GeoKrom/NTUA-Intelligent-Control-Systems-and-Robotic-Systems-course/Exercises/Exercise-4/Assignment 4.pdf

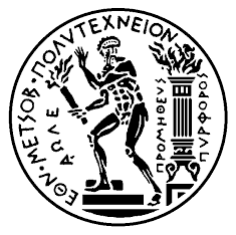
[picture p115: figure]

Εθνικό Μετσόβιο Πολυτεχνείο

Σχολή Μηχανολόγων μηχανικών

ΔΠΜΣ Συστήματα αυτοματισμού

Κατεύθυνση Β: Συστήματα Αυτομάτου Ελέγχου και Ρομποτικής

Μεταπτυχιακό Μάθημα:

Ευφυή Συστήματα Ελέγχου και Ρομποτικής

Ονομ/νυμο - Α.Μ.:

Γεώργιος Κρομμύδας - 02121208

Τέταρτη Σειρά Ασκήσεων: Backstepping and Adaptive Backstepping Control

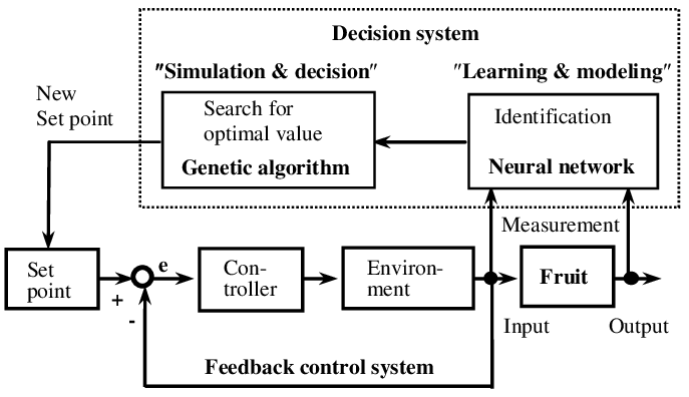
[picture p116: figure]

### Αθήνα, 2024

# Πίνακας Περιεχομένων

Κατάλογος Σχημάτων | | 2
Κατάλογος Πινάκων | | 3
΄Ελεγχος Ρομποτικού Βραχίονα Περιστροφικών Αρθρώσεων | | 4
Ερώτημα 1: Ελεγκτής Ρομποτικού Βραχίονα με την Μέθοδο Οπισθοδρόμησης | . | 5

Ερώτημα 2: Ελεγκτής Ρομποτικού βραχίονα με την Μέθοδο Προσαρμοσικής

Αʹ Κώδικας Προσομοίωσης | 15
Βιβλιογραφία | 25

# Κατάλογος Σχημάτων

1 | Ρομποτικός βραχίονας n βαθμών ελευθερίας | | 4
2 | Ρομποτικός βραχίονας δύο βαθμών ελευθερίας | | 8
3 | Γωνιακή θέση και ταχύτητα στροφικής άρθρωσης q1 | | 11
4 | Γωνιακή θέση και ταχύτητα στροφικής άρθρωσης q2 | | 11
5 | Σφάλματα παρακολούθησης γωνιακών θέσεων και ταχυτήτων στροφικών αρ-
θρώσεων. | | | 12
6 | Γωνιακή θέση και ταχύτητα στροφικής άρθρωσης q1 | | 13
7 | Γωνιακή θέση και ταχύτητα στροφικής άρθρωσης q2 | | 13
8 | Σφάλματα παρακολούθησης γωνιακών θέσεων και ταχυτήτων στροφικών αρ-
θρώσεων. | | | 13
9 | Εκτίμηση παραμέτρων ρομποτικού βραχίονα | | 14

# Κατάλογος Πινάκων

1 | Περιγραφή συμβόλων ρομποτικού βραχίονα | | 8
2 | Τιμές παραμέτρων ρομποτικού βραχίονα | | 10

# ΄Ελεγχος Ρομποτικού Βραχίονα

# Περιστροφικών Αρθρώσεων

Μας δίνεται ένας ρομποτικός βραχίονας n βαθμών ελευθερίας περιστροφικών αρθρώσεων που

περιγράφεται από το ακόλουθο δυναμικό μοντέλο:

M(q)¨q + C(q, q˙) ˙q + G(q) = τ | (1)

όπου τα q, τ ∈ Rn περιγράφουν τις γωνίες και τις ροπές εισόδου κάθε άρθρωσης, M(q) είναι

ο πίνακας μάζας του βραχίονα, C(q, q˙) είναι ο πίνακας φυγόκεντρων και Coriolis δυνάμεων

και ο G(q) αποτελεί το διάνυσμα των βαρυτηκών δυνάμεων (βλ. Σχήμα 1).

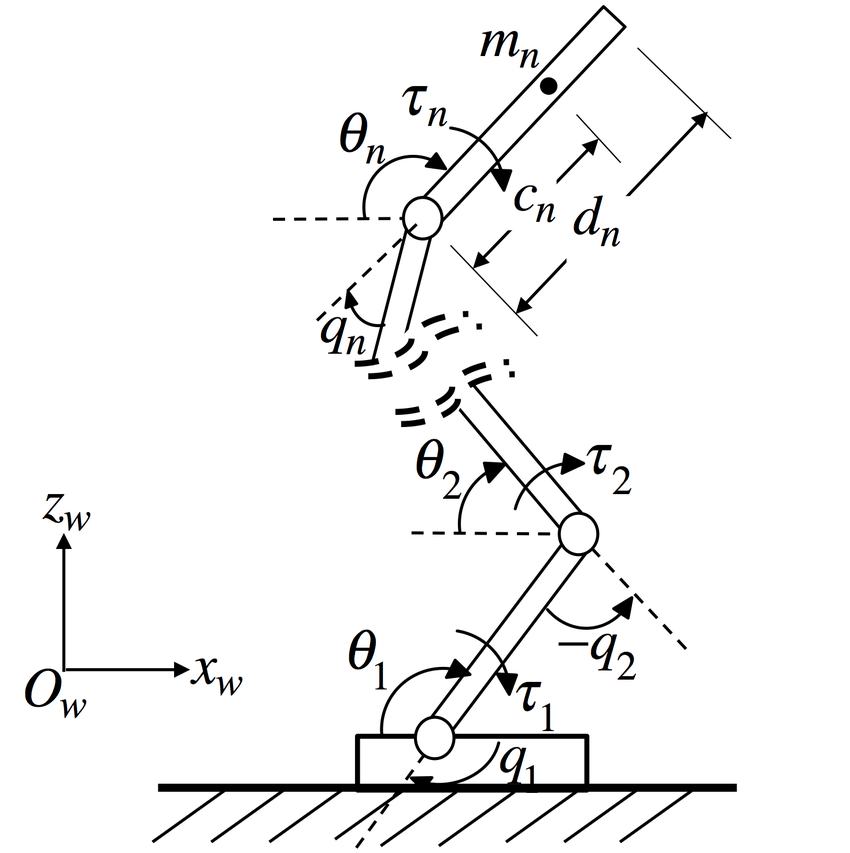
[picture p117: figure]

Σχήμα 1: Ρομποτικός βραχίονας n βαθμών ελευθερίας.

Επιπλέον, ο παραπάνω βραχίονας έχει τις ακόλουθες ιδιότητες:

1. Ο πίνακας M(q) ∈ Rn×n
είναι συμμετρικός και θετικά ορισμένος.
2. Ο πίνακας N(q) := M˙ (q) − 2C(q, q˙) ∈ Rn×n
είναι αντισυμμετρικός και ισχύει
q

T N(q)q = 0.

3. Το δυναμικό μοντέλο της σχέσης (1) του βραχίονα παραμετροποιείται γραμμικά ως εξής:

M(q)¨qr + C(q, q˙) ˙qr + G(q) = Y (q, q,˙ qṙ, q¨r)π

όπου το π ∈ Rm αποτελεί το διάνυσμα των άγνωστων σταθερών παραμέτρων και η Y : Rn×Rn×Rn×Rn → Rn×m είναι μια γνωστή συνάρτηση των παραπάνω σημάτων.

Ερώτημα 1: Ελεγκτής Ρομποτικού Βραχίονα με τη Μέθοδο Οπισθοδρόμησης

Το πρώτο βήμα είναι να μετασχηματίσουμε τη σχέση (1) σε μητρωϊκή μορφή, για να μπο-

ρέσουμε να κάνουμε παρακολούθηση τροχιάς. Συνεπώς, θέτουμε το διάνυσμα κατάστασης
x = [q, q˙]

T
. Οπότε Το σύστημα θα γίνει
x˙ 1
x˙ 2
=
q˙
M⁻¹
(q) (τ − C(q, q˙) ˙q − G(q)) (2)

Η αντιστροφή του πίνακα μάζας έγινε με βάση την ιδιότητά του, ο οποίος είναι θετικά ορι-

σμένος. Καθώς γνωρίζουμε την επιθυμητή τροχιά που θέλουμε να εφαρμόσουμε στο σύστημα,

ορίζουμε τα παρακάτω σφάλματα
e1 = q − qd

e2 = ˙q − qḋ

΄Ετσι, η δυναμική του σφάλματος που θα προκύψει θα είναι η εξής
e˙1
e˙2
=
q˙ − qḋ
q¨− q¨d
=
e2
M⁻¹
(q) (τ − C(q, q˙) ˙q − G(q)) − q¨d

=

e2
M⁻¹
(q) (τ − C(q, q˙) ˙q − G(q)) − M⁻¹
(q) (Y (q, q,˙ q,˙ q¨d)π − C(q, q˙) ˙q − G(q))
e˙1
e˙2
=
e2
M⁻¹
(q) (τ − Y (q, q,˙ q,˙ q¨d)π)
(3)

Συνεπώς, με βάση τη σχέση (3) θα μπορέσουμε να σχεδιάσουμε τον ελεγκτή οπισθο-

δρόμησης. Η αρχική κατάσταση του συστήματος θα είναι z1 = e1. Οπότε

z˙1 = ė1 = e2 = e2 ± K1e1 = −K1z1 + (e2 + K1z1)

όπου ο πίνακας K1 ∈ Rn×n
είναι συμμετρικός και θετικά ορισμένος. Θεωρούμε τη μεταβλη-

τή e2 ως είσοδο ελέγχου στο σύστημα. Για να έχουμε ευστάθεια στην πρώτη κατάσταση, ορίζουμε το e2 = −K1z1. ΄Ετσι θα προκύψει

z˙1 = −K1z1

το οποίο σημαίνει πως θα προκύψει ευστάθεια λόγω του ορισμού του πίνακα K1. ΄Ετσι, θα

ορίσουμε τη νέα μεταβλητή κατάστασης ως z2 = e2 + K1z1. Θα παραγωγίσουμε τη σχέση

αυτή, με αποτέλεσμα να προκύψει

z˙2 = ė2 + K1z˙1 = M⁻¹
(q)(τ − Y (q, q,˙ q,˙ q¨d)π) + K1(z2 − K1z1) | (4)

Οπότε, τώρα θα κάνουμε χρήση της υποψήφιας συνάρτησης Lyapunov

V (z1, z2) = 1
2

z

T
1

z1 +

1
2

z

T
2 M(q)z2 | (5)

Η παραπάνω συνάρτηση παρατηρούμε πως είναι θετικά ορισμένη στο πεδίο ορισμού της και

ακτινικά μη φραγμένη. Οπότε, το επόμενο βήμα είναι να την παραγωγίσουμε

V˙ (z1, z2) = z
T
1

z˙1 +

1
2

z˙

T
2 M(q)z2 +

1
2

z

T

2 M˙ (q)z2 +

1
2

z

T
2 M(q) ż2

= z

T
1

(z2 − K1z1) + 1
2

(M⁻¹
(q)(τ − Y (q, q,˙ q,˙ q¨d)π) + K1(z2 − K1z1))TM(q)z2

+

1
2

z

T

2 M˙ (q)z2 +

1
2

z

T

2 M(q)(M⁻¹
(q)(τ − Y (q, q,˙ q,˙ q¨d)π) + K1(z2 − K1z1))

V˙ (z1, z2) = z
T
1

(z2−K1z1)+z

T

2 M(q)(M⁻¹

(q)(τ−Y (q, q,˙ q,˙ q¨d)π+K1(z2−K1z1))+1 2

z

T

2 M˙ (q)z2

= −z

T
1 K1z1 + z

T
1

z2 + z

T

2 M(q)(M⁻¹

(q)(τ − Y (q, q,˙ q,˙ q¨d)π + K1(z2 − K1z1)) + 1 2

z

T

2 M˙ (q)z2

= −z

T
1 K1z1 + z

T
2

(τ − Y (q, q,˙ q,˙ q¨d)π + z1 + M(q)K1(z2 − K1z1)) + 1 2

z

T

2 M˙ (q)z2

= −z

T
1 K1z1 +z

T
2

(τ −Y (q, q,˙ q,˙ q¨d)π+z1 +M(q)K1(z2 −K1z1))+ 1 2

z

T

2 M˙ (q)z2 ±z
T
2 C(q, q˙)z2

= −z

T
1 K1z1+z

T
2

(τ−Y (q, q,˙ q,˙ q¨d)π+z1+M(q)K1(z2−K1z1))+1 2

z

T
2

(M˙ (q)−C(q, q˙))z2+z
T
2 C(q, q˙)z2

Καθώς ο πίνακας N(q) := 1

2M˙ (q) − C(q, q˙) είναι αντισυμμετρικός, τότε το z T
2 N(q)z2 = 0.

΄Ετσι, η παράγωγος θα πάρει την μορφή

V˙ (z1, z2) = −z
T
1 K1z1 + z

T
2

(τ − Y (q, q,˙ q,˙ q¨d)π + z1 + M(q)K1(z2 − K1z1)) + z

T
2 C(q, q˙)z2

= −z

T
1 K1z1 + z

T
2

(τ − Y (q, q,˙ q,˙ q¨d)π + z1 + C(q, q˙)z2 + M(q)K1(z2 − K1z1))

= −z

T
1 K1z1 + z

T
2

(τ − M(q)(¨qd + K1(z2 − K1z1)) − C(q, q˙)( ˙q − z2) − G(q) + z1)

Επειδή γνωρίζουμε τις παραμέτρους του συστήματος, θα επιλέξουμε τον εξής νόμο ελέγ-

χου

τ = M(q)(¨qd + K1(z2 − K1z1)) − C(q, q˙)( ˙q − z2) + G(q) − z1 − K2z2 | (6)

με τον πίνακα K2 ∈ Rn×n
είναι συμμετρικός και θετικά ορισμένος. Ωστόσο, θα τροποποι-ήσουμε την σχέση (6) ώστε να χρησιμοποιήσουμε την γραμμική παραμετροποίηση. ΄Ετσι θα

ορίσουμε κάποιες ποσότητες που σχετίζονται με το παραμετρικό μοντέλο

qṙ = ˙q − z2 = ˙q − e2 + K1e1 = ˙qd + K1(q − qd)

q¨r = ¨qd + K1(z2 − K1z1) = ¨qd + K1( ˙q − qḋ)

Συνεπώς, ο νόμος ελέγχου που επιλέγεται θα είναι

τ = Y (q, q,˙ qṙ, q¨r)π − z1 − K2z2 | (7)

΄Αρα, η παράγωγος θα γίνει

V˙ (z1, z2) = −z
T
1 K1z1 − z

T
2 K2z2 ≤ 0 | (8)

Από το αποτέλεσμα της σχέσης (8) προκύπτει πως η παράγωγος είναι αρνητικά ορισμένη στο πεδίο ορισμού της με το σημείο ισορροπίας να είναι το (z1, z2) = (0, 0), 0 ∈ Rn
. Επιπλέον,
το σημείο αυτό αντιστοιχεί και στο αρχικό σημείο ισορροπίας (e1, e2) = (0, 0). Συνεπώς,

αυτό που συμπεραίνουμε είναι πως θα έχουμε ολική σταθεροποίηση με τον παραπάνω νόμο

ελέγχου. ΄Ετσι, το σημείο ισορροπίας θα είναι ολικά ασυμπτωτικά ευσταθές και θα έχουμε

σωστή παρακολούθησης της τροχιάς.

Ερώτημα 2: Ελεγκτής Ρομποτικού βραχίονα με τη Μέθοδο Προσαρμοστικής Οπισθοδρόμησης

΄Εστω πως τώρα δε γνωρίζουμε τις παραμέτρους του δυναμικού μοντέλου. Τότε θα ορίσουμε

την προσέγγιση των παραμέτρων ως πˆ. ΄Ετσι, το παραμετρικό σφάλμα σε αυτή την περίπτωση

θα είναι
π˜ = ˆπ − π

Οπότε, ο νέος προσαρμοστικός νόμος ελέγχου θα γίνει

τ = Y (q, q,˙ qṙ, q¨r)ˆπ − z1 − K2z2 | (9)

Η ανάλυση είναι παρόμοια με το προηγούμενο ερώτημα, με τη μόνη διαφορά πως θα τροπο-

ποιηθεί η υποψήφια συνάρτηση Lyapunov . Οπότε η νέα συνάρτηση θα γίνει

V (z1, z2, π˜) = 1
2

z

T
1

z1 +

1
2

z

T
2 M(q)z2 +

1
2

π˜

TΓ

−1
π π˜ | (10)
με τον πίνακα Γπ να είναι συμμετρικός και θετικά ορισμένος πίνακας. | Η παράγωγος της

παραπάνω συνάρτησης θα γίνει μετά από πράξεις

V˙ (z1, z2, π˜) = −z
T
1 K1z1 + z

T
2

(τ − Y (q, q,˙ qṙ, q¨r)π + z1) + ˜π

TΓ

−1
π

˙πˆ

= −z

T
1 K1z1 + z

T
2

(Y (q, q,˙ qṙ, q¨r)ˆπ − z1 − K2z2 − Y (q, q,˙ qṙ, q¨r)π + z1) + ˜π

TΓ

−1
π

˙πˆ

= −z

T
1 K1z1 + z

T
2

(Y (q, q,˙ qṙ, q¨r)(ˆπ − π) − K2z2) + ˜π

TΓ

−1
π

˙πˆ

= −z

T
1 K1z1 − z

T
2 K2z2 + z

T
2 Y (q, q,˙ qṙ, q¨r)˜π + ˜π

TΓ

−1
π

˙πˆ

= −z

T
1 K1z1 − z

T
2 K2z2 + ˜π

T Y (q, q,˙ qṙ, q¨r)

T
z2 + ˜π

TΓ

−1
π

˙πˆ

V˙ (z1, z2, π˜) = −z
T
1 K1z1 − z

T
2 K2z2 + ˜π

T
(Y (q, q,˙ qṙ, q¨r)

T

z2 + Γ⁻¹
π
˙πˆ) | (11)

Με βάσει την σχέση (11) θα επιλέξουμε την εξής προσαρμοστικό νόμο

˙πˆ = −ΓπY (q, q,˙ qṙ, q¨r)
T
z2 | (12)

΄Ετσι, η παράγωγος θα γίνει

V˙ (z1, z2, π˜) = −z
T
1 K1z1 − z

T

2 K2z2 ≤ −λmin(K1)||z1||² − λmin(K2)||z2||² ≤ 0 (13)

Η παράγωγος της V που προέκυψε είναι αρνητικά ημιορισμένη. Η παράγωγος έχει ένα άνω φράγμα το οποίο σημαίνει πως η V˙ ∈ L∞, το οποίο συνεπάγεται πως ότι και τα z1, z2 ∈

L∞. Επιπλέον, καθώς η παράγωγος είναι αρνητικά ημιορισμένη, διαπιστώνουμε πως ότι και η

συνάρτηση V είναι φθίνουσα και μάλιστα θα το όριο της θα είναι πεπερασμένο. Δηλαδή:

lim
t→∞

V (t) = V∞ < ∞

Συνεπώς, έχουμε ότι η V ∈ L∞. Επιπλέον, θα έχουμε πως και το π˜ ∈ L∞. ΄Αρα και η

εκτίμηση θα είναι φραγμένη, πˆ ∈ L∞. Συμπερασματικά, μπορούμε να εγγυηθούμε ασυμπτωτική παρακολούθηση του σφάλματος στο 0 ∈ Rn με τις φραγμένες εκτιμήσεις των παραμέτρων.

΄Ετσι το σημείο ισορροπίας (e1, e2) = (0, 0) θα είναι ολικά ασυμπτωτικά ευσταθές.

Ερώτημα 3: Προσομοίωση Ρομποτικού Βραχίονα 2 Βαθ-

μών Ελευθεριάς

Στην περίπτωση που έχουμε δύο βαθμούς ελευθερίας, το δυναμικό μοντέλο θα γίνει:

M(q)¨q + C(q, q˙) ˙q + G0(q) = τ
"
Iz1 + Iz2 + m1

l

2
1

4 + m2(l

2
1 +

l

2
2

4 + l1l2c2) Iz2 + m2(

l

2
2

4 +

1/2 l1l2c2)
Iz2 + m2(

l

2
2

4 +

1/2 l1l2c2) | Iz2 + m2

l

2
2
4
q¨1
q¨2
+
−cq˙2 + k1 | −c( ˙q1 + ˙q2)
cq˙1 | k2

q˙1
q˙2

+

1
2m1gl1c1 + m2g(l1c1 +

1
2

l2c12)
1
2m2gl2c12 |
=
τ1
τ2

όπου κάθε στοιχείο της εξίσωσης παρουσιάζεται στον πίνακα 1.

Σύμβολο | Περιγραφή
qi | Γωνιακή Θέση i-οστης άρθρωσης (rad)
q˙i | Γωνιακή Ταχύτητα i-οστης άρθρωσης (rad/sec)
τi | Εφαρμοσμένη Ροπή στην i-οστη άρθρωση (Nm)
mi | Μάζα i-οστου συνδέσμου (kg)
li | Μήκος i-οστου συνδέσμου (m)
IZi | Ροπή Αδράνειας i-οστου συνδέσμου (kgm² )
ki | Συντελεστής Ιξώδους Τριβής i-οστου συνδέσμου (kgm²/sec)
g | Επιτάχυνση της Βαρύτητας (m/sec² )

Πίνακας 1: Περιγραφή συμβόλων ρομποτικού βραχίονα.

και έχουμε και τις παρακάτω θεωρήσεις c =

1
2m2l1l2s2, c1 = cos(q1), c2 = cos(q2),

c12 = cos(q1 + q2), s1 = sin(q1), s2 = sin(q2). Επίσης, οπτικά βλέπουμε και τον ρομποτικό

βραχίονα στο σχήμα 2.

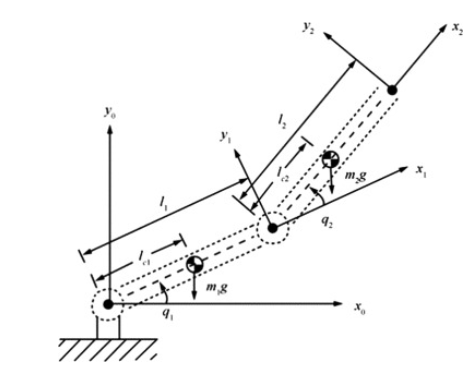
[picture p118: figure]

Σχήμα 2: Ρομποτικός βραχίονας δύο βαθμών ελευθερίας.

Παραμετροποίηση Ρομποτικού Βραχίονα

Η δυναμική εξίσωση ενός ρομποτικού βραχίονα μπορεί να αναπαρασταθεί παραμετρικά με την εξής μορφή
M(q)¨qr + C(q, q˙) ˙qr + G0(q) = Y (q, q,˙ qṙ, q¨r)π | (14)

Θα πρέπει να βρούμε τον πίνακα Y και το διάνυσμα π που αναπαριστούν την παραμετρική μορφή

του βραχίονα. ΄Ετσι θα μπορέσουμε να εφαρμόσουμε και τους παραπάνω νόμους ελέγχου που

σχεδιάστηκαν. Θα πάρουμε κάθε όρο της εξίσωσης και θα τον αναλύσουμε σε δύο πίνακες,

όπου ο ένας θα εξαρτάται από τις γωνίες του βραχίονα και ο άλλος από τις παραμέτρους του.

Ας αναλύσουμε πρώτα τον πίνακα μάζας με το επιθυμητό σήμα επιτάχυνσης. Οπότε, έχουμε

M(q)¨qr =

"
Iz1 + Iz2 + m1

l

2
1

4 + m2(l

2
1 +

l

2
2

4 + l1l2c2) Iz2 + m2(

l

2
2

4 +

1/2 l1l2c2)
Iz2 + m2(

l

2
2

4 +

1/2 l1l2c2) | Iz2 + m2

l

2
2
4
q¨r1
q¨r2

=

"
(Iz1 + Iz2 + m1

l

2
1

4 + m2(l

2
1 +

l

2
2

4 + l1l2c2))¨qr1 + (Iz2 + m2(

l

2
2

4 +

1/2 l1l2c2)¨qr2
(Iz2 + m2(

l

2
2

4 +

1/2 l1l2c2))¨qr1 + (Iz2 + m2

l

2
2/4)¨qr2

=

"
(Iz1 + m1

l

2
1

4 + m2l

2/1)¨qr1 + (Iz2 + m2

l

2
2/4)(¨qr1 + ¨qr2

) + ( ¹
2

l1l2)c2(2¨qr1 + ¨qr2

)
0¨qr1 + (Iz2 + m2

l

2
2/4)(¨qr1 + ¨qr2

) + ( ¹
2m2l1l2)c2q¨r1

M(q)¨qr =

q¨r1

q¨r1 + ¨qr2

c2(2¨qr1 + ¨qr2

)
0 ¨qr1 + ¨qr2

c2q¨r1

Iz1 + m1

l

2
1

4 + m2l

2
1
Iz2 + m2

l

2
2
4
1
2m2l1l2

- (15)

Το επόμενο βήμα είναι να αναλύσουμε τον πίνακα των φυγόκεντρων - Coriolis δυνάεμων. ΄Αρα, έχουμε ότι

C(q, q˙) ˙qr =

−cq˙2 + k1 | −c( ˙q1 + ˙q2)
cq˙1 | k2

qṙ1
qṙ2

=

(−

1
2m2l1l2s2q˙2 + k1) ˙qr1 −

1
2m2l1l2s2( ˙q1 + ˙q2) ˙qr2
1
2m2l1l2s2q˙1qṙ1 + k2qṙ2

=

−

1
2m2l1l2s2( ˙q2qṙ1 + ( ˙q1 + ˙q2) ˙qr2

) + k1qṙ1 + 0k2
1
2m2l1l2(s2q˙1qṙ1

) + 0k1 + k2qṙ2

C(q, q˙) ˙qr =

−s2( ˙q2qṙ1 + ( ˙q1 + ˙q2) ˙qr2

) ˙qr1
0
s2q˙1qṙ1

0 ˙qr2

1
2m2l1l2
k1
k2
- (16)

Τέλος, θα αναλύσουμε και το διάνυσμα της βαρύτητας του βραχίονα. Οπότε ισχύει ότι

G0(q) = 1
2m1gl1c1 + m2g(l1c1 +

1
2

l2c12
1
2m2gl2c12 |
=
(

1
2m1gl1 + m2gl1)c1 +

1
2m2gl2c12
0( ¹

2m1gl1 + m2gl1) + 1

2m2gl2c12

G0(q) =
c1 | c12
0 | c12 1
2m1gl1 + m2gl1
1
2m2gl2
(17)

Συνεπώς, συνδυάζοντας τις σχέσεις (15) (16) και (17) μπορούμε να βρούμε μια παραμε-

τρική έκφραση του βραχίονα, με τον πίνακα Y να εξαρτάται μόνο από τις μεταβλητές των

αρθρώσεων και το διάνυσμα π που εξαρτάται από τις παραμέτρους του βραχίονα. Οπότε, έχουμε

Y (q, q,˙ qṙ, q¨r) =
q¨r1

q¨r1 + ¨qr2

c2(2¨qr1 + ¨qr2

) − s2( ˙q2qṙ1 + ( ˙q1 + ˙q2) ˙qr2

) ˙qr1
0 | c1 | c12
0 | ¨qr1 + ¨qr2

c2q¨r1 + s2q˙1qṙ1

0 | ˙qr2
| 0 | c12

π =

Iz1 + m1

l

2
1

4 + m2l

2
1
Iz2 + m2

l

2
2
4
1
2m2l1l2
k1
k2
1
2m1gl1 + m2gl1
1
2m2gl2

Προσομοίωση Ρομποτικού Βραχίονα

Με την επίτευξη της παραμετροποίησης του βραχίονα, μπορούμε να προσομοιώσουμε τα δύο

παραπάνω σχήματα ελέγχου. Θα εφαρμόσουμε δύο ημιτονοειδές τροχιές στο σύστημα και θα

δούμε πως αποκρύνονται οι αρθρώσεις. Οι επιθμητές τροχιές που θα προσομοιώσουμε είναι

οι εξής:
Για την πρώτη στροφική άρθρωση με αρχική συνθήκη q1(0) = 80π
180 :

q1d

(t) = 90π
180

+

30π
180

cos(t)

q˙1d

(t) = −

30π
180

sin(t)

q¨1d

(t) = −

30π
180

cos(t)

Για την δεύετρη στροφική άρθρωση με αρχική συνθήκη q1(0) = 130π 180 :

q2d

(t) = 90π
180

−

30π
180

sin(t)

q˙2d

(t) = −

30π
180

cos(t)

q¨2d

(t) = −

30π
180

sin(t)

Με την εφαρμογή των παραπάνω τροχιών θα μπορέσουμε να δούμε την απόκριση του

βραχίονα. Επίσης, στον πίνακα 2 βλέπουμε τις τιμές που έχουν οι παράμετροι του συστήματος.

Παράμετρος | Τιμή
m1 | 3.2 (kg)
l1 | 0.5 (m)
IZ1 | 0.96 (kgm² )
k1 | 1 (kgm²/sec)
m2 | 2.0 (kg)
l1 | 0.4 (m)
IZ1 | 0.81 (kgm² )
k1 | 1 (kgm²/sec)
g | 9.81 (m/sec² )

Πίνακας 2: Τιμές παραμέτρων ρομποτικού βραχίονα

Επομένως, το επόμενο βήμα είναι να προσομοιώσουμε τα δύο αυτά σχήματα.

Προσομοίωση Ελεγκτή Οπισθοδρόμησης

Ο πρώτος ελεγκτής που εφαρμόστηκε στο σύστημα είναι αυτός της οπισθοδρόμησης. Ως

κέρδη του ελεγκτή επιλέχθηκαν τα K1 =

3.5 | 0
0 | 0.8
και K2 =
15 | 0
0 | 15
. Η συγκεκριμένη

επιλογή έγινε μετά από προσομοιώσεις, καθώς η επιλογή των μεγάλων κερδών στο K1 είχε

σοβαρές επιπτώσεις στη σωστή παρακολούθηση. ΄Ετσι, οι τιμές του είναι μικρές για να μην

υπάρχουν αποκλίσεις κατά την εφαρμογή των εισόδων. Αντιθέτως, ο πίνακας K2 χρειάστηκε

μεγάλες τιμές για να μπορέσουν οι ταχύτητες να παρακολουθήσουν σωστά τις επιθυμητές

τροχιές.

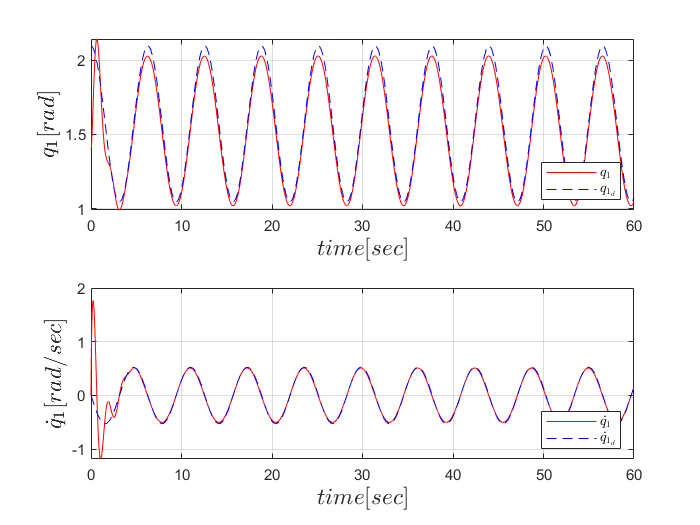
[picture p119: figure]

Σχήμα 3: Γωνιακή θέση και ταχύτητα στροφικής άρθρωσης q1.

Στο σχήμα 3 παρατηρούμε την απόκριση της πρώτης άρθρωσης. Η άρθρωση παρακολουθεί

σωστά και ασυμπτωτικά την επιθυμητή τροχιά που της τέθηκε. Επίσης, το ίδιο ισχύει και για τη δεύτερη άρθρωση (βλ. σχήμα 4).

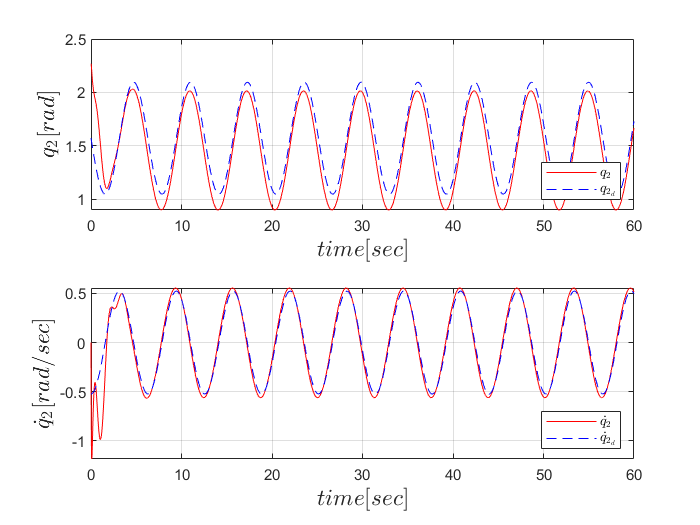
[picture p120: figure]

Σχήμα 4: Γωνιακή θέση και ταχύτητα στροφικής άρθρωσης q2.

Τέλος, στο σχήμα 5 βλέπουμε τα σφάλματα παρακολούθησης των αρθρώσεων. Βλέπουμε

πως όλα τα σφάλματα συγκλίνουν ασυμπτωτικά στο μηδέν, με αποτέλεσμα να αποδεικνύεται

και οπτικά η ολική ασυμπτωτική ευστάθεια του συστήματος.

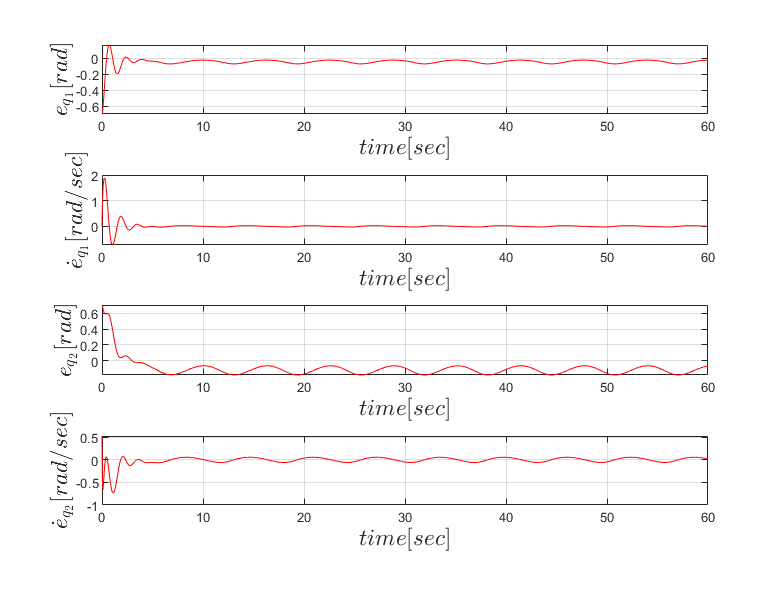
[picture p121: figure]

Σχήμα 5: Σφάλματα παρακολούθησης γωνιακών θέσεων και ταχυτήτων στροφικών αρθρώσε-

ων.

Προσομοίωση Ελεγκτή Προσαρμοστικής Οπισθοδρόμησης

Ο δεύτερος ελεγκτής που σχεδιάστηκε είναι αυτός της προσαρμοστικής οπισθοδρόμησης. Σε

αυτή την περίπτωση δε γνωρίζουμε το διάνυσμα των παραμέτρων π. ΄Ετσι, θα χρησιμοποιηθεί

ο νόμος προσαρμογής που αποδείχθηκε προηγουμένως. Ο πίνακας κερδών των παραμέτρων

επιλέχθηκε ως Γπ = 5I7. Τα υπόλοιπα κέρδη του ελεγκτή επιλέχθηκαν ως K1 =

4 0

0 4
και

K2 =

8 0

0 12
. Η επιλογή αυτών των τιμών έγινε μετά από πλήθος προσομοιώσεων, έτσι ώστε

να έχουμε και σωστή παρακολούθηση των κερδών αλλά και οι εκτιμήσεις των παραμέτρων

να συγκλίνουν κοντά στις ιδανικές τιμές των παραμέτρων του βραχίονα. Στα σχήματα 6

και 7 παρατηρούμε την απόκριση των δύο στροφικών αρθρώσεων. Αυτό που παρατηρούμε

είναι πως οι αρθρώσεις παρακολουθούν σωστά τις επιθυμητές τροχιές με λιγότερα σφάλματα.

Επίσης, παρατηρούμε τα σφάλματα παρακολούθησης να συγκλίνουν ασυμπτωτικά στο μηδέν
(βλ. | σχήμα 8). | Αυτό οφείλεται στο γεγονός πως οι εκτιμήσεις μας είναι φραγμένες και

συγκλίνουν κοντά στις ιδανικές τιμές όπως παρατηρείται και στο σχήμα 9.

Τέλος, αυτό που συμπεραίνουμε είναι πως και τα δύο σχήματα ελέγχου έχουν αξιοποιηθεί

σωστά και παράχθηκαν τα επιθυμητά αποτελέσματα. ΄Εχουμε και στις δύο περιπτώσεις ασυμ-

πτωτική παρακολούθηση της τροχιάς, με τα σήματα του κλειστού βρόχου να είναι φραγμένα.

΄Ετσι, οι αρθρώσεις του βραχίονα προσομοίωσαν σωστά τις τροχιές που τους ανατέθηκαν, με

μικρές απώλειες ενέργειας κατά την εκτέλεση της κίνησής του.

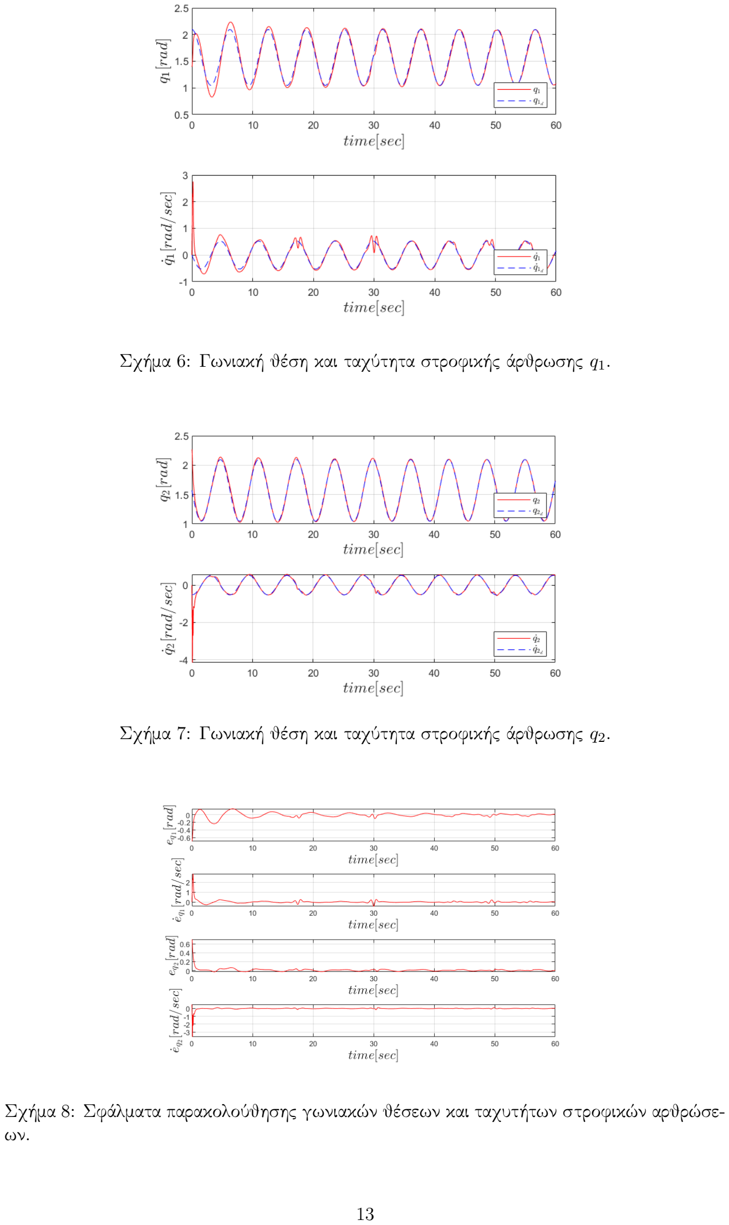
[picture p122: page 15]

Σχήμα 6: Γωνιακή θέση και ταχύτητα στροφικής άρθρωσης q1.

Σχήμα 7: Γωνιακή θέση και ταχύτητα στροφικής άρθρωσης q2.

Σχήμα 8: Σφάλματα παρακολούθησης γωνιακών θέσεων και ταχυτήτων στροφικών αρθρώσε-

ων.

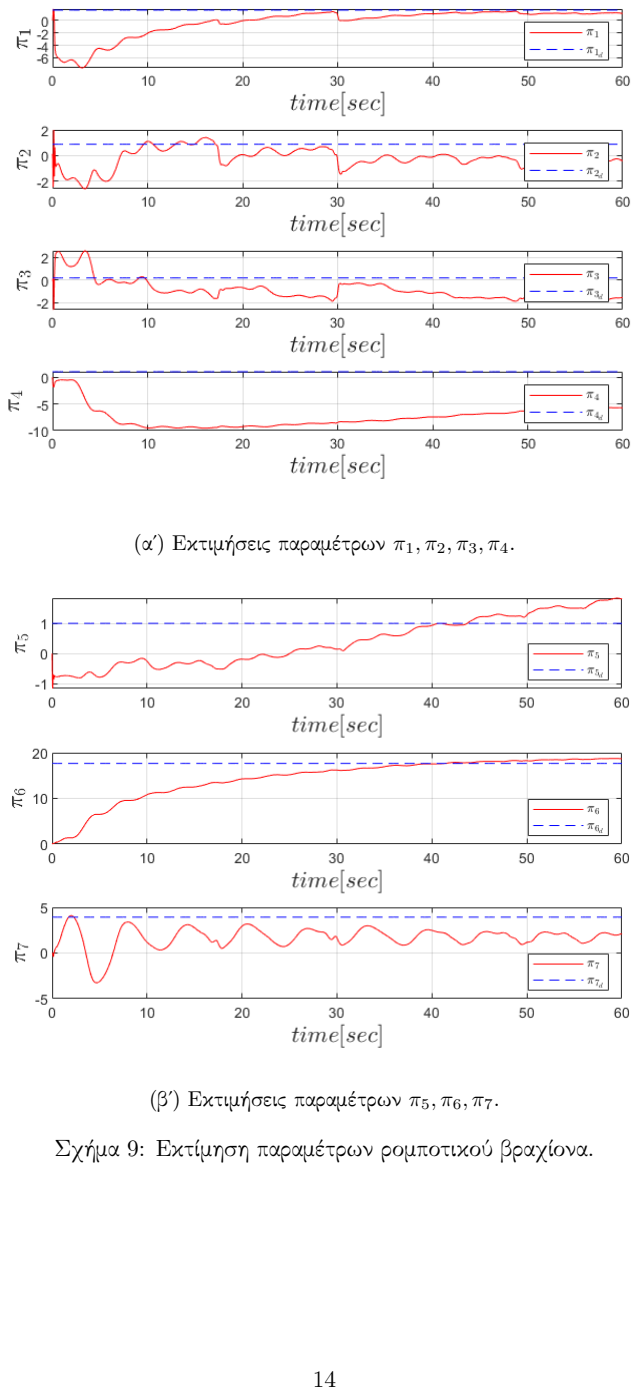
[picture p123: page 16]

(αʹ) Εκτιμήσεις παραμέτρων π1, π2, π3, π4.

(βʹ) Εκτιμήσεις παραμέτρων π5, π6, π7.

Σχήμα 9: Εκτίμηση παραμέτρων ρομποτικού βραχίονα.

## Παράρτημα Αʹ

# Κώδικας Προσομοίωσης

Στο παράρτημα αυτό παρουσιάζεται ο πηγαίος κώδικας που χρησιμοποιήθηκες για την προσο-

μοίωση των δύο ελεγκτών.

%% Two DoF Robo tic Manipula to r B ack s teppin g and Adaptive B ack s teppin g C on t r ol
% | Assignment 4
% | Name: George Krommydas
% | A.M. : 02121208

c l e a r ;
c l c ;

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

%% Parameter S e t ti n g

m1 = 3 . 2 ; | % kg
l 1 = 0 . 5 ; | % m
I z 1 = 0 . 9 6 ; | % kg mˆ2
k1 = 1 ; | % kg mˆ2/ s e c
m2 = 2 . 0 ; | % kg
l 2 = 0 . 4 ; | % m
I z 2 = 0 . 8 1 ; | % kg mˆ2
k2 = 1 ; | % kg mˆ2/ s e c
g = 9 . 8 1 ; | % m/ s ˆ2
t s t a r t = 0 ; | % s e c
tend = 6 0; | % s e c
t sp an = [ t s t a r t , tend ] ;
q 1 0 = 80∗ pi / 1 8 0;

q 2 0 = 130∗ pi / 1 8 0;
x0 = [ q 1 0 ; q 2 0 ; 0 ; 0 ] ;
p a rv a r = [ I z 1+m1∗( l 1 ˆ2/4)+m2∗ l 1 ˆ 2; I z 2 + m2∗( l 2 ˆ 2 / 4 );
0. 5 ∗m2∗ l 1 ∗ l 2 ;
k1 ;
k2 ;
0. 5 ∗m1∗g∗ l 1+m2∗g∗ l 1 ;
0. 5 ∗m2∗g∗ l 2 ] ;
% Sim ul a ti o n

[ t , x ] = ode45 ( @BacksteppingControl , tspan , x0 ) ;

q1 d = 90∗ pi /180 + ( 3 0∗ pi / 1 8 0 )∗ c o s ( t ) ;
q 1 d o t d = −(30∗ pi / 1 8 0 )∗ s i n ( t ) ;
q 1 dd o t d = −(30∗ pi / 1 8 0 )∗ c o s ( t ) ;
q2 d = 90∗ pi /180 − ( 3 0∗ pi / 1 8 0 )∗ s i n ( t ) ; q 2 d o t d = −(30∗ pi / 1 8 0 )∗ c o s ( t ) ;
q 2 dd o t d = ( 3 0∗ pi / 1 8 0 )∗ s i n ( t ) ;

% Pl o t s
f i g u r e ( 1 ) ;
c l f ;

s u b pl o t ( 2 , 1 , 1 ) ;
pl o t ( t , x ( : , 1 ) , ’ r − ’ );
h old on ;
pl o t ( t , q1 d , ’ b−−’);
x l a b e l ( ’ $time [ s e c ] $ ’ , ’ I n t e r p r e t e r ’ , ’ l a t e x ’ , ’ Fon tSize ’ , 1 4 ) ; y l a b e l ( ’ $q 1 [ rad ] $ ’ , ’ I n t e r p r e t e r ’ , ’ l a t e x ’ , ’ Fon tSize ’ , 1 4 ) ; g ri d on ;
l e g e n d ( ’ $q 1$ ’ , ’ $q {1 d }$ ’ , ’ I n t e r p r e t e r ’ ,
’ l a t e x ’ , L o c a ti o n =’ s o u t h e a s t ’ ) ;

s u b pl o t ( 2 , 1 , 2 ) ;
pl o t ( t , x ( : , 3 ) , ’ r − ’ );
h old on ;
pl o t ( t , q 1 d o t d , ’ b−−’);
x l a b e l ( ’ $time [ s e c ] $ ’ , ’ I n t e r p r e t e r ’ , ’ l a t e x ’ , ’ Fon tSize ’ , 1 4 ) ;
y l a b e l ( ’ $\ dot {q} 1 [ rad / s e c ] $ ’ , ’ I n t e r p r e t e r ’ , ’ l a t e x ’ , ’ Fon tSize ’ , 1 4 ) ; g ri d on ;
l e g e n d ( ’ $\ dot {q} 1$ ’ , ’ $\ dot {q} {1 d }$ ’ , ’ I n t e r p r e t e r ’ ,
’ l a t e x ’ , L o c a ti o n =’ s o u t h e a s t ’ ) ;

f i g u r e ( 2 ) ;
c l f ;

s u b pl o t ( 2 , 1 , 1 ) ;
pl o t ( t , x ( : , 2 ) , ’ r − ’ ); h old on ;
pl o t ( t , q2 d , ’ b−−’);

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

s u b pl o t ( 2 , 1 , 2 ) ;
pl o t ( t , x ( : , 4 ) , ’ r − ’ );
h old on ;
pl o t ( t , q 2 d o t d , ’ b−−’);
x l a b e l ( ’ $time [ s e c ] $ ’ , ’ I n t e r p r e t e r ’ , ’ l a t e x ’ , ’ Fon tSize ’ , 1 4 ) ; y l a b e l ( ’ $\ dot {q} 2 [ rad / s e c ] $ ’ , ’ I n t e r p r e t e r ’ ,
’ l a t e x ’ , ’ Fon tSize ’ , 1 4 ) ;
g ri d on ;
l e g e n d ( ’ $\ dot {q} 2$ ’ , ’ $\ dot {q} {2 d }$ ’ , ’ I n t e r p r e t e r ’ , ’ l a t e x ’ , L o c a ti o n =’ s o u t h e a s t ’ ) ;

f i g u r e ( 3 ) ;
c l f ;

s u b pl o t ( 4 , 1 , 1 ) ;
pl o t ( t , x ( : , 1 ) − q1 d , ’ r − ’ );
x l a b e l ( ’ $time [ s e c ] $ ’ , ’ I n t e r p r e t e r ’ , ’ l a t e x ’ , ’ Fon tSize ’ , 1 4 ) ;
y l a b e l ( ’ $ e { q 1 } [ rad ] $ ’ , ’ I n t e r p r e t e r ’ , ’ l a t e x ’ , ’ Fon tSize ’ , 1 4 ) ; g ri d on ;

s u b pl o t ( 4 , 1 , 2 ) ;
pl o t ( t , x ( : , 3 ) − q 1 d o t d , ’ r − ’ );
x l a b e l ( ’ $time [ s e c ] $ ’ , ’ I n t e r p r e t e r ’ , ’ l a t e x ’ , ’ Fon tSize ’ , 1 4 ) ; y l a b e l ( ’ $\ dot { e } { q 1 } [ rad / s e c ] $ ’ , ’ I n t e r p r e t e r ’ ,
’ l a t e x ’ , ’ Fon tSize ’ , 1 4 ) ;
g ri d on ;

s u b pl o t ( 4 , 1 , 3 ) ;
pl o t ( t , x ( : , 2 ) − q2 d , ’ r − ’ );
x l a b e l ( ’ $time [ s e c ] $ ’ , ’ I n t e r p r e t e r ’ , ’ l a t e x ’ , ’ Fon tSize ’ , 1 4 ) ; y l a b e l ( ’ $ e { q 2 } [ rad ] $ ’ , ’ I n t e r p r e t e r ’ ,
’ l a t e x ’ , ’ Fon tSize ’ , 1 4 ) ;
g ri d on ;

s u b pl o t ( 4 , 1 , 4 ) ;
pl o t ( t , x ( : , 4 ) − q 2 d o t d , ’ r − ’ );
x l a b e l ( ’ $time [ s e c ] $ ’ , ’ I n t e r p r e t e r ’ , ’ l a t e x ’ , ’ Fon tSize ’ , 1 4 ) ; y l a b e l ( ’ $\ dot { e } { q 2 } [ rad / s e c ] $ ’ , ’ I n t e r p r e t e r ’ ,
’ l a t e x ’ , ’ Fon tSize ’ , 1 4 ) ;
g ri d on ;

% Sim ul a ti o n Adaptive B ack s teppin g
x01 = [ x0 ; z e r o s ( s i z e ( p a rv a r ) ) ] ;
[ t1 , x1 ] = ode45 ( @AdaptiveBacksteppingControl , tspan , x01 ) ;

q1 d = 90∗ pi /180 + ( 3 0∗ pi / 1 8 0 )∗ c o s ( t 1 ) ; q 1 d o t d = −(30∗ pi / 1 8 0 )∗ s i n ( t 1 ) ;
q 1 dd o t d = −(30∗ pi / 1 8 0 )∗ c o s ( t 1 ) ;
q2 d = 90∗ pi /180 − ( 3 0∗ pi / 1 8 0 )∗ s i n ( t 1 ) ; q 2 d o t d = −(30∗ pi / 1 8 0 )∗ c o s ( t 1 ) ;
q 2 dd o t d = ( 3 0∗ pi / 1 8 0 )∗ s i n ( t 1 ) ;

% Pl o t s
f i g u r e ( 4 ) ;
c l f ;

s u b pl o t ( 2 , 1 , 1 ) ;
pl o t ( t1 , x1 ( : , 1 ) , ’ r − ’ );
h old on ;
pl o t ( t1 , q1 d , ’ b−−’);
x l a b e l ( ’ $time [ s e c ] $ ’ , ’ I n t e r p r e t e r ’ , ’ l a t e x ’ , ’ Fon tSize ’ , 1 4 ) ; y l a b e l ( ’ $q 1 [ rad ] $ ’ , ’ I n t e r p r e t e r ’ , ’ l a t e x ’ , ’ Fon tSize ’ , 1 4 ) ; g ri d on ;
l e g e n d ( ’ $q 1$ ’ , ’ $q {1 d }$ ’ , ’ I n t e r p r e t e r ’ ,
’ l a t e x ’ , L o c a ti o n =’ s o u t h e a s t ’ ) ;

s u b pl o t ( 2 , 1 , 2 ) ;
pl o t ( t1 , x1 ( : , 3 ) , ’ r − ’ );
h old on ;
pl o t ( t1 , q 1 d o t d , ’ b−−’);
x l a b e l ( ’ $time [ s e c ] $ ’ , ’ I n t e r p r e t e r ’ , ’ l a t e x ’ , ’ Fon tSize ’ , 1 4 ) ;
y l a b e l ( ’ $\ dot {q} 1 [ rad / s e c ] $ ’ , ’ I n t e r p r e t e r ’ , ’ l a t e x ’ , ’ Fon tSize ’ , 1 4 ) ; g ri d on ;
l e g e n d ( ’ $\ dot {q} 1$ ’ , ’ $\ dot {q} {1 d }$ ’ , ’ I n t e r p r e t e r ’ ,
’ l a t e x ’ , L o c a ti o n =’ s o u t h e a s t ’ ) ;

f i g u r e ( 5 ) ;
c l f ;

s u b pl o t ( 2 , 1 , 1 ) ;
pl o t ( t1 , x1 ( : , 2 ) , ’ r − ’ );
h old on ;
pl o t ( t1 , q2 d , ’ b−−’);
x l a b e l ( ’ $time [ s e c ] $ ’ , ’ I n t e r p r e t e r ’ , ’ l a t e x ’ , ’ Fon tSize ’ , 1 4 ) ; y l a b e l ( ’ $q 2 [ rad ] $ ’ , ’ I n t e r p r e t e r ’ , ’ l a t e x ’ , ’ Fon tSize ’ , 1 4 ) ; g ri d on ;
l e g e n d ( ’ $q 2$ ’ , ’ $q {2 d }$ ’ , ’ I n t e r p r e t e r ’ ,
’ l a t e x ’ , L o c a ti o n =’ s o u t h e a s t ’ ) ;

s u b pl o t ( 2 , 1 , 2 ) ;
pl o t ( t1 , x1 ( : , 4 ) , ’ r − ’ );
h old on ;
pl o t ( t1 , q 2 d o t d , ’ b−−’);
x l a b e l ( ’ $time [ s e c ] $ ’ , ’ I n t e r p r e t e r ’ , ’ l a t e x ’ , ’ Fon tSize ’ , 1 4 ) ;
y l a b e l ( ’ $\ dot {q} 2 [ rad / s e c ] $ ’ , ’ I n t e r p r e t e r ’ , ’ l a t e x ’ , ’ Fon tSize ’ , 1 4 ) ;

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

f i g u r e ( 6 ) ;
c l f ;

s u b pl o t ( 4 , 1 , 1 ) ;
pl o t ( t1 , x1 ( : , 1 ) − q1 d , ’ r − ’ );
x l a b e l ( ’ $time [ s e c ] $ ’ , ’ I n t e r p r e t e r ’ , ’ l a t e x ’ , ’ Fon tSize ’ , 1 4 ) ;
y l a b e l ( ’ $ e { q 1 } [ rad ] $ ’ , ’ I n t e r p r e t e r ’ , ’ l a t e x ’ , ’ Fon tSize ’ , 1 4 ) ; g ri d on ;

s u b pl o t ( 4 , 1 , 2 ) ;
pl o t ( t1 , x1 ( : , 3 ) − q 1 d o t d , ’ r − ’ );
x l a b e l ( ’ $time [ s e c ] $ ’ , ’ I n t e r p r e t e r ’ , ’ l a t e x ’ , ’ Fon tSize ’ , 1 4 ) ; y l a b e l ( ’ $\ dot { e } { q 1 } [ rad / s e c ] $ ’ , ’ I n t e r p r e t e r ’ ,
’ l a t e x ’ , ’ Fon tSize ’ , 1 4 ) ;
g ri d on ;

s u b pl o t ( 4 , 1 , 3 ) ;
pl o t ( t1 , x1 ( : , 2 ) − q2 d , ’ r − ’ );
x l a b e l ( ’ $time [ s e c ] $ ’ , ’ I n t e r p r e t e r ’ , ’ l a t e x ’ , ’ Fon tSize ’ , 1 4 ) ; y l a b e l ( ’ $ e { q 2 } [ rad ] $ ’ , ’ I n t e r p r e t e r ’ ,
’ l a t e x ’ , ’ Fon tSize ’ , 1 4 ) ;
g ri d on ;

s u b pl o t ( 4 , 1 , 4 ) ;
pl o t ( t1 , x1 ( : , 4 ) − q 2 d o t d , ’ r − ’ );
x l a b e l ( ’ $time [ s e c ] $ ’ , ’ I n t e r p r e t e r ’ , ’ l a t e x ’ , ’ Fon tSize ’ , 1 4 ) ; y l a b e l ( ’ $\ dot { e } { q 2 } [ rad / s e c ] $ ’ , ’ I n t e r p r e t e r ’ ,
’ l a t e x ’ , ’ Fon tSize ’ , 1 4 ) ;
g ri d on ;

f i g u r e ( 7 ) ;
c l f ;

s u b pl o t ( 4 , 1 , 1 ) ;
pl o t ( t1 , x1 ( : , 5 ) , ’ r − ’ );
h old on ;
pl o t ( t1 , p a rv a r ( 1 ) . ∗ one s ( s i z e ( t 1 ) ) , ’ b−−’);
x l a b e l ( ’ $time [ s e c ] $ ’ , ’ I n t e r p r e t e r ’ , ’ l a t e x ’ , ’ Fon tSize ’ , 1 4 ) ; y l a b e l ( ’ $\ pi 1$ ’ , ’ I n t e r p r e t e r ’ ,
’ l a t e x ’ , ’ Fon tSize ’ , 1 4 ) ;
g ri d on ;
l e g e n d ( ’ $\ pi 1$ ’ , ’ $\ p i {1 d }$ ’ , ’ I n t e r p r e t e r ’ , ’ l a t e x ’ , L o c a ti o n =’ s o u t h e a s t ’ ) ;

s u b pl o t ( 4 , 1 , 2 ) ;
pl o t ( t1 , x1 ( : , 6 ) , ’ r − ’ );
h old on ;

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

s u b pl o t ( 4 , 1 , 3 ) ;
pl o t ( t1 , x1 ( : , 7 ) , ’ r − ’ );
h old on ;
pl o t ( t1 , p a rv a r ( 3 ) . ∗ one s ( s i z e ( t 1 ) ) , ’ b−−’);
x l a b e l ( ’ $time [ s e c ] $ ’ , ’ I n t e r p r e t e r ’ , ’ l a t e x ’ , ’ Fon tSize ’ , 1 4 ) ;
y l a b e l ( ’ $\ pi 3$ ’ , ’ I n t e r p r e t e r ’ , ’ l a t e x ’ , ’ Fon tSize ’ , 1 4 ) ;
g ri d on ;
l e g e n d ( ’ $\ pi 3$ ’ , ’ $\ p i {3 d }$ ’ , ’ I n t e r p r e t e r ’ , ’ l a t e x ’ , L o c a ti o n =’ s o u t h e a s t ’ ) ;

s u b pl o t ( 4 , 1 , 4 ) ;
pl o t ( t1 , x1 ( : , 8 ) , ’ r − ’ );
h old on ;
pl o t ( t1 , p a rv a r ( 4 ) . ∗ one s ( s i z e ( t 1 ) ) , ’ b−−’);
x l a b e l ( ’ $time [ s e c ] $ ’ , ’ I n t e r p r e t e r ’ , ’ l a t e x ’ , ’ Fon tSize ’ , 1 4 ) ; y l a b e l ( ’ $\ pi 4$ ’ , ’ I n t e r p r e t e r ’ ,
’ l a t e x ’ , ’ Fon tSize ’ , 1 4 ) ;
g ri d on ;
l e g e n d ( ’ $\ pi 4$ ’ , ’ $\ p i {4 d }$ ’ , ’ I n t e r p r e t e r ’ , ’ l a t e x ’ , L o c a ti o n =’ s o u t h e a s t ’ ) ;

f i g u r e ( 8 ) ;
c l f ;

s u b pl o t ( 3 , 1 , 1 ) ;
pl o t ( t1 , x1 ( : , 9 ) , ’ r − ’ );
h old on ;
pl o t ( t1 , p a rv a r ( 5 ) . ∗ one s ( s i z e ( t 1 ) ) , ’ b−−’);
x l a b e l ( ’ $time [ s e c ] $ ’ , ’ I n t e r p r e t e r ’ , ’ l a t e x ’ , ’ Fon tSize ’ , 1 4 ) ; y l a b e l ( ’ $\ pi 5$ ’ , ’ I n t e r p r e t e r ’ ,
’ l a t e x ’ , ’ Fon tSize ’ , 1 4 ) ;
g ri d on ;
l e g e n d ( ’ $\ pi 5$ ’ , ’ $\ p i {5 d }$ ’ , ’ I n t e r p r e t e r ’ , ’ l a t e x ’ , L o c a ti o n =’ s o u t h e a s t ’ ) ;

s u b pl o t ( 3 , 1 , 2 ) ;
pl o t ( t1 , x1 ( : , 1 0 ) , ’ r − ’ );
h old on ;
pl o t ( t1 , p a rv a r ( 6 ) . ∗ one s ( s i z e ( t 1 ) ) , ’ b−−’);
x l a b e l ( ’ $time [ s e c ] $ ’ , ’ I n t e r p r e t e r ’ , ’ l a t e x ’ , ’ Fon tSize ’ , 1 4 ) ; y l a b e l ( ’ $\ pi 6$ ’ , ’ I n t e r p r e t e r ’ ,
’ l a t e x ’ , ’ Fon tSize ’ , 1 4 ) ;
g ri d on ;
l e g e n d ( ’ $\ pi 6$ ’ , ’ $\ p i {6 d }$ ’ , ’ I n t e r p r e t e r ’ ,

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

s u b pl o t ( 3 , 1 , 3 ) ;
pl o t ( t1 , x1 ( : , 1 1 ) , ’ r − ’ );
h old on ;
pl o t ( t1 , p a rv a r ( 7 ) . ∗ one s ( s i z e ( t 1 ) ) , ’ b−−’);
x l a b e l ( ’ $time [ s e c ] $ ’ , ’ I n t e r p r e t e r ’ , ’ l a t e x ’ , ’ Fon tSize ’ , 1 4 ) ; y l a b e l ( ’ $\ pi 7$ ’ , ’ I n t e r p r e t e r ’ ,
’ l a t e x ’ , ’ Fon tSize ’ , 1 4 ) ;
g ri d on ;
l e g e n d ( ’ $\ pi 7$ ’ , ’ $\ p i {7 d }$ ’ , ’ I n t e r p r e t e r ’ , ’ l a t e x ’ , L o c a ti o n =’ s o u t h e a s t ’ ) ;

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

q 1 d o t = s t a t e ( 3 ) ; q 2 d o t = s t a t e ( 4 ) ;

q = [ q1 ;
q2 ] ;

q d o t = [ q 1 d o t ;
q 2 d o t ] ;

c1 = c o s ( q1 ) ;
c2 = c o s ( q2 ) ;
c12 = c o s ( q1 + q2 ) ;
s 2 = s i n ( q2 ) ;

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

% Mass Matrix
M11 = I z 1 + I z 2 + m1∗( l 2 ˆ 2 / 4 ) + m2∗( l 1 ˆ2 +l 2 ˆ2/4 + l 1 ∗ l 2 ∗ c2 ) ; M12 = I z 2 + m2∗( l 2 ˆ2/4 + l 1 ∗ l 2 ∗ c2 ) ;
M22 = I z 2 + m2∗ l 2 ˆ 2 / 4;
M = [M11 M12;
M12 M22 ] ;

% C o r i o l i s Matrix
c = 0. 5 ∗m2∗ l 1 ∗ l 2 ∗ s 2 ;
C11 = −c ∗ q 2 d o t + k1 ;
C12 = −c ∗( q 1 d o t + q 2 d o t ) ; C21 = c ∗ q 1 d o t ;
C22 = k2 ;
C = [ C11 C12 ;
C21 C22 ] ;

% G r avi ty v e c t o r
G1 = 0. 5 ∗m1∗g∗ l 1 ∗ c1 + m2∗g ∗( l 1 ∗ c1 + 0. 4 ∗ l 2 ∗ c12 ) ; G2 = 0. 5 ∗m2∗g∗ l 2 ∗ c12 ;
G 0 = [ G1;
G2 ] ;

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

% C on t r ol law
z1 = q − q d ;
e2 = q d o t − q d o t d ; z2 = e2 + K1∗ z1 ;

tau = Y∗ p a rv a r − z1 − K2∗ z2 ;
q dd o t = in v (M) ∗ ( tau − C∗q − G 0 ) ;

d s t a t e = [ q d o t ; q dd o t ] ;
end

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

q 2 d o t ] ;

c1 = c o s ( q1 ) ;
c2 = c o s ( q2 ) ;
c12 = c o s ( q1 + q2 ) ;
s 2 = s i n ( q2 ) ;

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

% Mass Matrix
M11 = I z 1 + I z 2 + m1∗( l 2 ˆ 2 / 4 ) + m2∗( l 1 ˆ2 +l 2 ˆ2/4 + l 1 ∗ l 2 ∗ c2 ) ; M12 = I z 2 + m2∗( l 2 ˆ2/4 + l 1 ∗ l 2 ∗ c2 ) ;
M22 = I z 2 + m2∗ l 2 ˆ 2 / 4;
M = [M11 M12;
M12 M22 ] ;

% C o r i o l i s Matrix
c = 0. 5 ∗m2∗ l 1 ∗ l 2 ∗ s 2 ;
C11 = −c ∗ q 2 d o t + k1 ;
C12 = −c ∗( q 1 d o t + q 2 d o t ) ; C21 = c ∗ q 1 d o t ;
C22 = k2 ;
C = [ C11 C12 ;
C21 C22 ] ;

% G r avi ty v e c t o r
G1 = 0. 5 ∗m1∗g∗ l 1 ∗ c1 + m2∗g ∗( l 1 ∗ c1 + 0. 4 ∗ l 2 ∗ c12 ) ; G2 = 0. 5 ∗m2∗g∗ l 2 ∗ c12 ;
G 0 = [ G1;
G2 ] ;

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

% C on t r ol law
z1 = q − q d ;
e2 = q d o t − q d o t d ;
z2 = e2 + K1∗ z1 ;
p a r v a r d o t = −Gp∗Y’ ∗ z2 ;
tau = Y∗ p a r v a r e s t − z1 − K2∗ z2 ;
q dd o t = in v (M) ∗ ( tau − C∗q − G 0 ) ;

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

# Βιβλιογραφία

[1] Iliya V. Miroshnik Alexander L. Fradkov and Vladimir O. Nikiforov. Nonlinear and Adaptive Control of Complex Systems. Springer, 1999. isbn: 978-94-015-9261-1. doi: 10.1007/978-94-015-9261-1. (https://doi.org/10.1007/978-94-015-9261-1)
[2] A. Astolfi and L. Marconi. Analysis and Design of Nonlinear Control Systems. Springer Berlin Heidelberg New York, 2008. isbn: 978-3-540-74357-6.
[3] Charalampos Bechlioulis. Simulation of Dynamical Systems. 2021.
[4] Jay A. Farrell and Marios M. Polycarpou. Adaptive Approximation Based Control: Unifying Neural, Fuzzy and Traditional Adaptive Approximation Approaches. John Wiley Sons, Inc., 2006. isbn: 978-0-471-72788-0. doi: 10.1007/978-0-471-72788-
0. (https://doi.org/10.1007/978-0-471-72788-0)
[5] Mohammed M’Saad Alireza Karimi Ioan Doré Landau Rogelio Lozano. Adaptive Control: Algorithms, Analysis and Applications. Second Edition. Springer, 2011. isbn: 978-0-85729-664-1. doi: 10.1007/978-0-85729-664-1. (https://doi.org/10.1007/978-0-85729-664-1)
[6] Petros A. Ioannou and Jing Sun. Robust Adaptive Control. Dover Publications, 2012. isbn: 978-0486498171.
[7] Alberto Isidori. Nonlinear Control Systems. 3rd Edition. Springer, 1995. isbn: 978-1-84628-615-5. doi: 10.1007/978-1-84628-615-5. (https://doi.org/10.1007/978-1-84628-615-5)
[8] Hassan K. Khalil. Nonlinear Systems. 3rd Edition. Pearson, 2001. isbn: 978-0130673893.
[9] Craig A. Kluever. Dynamic Systems: Modeling, Simulation, and Control. John Wiley Sons, Inc., 2015. isbn: 978-1-118-28945-7. doi: 10.1007/978-1-118-28945-7. (https://doi.org/10.1007/978-1-118-28945-7)
[10] Jinkun Liu. Intelligent Control Design and MATLAB Simulation. Springer, 2018. isbn: 978-981-10-5263-7. doi: https://doi.org/10.1007/978-981-10-5263-7. (https://doi.org/https://doi.org/10.1007/978-981-10-5263-7)
[11] Norm S. Nise. Control Systems Engineering. 8th Edition. John Wiley Sons, 2019. isbn: 978-1119590132.
[12] P.Ioannou and B. Fidan. Adaptive Control Tutorial. SIAM, 2006. isbn: 978-0-89871-615-3. doi: 10.1007/978-0-89871-615-3. (https://doi.org/10.1007/978-0-89871-615-3)
[13] V.P. Singh Rajesh Kumar and Akhilesh Mathur. Intelligent Algorithms for Analysis and Control of Dynamical Systems. Springer, 2021. isbn: 978-981-15-8045-1. doi: 10.1007/978-981-15-8045-1. (https://doi.org/10.1007/978-981-15-8045-1)
[14] Jean-Jacques E. Slotine and Weiping Li. Applied Nonlinear Control. Prentice Hall, 1991. isbn: 0-13-040890-5.
[15] Spyros G. Tzafestas. Methods and Applications of Intelligent Control. Springer, 1997. isbn: 978-94-011-5498-7. doi: 10.1007/978-94-011-5498-7. (https://doi.org/10.1007/978-94-011-5498-7)
