GeoKrom/NTUA-Intelligent-Control-Systems-and-Robotic-Systems-course/Exercises/Exercise-3/Assignment 3.pdf

Εθνικό Μετσόβιο Πολυτεχνείο

Σχολή Μηχανολόγων μηχανικών

ΔΠΜΣ Συστήματα αυτοματισμού

Κατεύθυνση Β: Συστήματα Αυτομάτου Ελέγχου και Ρομποτικής

### Μεταπτυχιακό Μάθημα:

Ευφυή Συστήματα Ελέγχου και Ρομποτικής

Ονομ/νυμο - Α.Μ.:

Γεώργιος Κρομμύδας - 02121208

Τρίτη Σειρά Ασκήσεων: Σχεδίαση Προσαρμοστικών Συστημάτων

## Ελέγχου


## Αθήνα, 2023

# Πίνακας Περιεχομένων

Κατάλογος Σχημάτων | 2
Κατάλογος Πινάκων | 3
΄Ελεγχος Διφασικού Βηματικού Κινητήρα Μόνιμου Μαγνήτη | 4

Ερώτημα - 3: MRAC Σύστημα και Προσέγγιση ΄Αγνωστης Εξωτερικής Ροπής με

Αʹ Κώδικας Προσομοίωσης | 23
Βιβλιογραφία | 32

# Κατάλογος Σχημάτων

2 | Γωνία περιστροφής και γωνιακή ταχύτητα βηματικού κινητήρα με 5% αβεβαι-
3 | Σφάλματα γωνίας περιστροφής και γωνιακής ταχύτητας βηματικού κινητήρα με
5 | Γωνία περιστροφής και γωνιακή ταχύτητα βηματικού κινητήρα με 25% αβεβαι-
6 | Σφάλματα γωνίας περιστροφής και γωνιακής ταχύτητας βηματικού κινητήρα με
8 | Γωνία περιστροφής και γωνιακή ταχύτητα βηματικού κινητήρα με 50% αβεβαι-
9 | Σφάλματα γωνίας περιστροφής και γωνιακής ταχύτητας βηματικού κινητήρα με
11 | Γωνία περιστροφής και γωνιακή ταχύτητα βηματικού κινητήρα με 75% αβεβαι-
12 | Σφάλματα γωνίας περιστροφής και γωνιακής ταχύτητας βηματικού κινητήρα με
14 | Γωνία περιστροφής και γωνιακή ταχύτητα βηματικού κινητήρα με 5% αβεβαι-
| ότητα παραμέτρων και προσέγγιση συνάρτησης εξωτερικής ροπής με RBF δίκτυο 20
15 | Σφάλματα γωνίας περιστροφής και γωνιακής ταχύτητας βηματικού κινητήρα με 5% αβεβαιότητα παραμέτρων και προσέγγιση συνάρτησης εξωτερικής ροπής με
16 | Εκτίμηση Παραμέτρων Ελεγκτή με 5% αβεβαιότητα παραμέτρων και προσέγ-
17 | Εκτίμηση Βαρών Νευρωνικού Δικτύου με 5% αβεβαιότητα παραμέτρων και

# Κατάλογος Πινάκων

1 | Παραμέτροι Διφασικού Κινητήρα Μόνιμου Μαγνήτη | | 4

# ΄Ελεγχος Διφασικού Βηματικού

# Κινητήρα Μόνιμου Μαγνήτη

Μας δίνεται το μη γραμμικό μοντέλο ενός διφασικού βηματικού κινητήρα μόνιμου μαγνήτη (βλ. Σχήμα 1) που περιγράφεται από την σχέση (1). Επιπλέον, στον πίνακα 1 εμφανίζονται

οι τιμές των παραμέτρων του βηματικού κινητήρα.

ϑ˙ = ω

Jω˙ = −Kmiasin(Nϑ) + Kmibcos(Nϑ) − Bω − TL(ϑ) | (1)

όπου η TL(ϑ) είναι η εξωτερική ροπή του φορτίου στον άξονα του κινητήρα, ϑ(rad) είναι η

γωνιακή θέση του άξονα, ω(rad/sec) είναι η γωνιακή ταχύτητα του άξονα και ia(A), ib(A)

είναι τα δύο ρεύματα φάσεων του κινητήρα (είσοδοι ελέγχου).

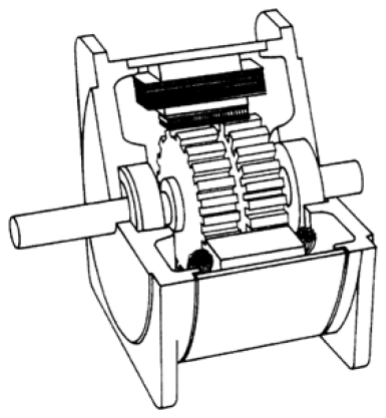
[picture p124: figure]

Σχήμα 1: Διφασικός Βηματικός Κινητήρας Μόνιμου Μαγνήτη

Παράμετρος | Τιμή
J | 4.5 × 10⁻⁵ kgr m²
Km | 0.19 Nm/A
B | 8.0 × 10⁻⁴ Nm sec/rad
N | 50

Πίνακας 1: Παραμέτροι Διφασικού Κινητήρα Μόνιμου Μαγνήτη

Θα σχεδιάσουμε προσαρμοστικούς νόμους ελέγχου ώστε το μοντέλο του κινητήρα να παρακολουθεί το μοντέλο αναφοράς της σχέσης (2)

ϑ˙
r
ω˙ r
=
0 1

−24 −10 ϑr
ωr
+
0

24
ϑc | (2)

Πριν ξεκινήσουμε τη σχεδίαση του ελεγκτή, θα κάνουμε έναν σχηματισμό στις εξισώσεις

του μοντέλου, έτσι ώστε να έρθει σε μια πιο απλή μορφή. Θέτουμε τα εξής:

### ia = −usin(Nϑ)

### ib = ucos(Nϑ)

Με την αντικατάσταση των ρευμάτων στην σχέση (1b) θα προκύψει το εξής μοντέλο:

### Jω˙ = −Km(−usin(Nϑ))sin(Nϑ) + Km(ucos(Nϑ))cos(Nϑ) − Bω − TL(ϑ)

### ⇒ Jω˙ = uKmsin²

### (Nϑ) + uKmcos²

## (Nϑ) − Bω − TL(ϑ)

### ⇒ Jω˙ = uKm(sin²

### (Nϑ) + cos²

## (Nϑ)) − Bω − TL(ϑ)

⇒ Jω˙ = −Bω + uKm − TL(ϑ) | (3)

## Ερώτημα - 1: MRAC Σύστημα

Αρχικά, θεωρούμε πως έχουμε μηδενικό φορτίο στον άξονα περιστροφής του κινητήρα. Συ-

νεπώς, το TL(ϑ) = 0. ΄Ετσι οι εξισώσεις καταστάσεις θα έχουν την εξής μορφή

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
u | (4)

Οπότε, τώρα θα σχεδιάσουμε το προσαρμοστικό σχήμα ελέγχου με την άμεση μέθοδο.

### Σχεδίαση Ελεγκτή

Ως σήμα ελέγχου θα ορίσουμε την εξής σχέση:

### u = KT

x x + Krϑc | (5)

όπου τα Kx, Kr είναι τα κέρδη του ελεγκτή που πρέπει να εκτιμήσουμε και x = [ϑ, ω]

T
| είναι

το διάνυσμα κατάστασης του συστήματος. ΄Εστω ότι γνωρίζαμε τα ιδανικά κέρδη για την

σχέση (5). Τότε:

### x˙ = Ax + Bu

### x˙ = Ax + B(KT

x

∗x + K∗
r ϑc)

### x˙ = (A + BKT

x

∗

### )x + BK∗

r ϑc

Επίσης, έχουμε και το μοντέλο αναφοράς του συστήματος:

### x˙ m = Amxm + Bmϑc

Γνωρίζοντας τα ιδεατά κέρδη προκύπτουν οι εξής σχέσεις:

### A + BKT

x

∗ = Am

BK∗
r = Bm

΄Εστω πως δεν γνωρίζαμε τα ιδεατά κέρδη για το σύστημα. Οπότε, θα έχουμε κάποιες εκτιμήσεις των κερδών Kˆ

### x, Kˆ

r. Το επόμενο βήμα είναι να βγάλουμε το δυναμικό μοντέλο σφάλματος e = x−xm. Στη συνέχεια θα βρούμε τους κατάλληλους προσαρμοστικούς νόμους

για τον υπολογισμό των κερδών. Συνεπώς, ισχύει ότι:

### e˙ = ẋ − x˙ m

### e˙ = Ax + B(Kˆ T

### x x + Kˆ

rϑc) − Amx − Bmϑc

### e˙ = Ax + B(Kˆ T

### x x + Kˆ

rϑc) − Amx − Bmϑc + Amx − Amx

### e˙ = Am(x − xm) + (A + BKˆ T

### x − Am)x + (BKˆ

r − Bm)ϑc

### e˙ = Ame + (A + BKˆ T

x − A − BKT
x

∗

### )x + (BKˆ

r − BKr∗)ϑc

### e˙ = Ame + B(Kˆ

x − K∗
x

)

### T x + B(Kˆ

r − K∗
r

)ϑc

Ορίζουμε τα σφάλματα των κερδών ως:

K˜

### x = Kˆ

x − K∗
x

K˜

### r = Kˆ

r − K∗
r

΄Ετσι, η δυναμική εξίσωση του σφάλματος θα έχει την εξής μορφή:

### e˙ = Ame + B(K˜ T

### x x + K˜

rϑc) | (6)

Το επόμενο βήμα είναι να εξετάσουμε την ευστάθεια του συστήματος και να παράγουμε

τους προσαρμοστικούς νόμους ελέγχου. ΄Εχουμε την εξής υποψήφια συνάρτηση Lyapunov

### V (e, K˜

x, K˜
r) = e

### TP e + K˜ T

x Γ

−1
x K˜
x +

1
γ3

K˜ ²
r
| (7)

όπου ο πίνακας P = P

T > 0 αποτελεί την λύση της εξίσωσης Lyapunov P Am +AT
mP = −Q,
όπου η Q = QT > 0. Επίσης, έχουμε τον πίνακα κέρδους Γx = ΓT
x > 0 και το κέρδος

προσαρμογής γ3 > 0. Εξ ορισμού διαπιστώνουμε πως η συνάρτηση V είναι θετικά ορισμένη και

ακτινικά μη φραγμένη. Το επόμενο βήμα είναι να εξετάσουμε την παράγωγο της συνάρτησης

αυτής. ΄Αρα, έχουμε ότι

### V˙ (e, K˜

x, K˜
r) = ė

### TP e + e

### TPe˙ + 2K˜ T

x Γ

−1
x

˙Kˆ
x + 2γ

−1
3 K˜
r

˙Kˆ
r

### V˙ = (Ame+B(K˜ T

### x x+K˜ rϑc))TP e+e

### TP(Ame+B(K˜ T

### x x+K˜

### rϑc))+2K˜ T

x Γ

−1
x

˙Kˆ
x+2γ

−1
3 K˜
r

˙Kˆ
r

V˙ = e
T
(A

T

### mP + P Am)e + 2e

### TP B(K˜ T

### x x + K˜

### rϑc) + 2K˜ T

x Γ

−1
x

˙Kˆ
x + 2γ

−1
3 K˜
r

˙Kˆ
r

V˙ = −e

### TQe + 2K˜ T

x

(Γ⁻¹
x

˙Kˆ

### x + xeTP B) + 2K˜

r(γ

−1
3

˙Kˆ
r + ϑce
TP B) | (8)

Η σχέση (8) αποτελέιται από έναν αρνητικό όρο και δύο θετικούς. Για να είναι αρνητικά

ημιορισμένη η παράγωγος θα πρέπει οι θετικοί όροι να είναι μηδέν. ΄Ετσι, θα έχουμε:

2K˜ T
x

(Γ⁻¹
x

˙Kˆ

### x + xeTP B) = 0

Γ

−1
x

˙Kˆ

### x + xeTP B = 0

˙Kˆ
x = −ΓxxeTP B | (9)

2K˜
r(γ

−1
3

˙Kˆ
r + ϑce

### TP B) = 0

γ

−1
3

˙Kˆ
r + ϑce

### TP B = 0

˙Kˆ
r = −γ3ϑce
TP B | (10)

Οι σχέσεις (9) και (10) αποτελούν τους προσαρμοστικούς νόμους ανανέωσης των κερδών

του σήματος ελέγχου. Με βάσει αυτές και την ιδιότητα των θετικά συμμετρικών πινάκων έχουμε ότι

### V˙ (e, K˜

x, K˜
r) = −e

## TQe ≤ −λmin(Q)||e||²

(11)

Η παράγωγος έχει ένα άνω φράγμα το οποίο σημαίνει πως η V˙ ∈ L∞, το οποίο συνε-

πάγεται πως ότι και το e ∈ L∞. Επιπλέον καθώς η παράγωγος είναι αρντικά ημιορισμένη,

διαπιστώνουμε πως ότι και η συνάρτηση V είναι φθίνουσα και μάλιστα θα το όριο της θα είναι

πεπερασμένο. Δηλαδή:

### lim

t→∞

### V (t) = V∞ < ∞

Συνεπώς, έχουμε ότι η V ∈ L∞. Επιπλέον, από την σχέση (7) θα προκύψει επίσης πως τα σφάλματα των κερδών θα είναι επίσης φραγμένα, δηλαδή K˜

x, K˜
r ∈ L∞. Επιπλέον και
οι εκτιμήσεις θα είναι φραγμένες, Kˆ

### x, Kˆ

r ∈ L∞. Εξ όρισμού έχουμε πως το σήμα εισόδου

ϑc ∈ L∞, το οποίο συνεπάγεται πως η κατάσταση xm ∈ L∞. ΄Αρα, θα καταλήξουμε στο

συμπέρασμα πως και η κατάσταση του συστήματος θα είναι και αυτή φραγμένη από τον ορισμό του σφάλματος παρακολούθησης. Οπότε το x ∈ L∞. Οπότε, θα έχουμε πως και τα ˙Kˆ
x,

˙Kˆ
r ∈
L∞ και κατ΄ επέκταση ισχύει ότι ˜˙Kx,

˜˙Kr ∈ L∞. Από την σχέση (6) θα προκύψει πως το e˙ ∈

L∞ ως άθροισμα φραγμένων σημάτων. Καθώς αποδείξαμε πως όλα τα σήματα του κλειστού

βρόχου είναι φραγμένα, τότε θα προκύψει ευστάθεια. Το επόμενο βήμα είναι να αποδείξουμε

ασυμπτωτική ευστάθεια για το σύστημα. Ολοκληρώνοντας την σχέση (11), μπορούμε να

διαπιστώσουμε το εξής:
Z ∞

0

### V˙ (e, K˜

x, K˜

### r) dt = V∞ − V (0)

Z ∞

0

−e

### TQe dt = V∞ − V (0)

−

Z ∞

0

## λmin(Q)||e||²

### dt ≥ V∞ − V (0)

Z ∞

0

## λmin(Q)||e||²

### dt ≤ V (0) − V∞

Z ∞

0

||e||²
dt ≤

V (0) − V∞

| λmin(Q)

Συνεπώς θα προκύψει πως το e ∈ L2. Καθώς το e ∈ L∞ ∩L2 και το e˙ ∈ L∞, τότε από το

Λήμμα Barbalat ´ θα προκύψει πως το e → 0, καθώς το t → ∞, θα συγκλίνει ασυμπτωτικά.

Τέλος, λόγω της παραμετρικής αβεβαιότητας, θα πρέπει να τροποποιηθούν οι προσαρ-

μοστικοί νόμοι. Θα χρησιμοποιηθεί ο τελεστής προβολής, έτσι ώστε να μην επιρεαστεί το

σύστημα από την αβεβαιότητα των παραμέτρων. Ο τελεστής αυτός θα δώσει ευσρωστία στο

σύστημα, χωρίς να επιρεάζεται η ανάλυση της ευστάθειας. ΄Ετσι, θα έχουμε φραγμένη παρα-

κολούθηση των εκτιμήσεων των κερδών του συστήματος. ΄Αρα οι προσαρμοστικοί νόμοι θα

γίνουν ως εξής:

˙Kˆ

### x = −ΓxP roj(Kˆ x, xeTP B)

˙Kˆ
x =

(

### −ΓxxeTP B + Γx

∇f(Kˆx)(∇f(Kˆx))T
||∇f(Kˆx)||²

### xeTP Bf(Kˆ

### x), if f(Kˆ x) > 0 and (−xeTP B)

### T ∇f(Kˆ

x) > 0

### −ΓxxeTP B, if not

(12)

˙Kˆ

### r = −γ3P roj(Kˆ

r, ϑce

### TP B)

˙Kˆ
r =

## −γ3ϑce

### TP B + γ3(1 − f(Kˆ

### r)), if f(Kˆ r) > 0 and (−ϑce

### TP B)f

′

(Kˆ
r) > 0

## −γ3ϑce

TP B, if not | (13)

όπου η συνάρτηση f είναι η εξής:

## f(θ) = ||θ||² − θ

2
max

### ϵθθ

2
max

(14)

και έχει παράγωγο
∇f(θ) = | 2θ ϵθθ
| 2 max

(15)

με το θmax να αποτελεί το όριο του κυρτού συνόλου προβολής και το ϵθ αποτελεί το σφάλμα

ανοχής του κυρτού συνόλου του τελεστή της προβολής.

Προσομοίωση Ελεγκτή

Το επόμενο βήμα είναι να προσομοιωθεί το παραπάνω σύστημα με είσοδο ϑc = 5 deg. Κάθε

3 sec θα αυξάνεται το σήμα εισόδου. Επομένως, κατά την προσομοίωση θα έχουμε κάποιες τα-

λαντώσεις στις εκτιμήσεις των κερδών. Επιπλέον, στο παρών παράδειγμα έχουμε αβεβαιότητα στις παραμέτρους του κινητήρα ± 5%. Κατά την προσομοίωση επιλέχθηκαν κατάλληλες τιμές

στις παραμέτρους των ρυθμών ανανέωσης, έτσι ώστε η εκτίμηση να συγκλίνει κοντά σε μια

περιοχή της ιδανικής τιμής. Για την προσομοίωση επιλέχθηκε ο πίνακας Q = I2 και με βάση

την εξίσωση Lyapunov βρέθηκε πως ο πίνακας P =

1.4583 0.02083

0.02083 0.052083
. Επίσης, ως κέρδη

προσαρμογής επιλέχθηκαν τα Γx =

2.5 | 0
0 | 0.4
και γ3 = 1.5. Με βάσει αυτές τις τιμές και

με αβεβαιότητα 5% στις παραμέτρους του κινητήρα, παράχθηκαν τα παρακάτω αποτελέσματα.

Στο σχήμα 2 παρατηρούμε τη θέση και τη γωνιακή ταχύτητα του πραγματικού μοντέλου και

του μοντέλου αναφοράς. Διαπιστώνουμε πως το πραγματικό μοντέλο ακολουθεί ασυμπτωτικά

το επιθυμητό μοντέλο, αποδεικνύοντας έτσι και τη θεωρητική ανάλυση του προσαρμοστικού

σχήματος. Επιπλέον, παρατηρώντας το σχήμα 3, διαπιστώνουμε πως τα σφάλματα συγκλίνουν

ασυμπτωτικά στο 0. Ωστόσο, παρατηρούμε στα σφάλματα κάποιες ταλαντώσεις. Οι ταλα-

ντώσεις αυτές οφείλονται αρχικά στην μεταβολή της εισόδου, που αυξάνεται ανά τρία δευτε-

ρόλεπτα. Επιπλέον, αυτές οι ταλαντώσεις οφείλονται και στην αβεβαιότητα των πραγματικών

παραμέτρων του μοντέλου. Ωστόσο, δεν επηρεάζει τη λειτουργία του συστήματος.

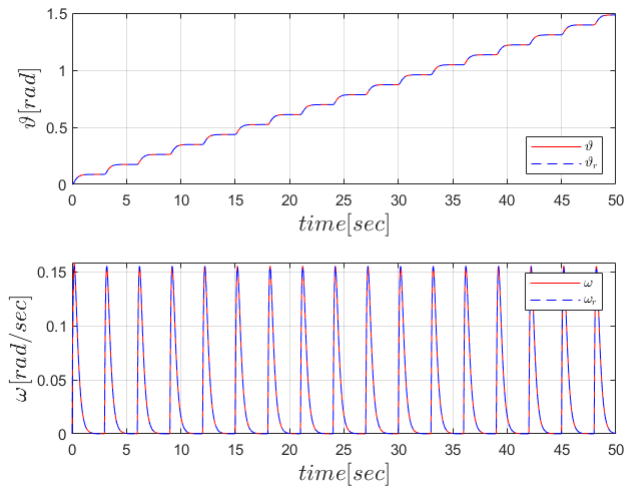
[picture p125: figure]

Σχήμα 2: Γωνία περιστροφής και γωνιακή ταχύτητα βηματικού κινητήρα με 5% αβεβαιότητα

παραμέτρων

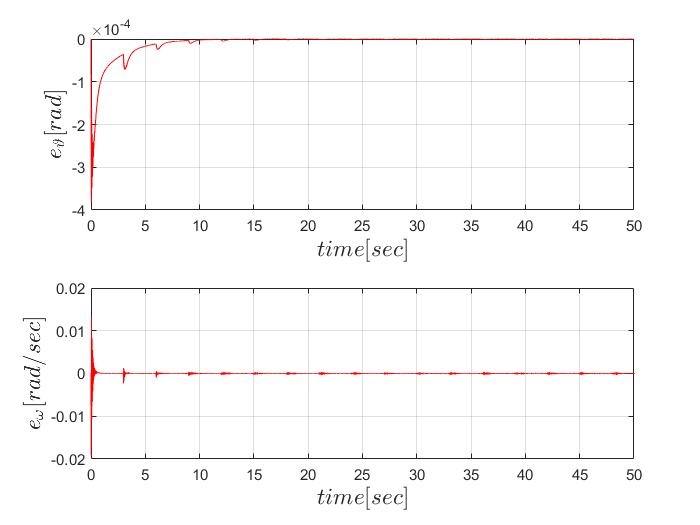
[picture p126: figure]

Σχήμα 3: Σφάλματα γωνίας περιστροφής και γωνιακής ταχύτητας βηματικού κινητήρα με 5%

αβεβαιότητα παραμέτρων

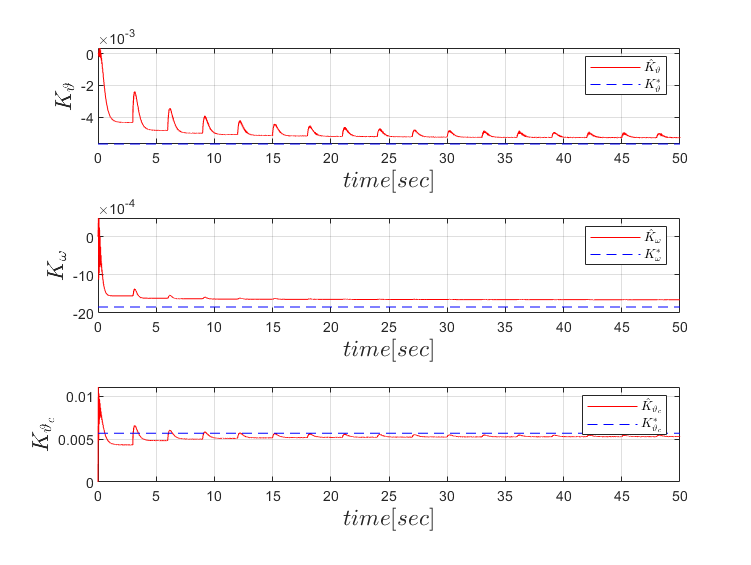
[picture p127: figure]

Σχήμα 4: Εκτίμηση Παραμέτρων Ελεγκτή με 5% αβεβαιότητα παραμέτρων

Τέλος, στο σχήμα 4 βλέπουμε την εκτίμηση των κερδών του ελεγκτή. Λόγω της παραμε-

τρικής αβεβαιότητας χρησιμοποιήθηκε ο τελεστής της προβολής, με αποτέλεσμα να έχουμε τις

εκτιμήσεις φραγμένες και μάλιστα σε μια περιοχή κοντά στα ιδεατά κέρδη. Επιπλέον, παρατη-

ρούμε πως οι εκτιμήσεις έχουν κάποιες μικρές υπερυψώσεις λόγω της αλλαγής της εισόδου.

Τέλος, παρατηρούμε πως η αβεβαιότητα προκαλεί κάποιες ταλαντώσεις στα σήματα, ωστόσο δεν προκαλεί μεγάλο θόρυβο.

## Ερώτημα - 2: MRAC Σύστημα με Παραμετρικές Αβεβαι-

## ότητες

Το σύστημα θα το προσομοιώσουμε για αβεβαιότητα παραμέτρων 25%. Παρατηρούμε πως το

πραγματικό μοντέλο παρακολουθεί ασυμπτωτικά το μοντέλο αναφοράς στο σχήμα 5. Ωστόσο,

κατά την προσομοίωση παρατηρούμε πως η παραμετρική αβεβαιότητα επηρεάζει τη σύγκλιση

του σφάλματος της ταχύτητας (βλ. σχήμα 6). Παρατηρούμε κάποιες ταλαντώσεις κατά τη

σύγκλιση που επηρεάζεται από τις παραμέτρους.

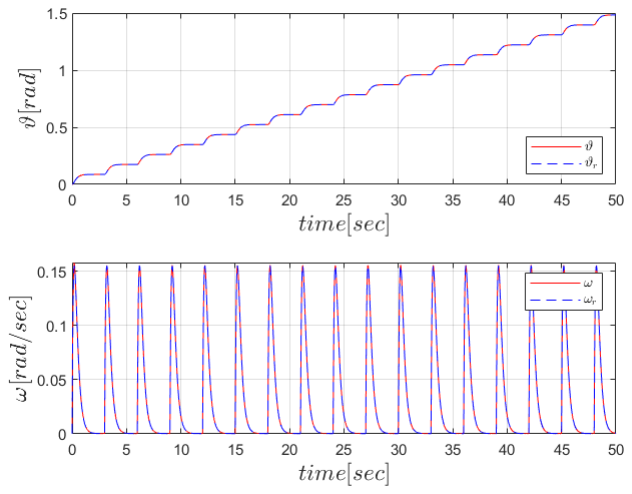
[picture p128: figure]

Σχήμα 5: Γωνία περιστροφής και γωνιακή ταχύτητα βηματικού κινητήρα με 25% αβεβαιότητα

παραμέτρων

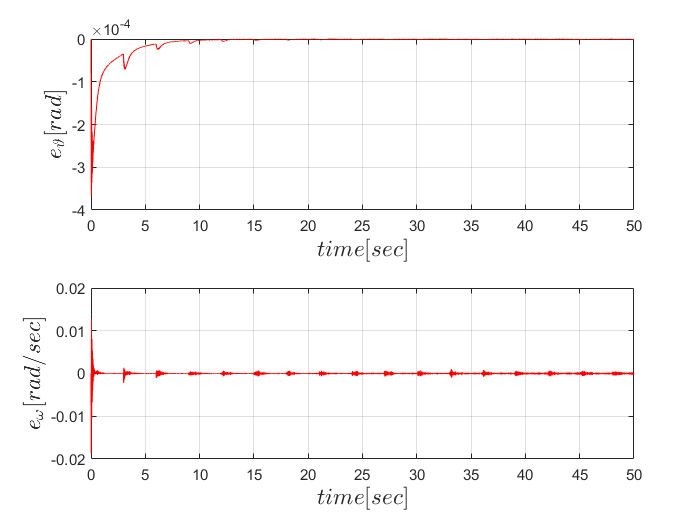
[picture p129: figure]

Σχήμα 6: Σφάλματα γωνίας περιστροφής και γωνιακής ταχύτητας βηματικού κινητήρα με 25%

αβεβαιότητα παραμέτρων

Επίσης, στο σχήμα 7 βλέπουμε πως η παραμετρική αβεβαιότητα επηρεάζει τις εκτιμήσεις

των κερδών. Σε κάθε αύξηση της εισόδου βλέπουμε να αυξάνονται οι ταλαντώσεις στις

εκτιμήσεις, προκαλώντας έτσι θόρυβο.

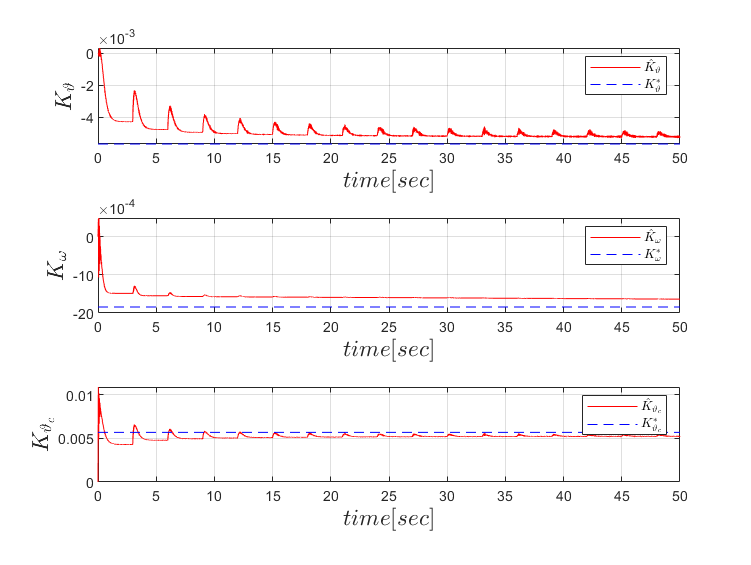
[picture p130: figure]

Σχήμα 7: Εκτίμηση Παραμέτρων Ελεγκτή με 25% αβεβαιότητα παραμέτρων

Θα αυξήσουμε την παραμετρική αβεβαιότητα στο 50% και θα προσομοιώσουμε το σύστημα.

Στο σχήμα 8 βλέπουμε την απόκριση του μοντέλου. Διαπιστώνουμε πως έχουμε ασυμπτω-

τική σύγκλισή του πραγματικού μοντέλου στο επιθυμητό. Ωστόσο, βλέποντας το σχήμα 9,

παρατηρούμε πως η παραμετρική αβεβαιότητα έχει επηρεάσει τη σύγκλιση των σφαλμάτων.

Ειδικότερα παρατηρούμε στο σφάλμα ταχύτητας πως οι ταλαντώσεις έχουνε αυξηθεί κατά την

πάροδο του χρόνου.

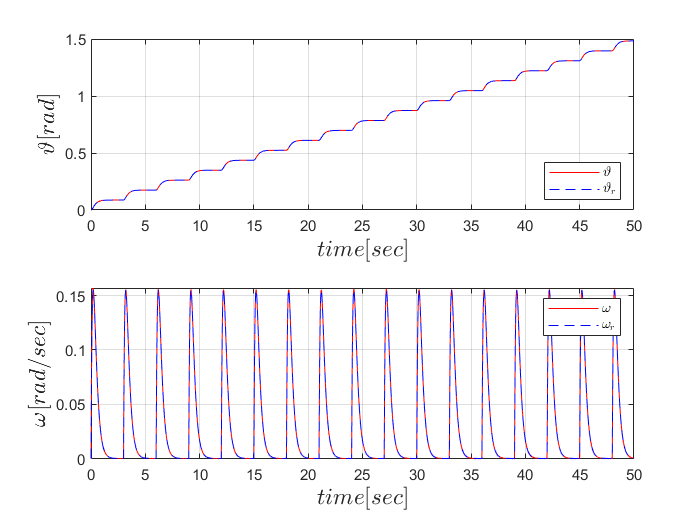
[picture p131: figure]

Σχήμα 8: Γωνία περιστροφής και γωνιακή ταχύτητα βηματικού κινητήρα με 50% αβεβαιότητα

παραμέτρων

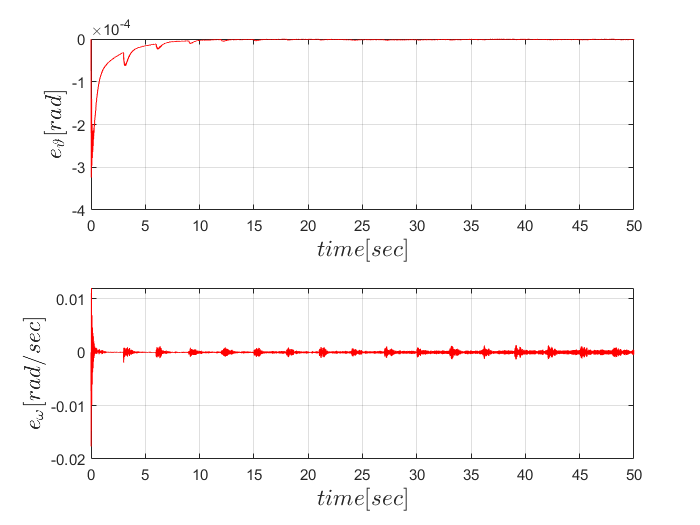
[picture p132: figure]

Σχήμα 9: Σφάλματα γωνίας περιστροφής και γωνιακής ταχύτητας βηματικού κινητήρα με 50%

αβεβαιότητα παραμέτρων

Στο σχήμα 10 παρατηρούμε τις εκτιμήσεις των κερδών του ελεγκτή. Συγκριτικά με τις

προηγούμενες προσομοιώσεις, διαπιστώνουμε πως η παραμετρική αβεβαιότητα έχει επηρεάσει

περισσότερο τις εκτιμήσεις. Τα σήματα των εκτιμήσεων έχουν παραπάνω θόρυβο, ωστόσο

παραμένουν στην περιοχή σύγκλισης των αντίστοιχων ιδεατών τιμών. ΄Αξιο σχολιασμού είναι

το γεγονός πως το κέρδος της γωνιακή ταχύτητας έχει μία κλίση που το οδηγεί πιο κοντά

στην ιδεατή τιμή. Ωστόσο, λόγο του τελεστή προβολής θα παραμείνει σε αυτή την περιοχή.

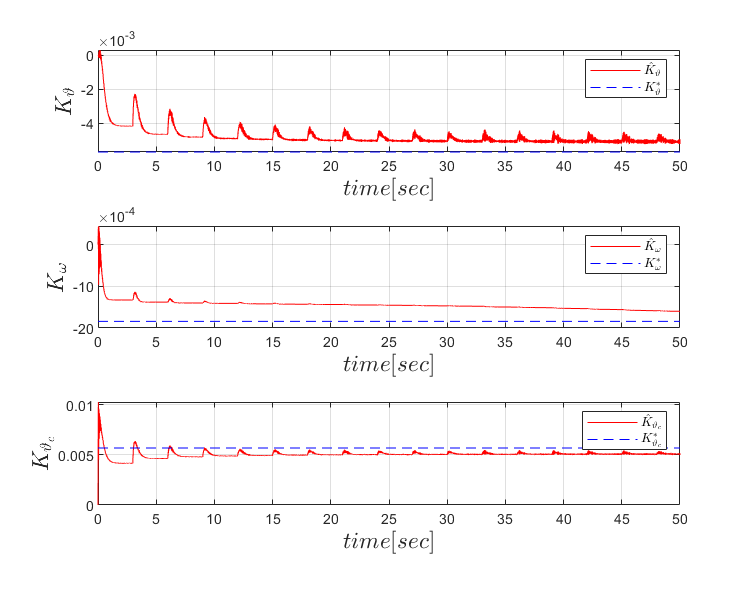
[picture p133: figure]

Σχήμα 10: Εκτίμηση Παραμέτρων Ελεγκτή με 50% αβεβαιότητα παραμέτρων

Τέλος, θα αυξήσουμε το ποσοστό της παραμετρικής αβεβαιότητας στο 75% και θα προσο-

μοιώσουμε το σύστημα. Διαπιστώνουμε από το σχήμα 11 πως έχουμε ασυμπτωτική παρακο-

λούθηση του μοντέλου αναφοράς. Ωστόσο, σύμφωνα με το σχήμα 12 παρατηρούμε πως στο

σφάλμα της ταχύτητας έχουν προκύψει περισσότερες και μεγαλύτερες ταλαντώσεις.

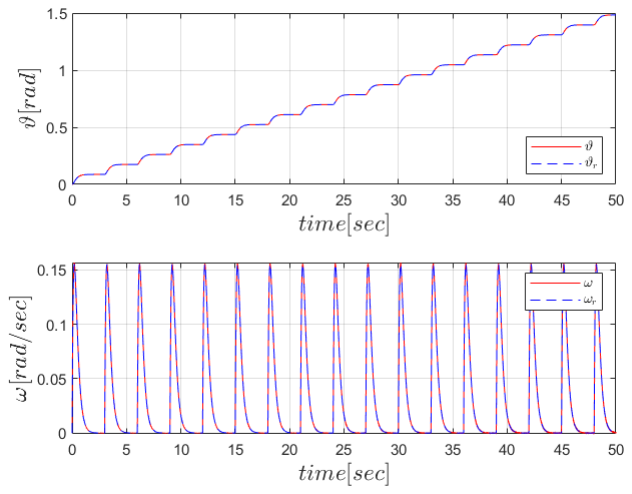
[picture p134: figure]

Σχήμα 11: Γωνία περιστροφής και γωνιακή ταχύτητα βηματικού κινητήρα με 75% αβεβαιότητα

παραμέτρων

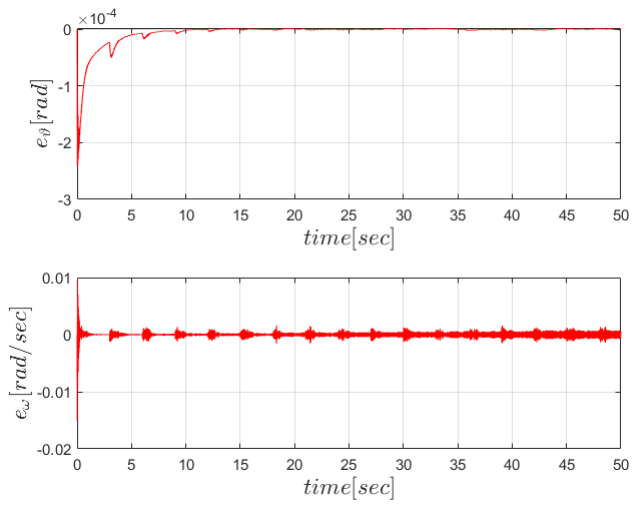
[picture p135: figure]

Σχήμα 12: Σφάλματα γωνίας περιστροφής και γωνιακής ταχύτητας βηματικού κινητήρα με 75% αβεβαιότητα παραμέτρων

Στο σχήμα 13 παρατηρούμε τις εκτιμήσεις των κερδών του ελεγκτή. Βλέπουμε πως το πο-

σοστό της αβεβαιότητας έχει επηρεάσει περισσότερο τις εκτιμήσεις. Παρατηρούμε περισσότε-

ρες ταλαντώσεις στα σήματα. Ειδικότερα, η εκτίμηση του κέρδους της γωνιακής ταχύτητας

έχει επηρεαστεί περισσότερη από τη μεταβολή των παραμέτρων καθώς φαίνεται να μειώνεται

με πιο αργό ρυθμό συγκριτικά με τα υπόλοιπα κέρδη.

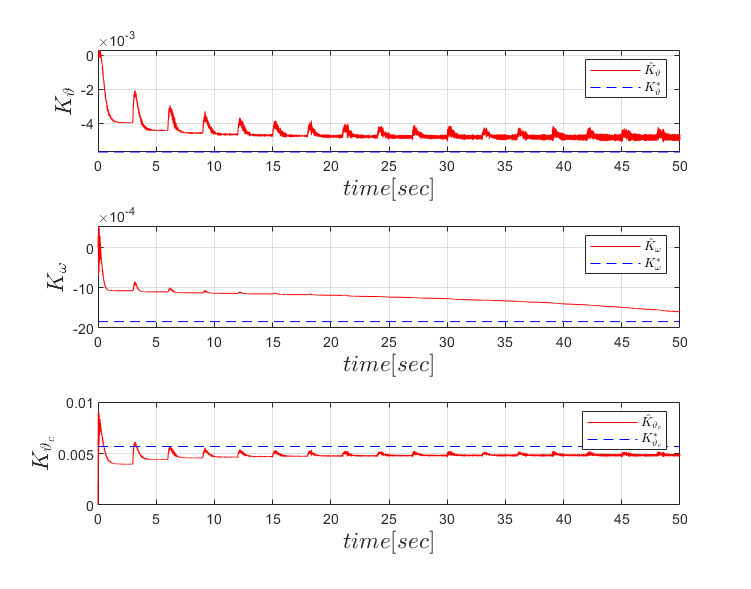
[picture p136: figure]

Σχήμα 13: Εκτίμηση Παραμέτρων Ελεγκτή με 75% αβεβαιότητα παραμέτρων

Συμπερασματικά, διαπιστώνουμε πως με την αύξηση του ποσοστού της παραμετρικής α-

βεβαιότητας ως προς τις πραγματικές παραμέτρους του κινητήρα, τα σήματα του κλειστού

βρόχου επηρεάζονται. Προκαλείται θόρυβος κατά τη λειτουργία του συστήματος, σε συνδυα-

σμό και με τη μεταβολή της είσοδο σε μικρές χρονικές περιόδους. Ωστόσο, παρατηρούμε πως

η σύγκλιση του σφάλματος παρακολούθησης παραμένει ασυμπτωτική. Αυτό οφείλεται στην

ευρωστία των προσαρμοστικών νόμων. Η τελεστής της προβολής κρατά τις εκτιμήσεις των

κερδών φραγμένες. ΄Ετσι, προκύπτει πως το πραγματικό μοντέλο θα συγκλίνει ασυμπτωτικά

στο μοντέλο αναφοράς, ανεξαρτήτως του ποσοστού της παραμετρικής αβεβαιότητας.

## Ερώτημα - 3: MRAC Σύστημα και Προσέγγιση ΄Αγνω-

## στης Εξωτερικής Ροπής με Νευρωνικό Δίκτυο

Σε αυτό το ερώτημα θα επανασχεδιάσουμε το προσαρμοστικό σχήμα με την διαφορά πως θα

κάνουμε και αναγνώριση της άγνωστης συνάρτησης του εξωτερικού φορτίου. Για την ανα-

γνώριση θα χρησιμοποιηθεί ένα νευρωνικό δίκτυο RBF με K νευρώνες. Οπότε, το μοντέλο

θα γίνει:

ϑ˙
ω˙
=
0 1
0 −
| B J

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
## TL(ϑ)

(16)

΄Ετσι, θα σχεδιάσουμε το προσαρμοστικό σχήμα με την άμεση μέθοδο και θα κάνουμε ανα-

γνώριση της άγνωστης συνάρτησης.

### Σχεδίαση Ελεγκτή

Το αρχικό βήμα είναι να ορίσουμε την εκτίμηση της άγνωστης συνάρτησης του εξωτερικού

φόρτου ροπής.
Tˆ
L(ϑ) = Θˆ T Φ(x) | (17)

Το επόμενο βήμα είναι να ορίσουμε το νευρωνικό δίκτυο που θα αποτιμήσει την παραπάνω εκτίμηση. ΄Εχουμε τον ορισμό του δικτύου ως NN(x) = WT Φ(x), όπου Φ(x) αποτελεί τους

εκπαιδευμένους RBF νευρώνες και το διάνυσμα W αποτελεί τα βάρη του στρώματος εξόδου

του νευρωνικού. Συνεπώς, τώρα θα έχουμε το εξής δυναμικό μοντέλο

x˙ = Ax + B(u − f(x)) | (18)

όπου η f(x) = ΘT Φ(x) + ϵf (x). ΄Εχουμε πως το διάνυσμα παραμέτρων Θ ∈ RK, όπου το Κ

αποτελεί το πλήθος των νευρώνων του κρυμμένο επιπέδου του δικτύου. Επιπλέον, το ϵf (x)

αποτελεί το σφάλμα προσέγγισης της άγνωστης συνάρτησης του νευρωνικού, για το οποίο

ισχύει η εξής ιδιότητα:

## ||ϵf (x)|| = ||f(x) − Θ

### T Φ(x)|| ≤ ϵ ∀x ∈ X ⊂ R²

Συνεπώς, έχουμε την εκτίμηση ˆf(x) = Θˆ T Φ(x). Επομένως, το σφάλμα της άγνωστης

συνάρτησης θα είναι

### NN(x) − f(x) = (Θˆ − Θ)T Φ(x) = Θ˜ T Φ(x) − ϵf (x)

Επιπλέον, έχουμε και το επιθημυτό μοντέλο της σχέσης (2). Οπότε, θα ορίσουμε οτ εξής

σήμα ελέγχου

### u = Kˆ T

### x x + Kˆ

rϑc + Θˆ T Φ(x) | (19)

Οπότε, ισχύει ότι:

### x˙ = Ax + B(u − f(x))

### x˙ = Ax + B(Kˆ T

### x x + Kˆ

### rϑc + Θˆ T Φ(x) − f(x))

### x˙ = Ax + B(Kˆ T

### x x + Kˆ

### rϑc + Θ˜ T Φ(x) − ϵf (x))

### x˙ = Ax + BKˆ T

### x x + B(Kˆ

### rϑc + Θ˜ T Φ(x) − ϵf (x))

### x˙ = (A + BKˆ T

x

### )x + B(Kˆ

rϑc + Θ˜ T Φ(x) − ϵf (x)) | (20)

Επίσης έχουμε
x˙ m = Amxm + Bmϑc | (21)

Για να βρούμε τα ιδεατά κέρδη πρέπει να ισχύουν οι εξής σχέσεις

### A + BKT

x

∗ = Am
BK∗
r = Bm

(22)

Συνεπώς, με αυτές τις σχέσεις θα υπολογίσουμε και τα σφάλματα εκτίμησης των κερδών.

## Οπότε

K˜

### x = Kˆ

x − K∗
x
K˜

### r = Kˆ

r − K∗
r

(23)

Οπότε, έχουμε ότι:

### A + BKˆ T

### x − Am = A + BKˆ T

x − A − BKT
x

### ∗ = B(Kˆ

### x − BK∗

x

)

### T = BK˜ T

x

### BKˆ

### r − Bm = BKˆ

### r − BK∗ r = B(Kˆ

r − K∗
r

) = BK˜
r

Τώρα θα ορίσουμε το σφάλμα παρακολούθησης ως

e = x − xm | (24)

Θα παραγωγίσουμε το σφάλμα έτσι ώστε να βρούμε την δυναμική του σφάλματος

### e˙ = ẋ − x˙ m

### e˙ = (A + BKˆ T

x

### )x + B(Kˆ

rϑc + Θ˜ T Φ(x) − ϵf (x)) − Amxm − Bmϑc ± Amx

### e˙ = Am(x − xm) + (A + BKˆ T

### x − Am)x + B(Kˆ

r − K∗
r

## ) + B(Θ˜ T Φ(x) − ϵf (x))

### e˙ = Ame + B(K˜ T

### x x + K˜

rϑc + Θ˜ T Φ(x) − ϵf (x)) | (25)

Σε αυτό το σημείο πρέπει να σημειώσουμε πως η εκτίμηση σφάλματος προσέγγισης ϵf (x)

είναι φραγμένη, εφόσον το x ∈ X. Δηλαδή πρέπει να κρατήσουμε το διάνυσμα κατάστασης

εσωτερικά του συνόλου X για να έχουμε σωστά αποτελέσματα. Το επόμενο βήμα είναι να

εξετάσουμε την ευστάθεια του συστήματος και να παράγουμε τους προσαρμοστικούς νόμους ελέγχου. ΄Εχουμε την εξής υποψήφια συνάρτηση Lyapunov

### V (e, K˜

x, K˜

### r, Θ) = ˜ e

### TP e + K˜ T

x Γ

−1
x K˜
x +

1
γ3

K˜ ²

### r + Θ˜ TΓ

−1
Θ Θ˜ | (26)

όπου ο πίνακας P = P

T > 0 αποτελεί την λύση της εξίσωσης Lyapunov P Am +AT
mP = −Q,
όπου η Q = QT > 0. Επίσης, έχουμε τον πίνακα κέρδους Γx = ΓT x > 0 και το κέρδος
προσαρμογής γ3 > 0. Επιπλέον, έχουμε και τον πίνακα κέρδους ΓΘ = ΓT
Θ > 0. Εξ ορισμού

διαπιστώνουμε πως η συνάρτηση V είναι θετικά ορισμένη και ακτινικά μη φραγμένη. Το

επόμενο βήμα είναι να εξετάσουμε την παράγωγο της συνάρτησης αυτής. ΄Αρα, έχουμε ότι

### V˙ (e, K˜

x, K˜

### r, Θ) = ˙ ˜ e TP e + e

### TPe˙ + 2K˜ T

x Γ

−1
x

˙Kˆ
x + 2γ

−1
3 K˜
r

˙Kˆ

### r + 2ΘΓ˜ −1

Θ Θˆ

### V˙ = (Ame+B(K˜ T

### x x+K˜

### rϑc)+Θ˜ T Φ(x)−ϵf (x))TP e+e

### TP(Ame+B(K˜ T

### x x+K˜

## rϑc)+Θ˜ T Φ(x)−ϵf (x))

+2K˜ T
x Γ

−1
x

˙Kˆ
x + 2γ

−1
3 K˜
r

˙Kˆ

### r + 2ΘΓ˜ −1

Θ Θˆ

V˙ = e
T
(A

T

### mP + P Am)e − 2e

### TP Bϵf (x) + 2e

### TP B(K˜ T

### x x + K˜

### rϑc + Θ˜ T Φ(x))

+2K˜ T
x Γ

−1
x

˙Kˆ
x + 2γ

−1
3 K˜
r

˙Kˆ

### r + 2ΘΓ˜ −1

Θ Θˆ

V˙ = −e

### TQe − 2e

### TP Bϵf (x) + 2K˜ T

x

(Γ⁻¹
x

˙Kˆ

### x + xeTP B)

+2K˜
r(γ

−1
3

˙Kˆ
r + ϑce

### TP B) + 2Θ˜ T

(Γ⁻¹

### Θ Θ + Φ( ˆ x)e TP B)

(27)

Η σχέση (27) αποτελέιται από έναν αρνητικό όρο και δύο θετικούς. Για να είναι αρνητικά

ημιορισμένη η παράγωγος θα πρέπει οι θετικοί όροι να είναι μηδέν. ΄Ετσι, θα έχουμε:

2K˜ T
x

(Γ⁻¹
x

˙Kˆ

### x + xeTP B) = 0

Γ

−1
x

˙Kˆ

### x + xeTP B = 0

˙Kˆ
x = −ΓxxeTP B | (28)

2K˜
r(γ

−1
3

˙Kˆ
r + ϑce

### TP B) = 0

γ

−1
3

˙Kˆ
r + ϑce

### TP B = 0

˙Kˆ
r = −γ3ϑce
TP B | (29)

2Θ˜ T

(Γ⁻¹
Θ

### ˙Θ + Φ( ˆ x)e TP B) = 0

Γ

−1
Θ

### ˙Θ + Φ( ˆ x)e TP B = 0

˙Θ =ˆ | −ΓΘΦ(x)e
TP B | (30)

Οι σχέσεις (28), (29) και (30) αποτελούν τους προσαρμοστικούς νόμους ανανέωσης των

κερδών του σήματος ελέγχου. Με βάσει αυτές και την ιδιότητα των θετικά συμμετρικών

πινάκων έχουμε ότι

### V˙ (e, K˜

x, K˜

### r, Θ) = ˜ −e TQe − 2e

## TP Bϵf (x) ≤ −λmin(Q)||e||² + 2||e|| ||P B||ϵ (31)

Παρατηρούε πως η παράγωγος είναι φραγμένη από έναν αρνητικό όρο και από έναν όρο ο οποίος εξαρτάται από την νόρμα του σφάλματος. Για να έχουμε την V <˙ 0 θα πρέπει να

ισχύει:

### V <˙ 0 ⇒ −λmin(Q)||e||² + 2||e|| ||P B||ϵ < 0

||e|| >

## ||P B||ϵ

λmin(Q)

(32)

Συνεπώς η παράγωγος θα έχει αρνητικες τιμές έξω από το υποσύνολο

E =

## e | ||e|| ≤ ||P B||ϵ

λmin(Q)

Πρέπει να διατηρήσουμε το σφάλμα μεγαλύτερο από την οριακή τιμή του συνόλου E. ΄Ετσι,

θα έχουμε ότι η παράγωγος έχει αρνητικό πρόσημο και πως όλα τα σήματα του κλειστού

βρόχου θα είναι φραγμένα. Για να αποτρέψουμε την είσοδο του σφάλματος σε αυτή την

περιοχή, θα χρησιμοποιήσουμε τον κανόνα της προβολής στους προσαρμοστικούς νόμους.

΄Ετσι, αυτοί θα γίνουν

˙Kˆ

### x = −ΓxP roj(Kˆ x, xeTP B)

˙Kˆ
x =

(

### −ΓxxeTP B + Γx

∇f(Kˆx)(∇f(Kˆx))T
||∇f(Kˆx)||²

### xeTP Bf(Kˆ

### x), if f(Kˆ x) > 0 and (−xeTP B)

### T ∇f(Kˆ

x) > 0

### −ΓxxeTP B, if not

(33)

˙Kˆ

### r = −γ3P roj(Kˆ

r, ϑce

### TP B)

˙Kˆ
r =

## −γ3ϑce

### TP B + γ3(1 − f(Kˆ

### r)), if f(Kˆ r) > 0 and (−ϑce

### TP B)f

′

(Kˆ
r) > 0

## −γ3ϑce

TP B, if not | (34)
˙Θ =ˆ | −ΓΘP roj(Θˆ , Φ(x)e

### TP B)

˙Θ =ˆ

(

### −ΓΘΦ(x)e

### TP B + ΓΘ

∇f(Θ)( ˆ ∇f(Θ)) ˆ T
||∇f(Θ) ˆ ||² Φ(x)e

### TP Bf(Θ) ˆ , if f(Θ) ˆ > 0 and (−Φ(x)e TP B)

### T ∇f(Θ) ˆ > 0

### −ΓΘΦ(x)e

### TP B, if not

(35)

όπου η συνάρτηση f είναι η εξής:

## f(θ) = ||θ||² − θ

2
max

### ϵθθ

2
max

(36)

και έχει παράγωγο

## ∇f(θ) = 2θ

### ϵθθ

2
max

(37)

με το θmax να εποτελεί το όριο του κυρτού συνόλου προβολής και το ϵθ αποτελεί το σφάλμα

ανοχής του κυρτού συνόλου του τελεστή της προβολής.

Καθώς με τους προσαρμοστικούς νόμους έχουμε καθορίσει το κυρτό σύνολο στο οποίο

λειτουργεί το σύστημα, τότε εξασφαλίζουμε πως σε κάθε βήμα του αλγορίθμου θα έχουμε αρνητική παράγωγο.Η παράγωγος έχει ένα άνω φράγμα το οποίο σημαίνει πως η V˙ ∈ L∞,

το οποίο συνεπάγεται πως ότι και το e ∈ L∞. Επιπλέον καθώς η παράγωγος είναι αρντικά

ημιορισμένη, διαπιστώνουμε πως ότι και η συνάρτηση V είναι φθίνουσα και μάλιστα θα το όριο

της θα είναι πεπερασμένο. Δηλαδή:

### lim

t→∞

### V (t) = V∞ < ∞

Συνεπώς, έχουμε ότι η V ∈ L∞. Επιπλέον, από την σχέση (7) θα προκύψει επίσης πως τα σφάλματα των κερδών θα είναι επίσης φραγμένα, δηλαδή K˜

x, K˜

r, Θ˜ ∈ L∞. Επι-

πλέον και οι εκτιμήσεις θα είναι φραγμένες, Kˆ

### x, Kˆ

r ∈ L∞. Εξ όρισμού έχουμε πως το

σήμα εισόδου ϑc ∈ L∞, το οποίο συνεπάγεται πως η κατάσταση xm ∈ L∞. ΄Αρα, θα κα-

ταλήξουμε στο συμπέρασμα πως και η κατάσταση του συστήματος θα είναι και αυτή φραγ-

μένη από τον ορισμό του σφάλματος παρακολούθησης. | Οπότε το x ∈ L∞. | Οπότε, θα
έχουμε πως και τα ˙Kˆ
x,

˙Kˆ
r,

˙Θˆ ∈ L∞ και κατ΄ επέκταση ισχύει ότι ˜˙Kx,
˜˙Kr, ,

## ˜˙Θ ∈ L∞. Α-

πό την σχέση (6) θα προκύψει πως το e˙ ∈ L∞ ως άθροισμα φραγμένων σημάτων. Καθώς

αποδείξαμε πως όλα τα σήματα του κλειστού βρόχου είναι φραγμένα, τότε θα προκύψει ευ-

στάθεια. Το επόμενο βήμα είναι να αποδείξουμε ασυμπτωτική ευστάθεια για το σύστημα.

Επειδή έχουμε αποδείξει ένα κάτω φράγμα για το σφάλμα, θα χρησιμοποιήσουμε την ιδιότητα

### UUB (Uniform Ultimate Boundedness). Σύμφωνα με το φράγμα αυτό, αποδείξαμε πως η

τροχιά του e θα κινείται εντός του δακτυλίου με κάτω όριο το C =

| ||P B||ϵ λmin(Q)
. Συνεπώς έχουμε

### V˙ (e, K˜

x, K˜

### r, Θ) ˜ < 0, ∀ C < ||e||

Συνεπώς, αφού το ee = 0 είναι UUB τότε θα έχουμε ασυμπτωτική σύγκλιση του σφάλ-

ματος στο μηδέν. Επιπλέον, η παραπάνω ιδιότητα ισχύεικαθώς το σφάλμα είναι φραγμένο
(e ∈ L∞).

Προσομοίωση Ελεγκτή

Το επόμενο βήμα είναι να προσομοιωθεί το παραπάνω σύστημα με είσοδο ϑc = 5 deg. Κάθε

3 sec θα αυξάνεται το σήμα εισόδου. Επομένως, κατά την προσομοίωση θα έχουμε κάποιες

ταλαντώσεις στις εκτιμήσεις των κερδών. Επιπλέον, στο παρών παράδειγμα έχουμε αβεβαιότητα στις παραμέτρους του κινητήρα ± 5%. Κατά την προσομοίωση επιλέχθηκαν κατάλληλες

τιμές στις παραμέτρους των ρυθμών ανάνεωσης, έτσι ώστε η εκτίμηση να συγκλίνει κοντά

σε μια περιοχή της ιδανικής τιμής. Για την προσομοίωση επιλέχθηκε ο πίνακας Q = I2

και με βάση την εξίσωση Lyapunov βρέθηκε πως ο πίνακας P =

1.4583 0.02083

0.02083 0.052083
. Ε-

πίσης, ως κέρδη προσαρμογής επιλέχθηκαν τα Γx =

0.6 0
0 | 3
και γ3 = 0.5. | Επιπλέον,

έχουμε και τον πίνακα προσαρμογής των βαρών του εξωτερικού στρώματος του νευρωνικο-

## ύ δικτύου ΓΘ =

1.5 | 0 | 0 | 0 | 0
0 | 1.5 | 0 | 0 | 0
0 | 0 | 1.5 | 0 | 0
0 | 0 | 0 | 1.5 | 0
0 | 0 | 0 | 0 | 1.5

. | Επιπρόσθετα, η αρχιτεκτονική του δικτύου
περιέχει 1 κρυμμένο επίπεδο με 5 νευρώνες. | Το νευρωνικό έχει εκπαιδευτεί οφφλινε με
το σύνολο ϑ ∈ [0, π] με βήμα dϑ = 10⁻⁵ και με συνάρτηση εξωτερικού φόρτου ροπής

### TL(ϑ) = 10⁻³ cos²

(2ϑ)sin(3ϑ) Nm. Με βάσει αυτές τις τιμές και με αβεβαίοτητα 5% στις πα-

ραμέτρους του κινητήρα, παράχθηκαν τα παρακάτω αποτελέσματα. Στο σχήμα 14 παρατηρούμε

την απόκριση του πραγματικού μοντέλου μαζί με την προσέγγιση της συνάρτησης της ροπής.

Βλέπουμε πως έχουμε ασυμπτωτική σύγκλιση του πραγματικού μοντέλου στο επιθυμητό, με

αυτό μάλιστα να φαίνεται και στο σχήμα 15. Ωστόσο λόγω της προσέγγισης που γίνεται μεσω

του δικτύου, βλέπουμε πως υπάρχουν περισσότερες ταλαντώσεις που προσθέτονται σε αυτές

που δημιουργούνται από την παραμετρική αβεβαιότητα.

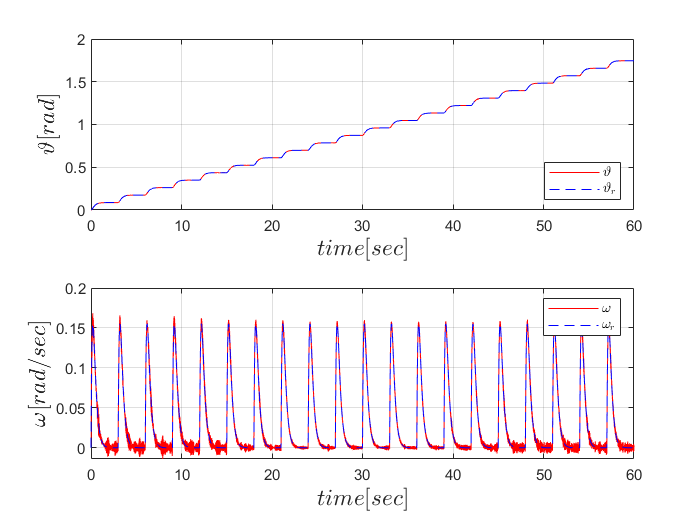
[picture p137: figure]

Σχήμα 14: Γωνία περιστροφής και γωνιακή ταχύτητα βηματικού κινητήρα με 5% αβεβαιότητα

παραμέτρων και προσέγγιση συνάρτησης εξωτερικής ροπής με RBF δίκτυο

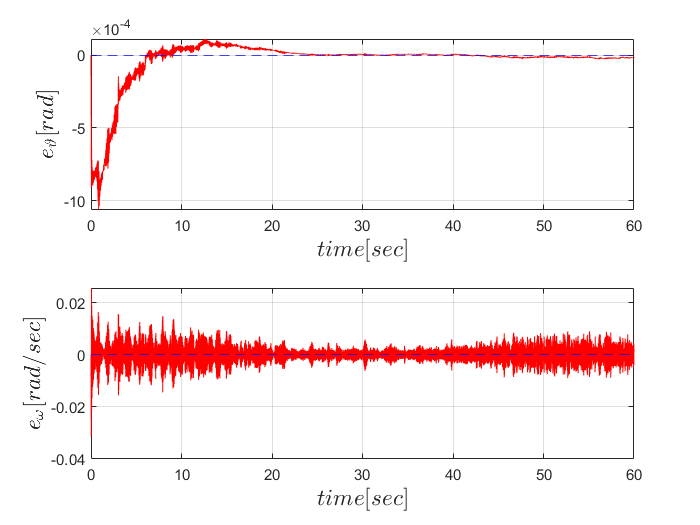
[picture p138: figure]

Σχήμα 15: Σφάλματα γωνίας περιστροφής και γωνιακής ταχύτητας βηματικού κινητήρα με 5%

αβεβαιότητα παραμέτρων και προσέγγιση συνάρτησης εξωτερικής ροπής με RBF δίκτυο

Εν συνεχεία, στα σχήματα 16 και 17 παρατηρούμε την προσαρμογή των εκτιμίσεων των

κερδών και των βαρών του επιπέδου εξόδου του νευρωνικού. Διαπιστώνουμε πως οι εκτιμήσεις

συγκλίνουν σε μια περιοχή κοντά στις ιδεατές τιμές, με αποτέλεσμα να έχουμε την ασυμπτωτική σύγλιση που χρειαζόμαστε εσωτερικά του συνόλου X ⊂ R²
. ΄Ετσι, γνωρίζουμε πως το

διάνυσμα κατάστασης θα κινείται εντός του επιθμητού συνόλου για να κρατάει αρνητική την

παράγωγο της υποψήφιας συνάρτησης Lyapunov.

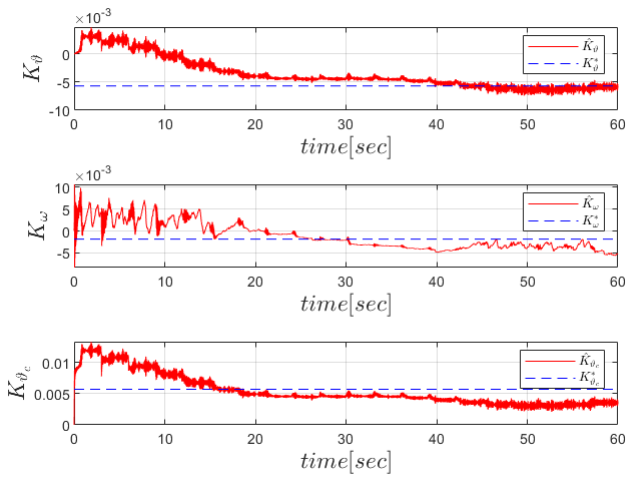
[picture p139: figure]

Σχήμα 16: Εκτίμηση Παραμέτρων Ελεγκτή με 5% αβεβαιότητα παραμέτρων και προσέγγιση συνάρτησης εξωτερικής ροπής με RBF δίκτυο

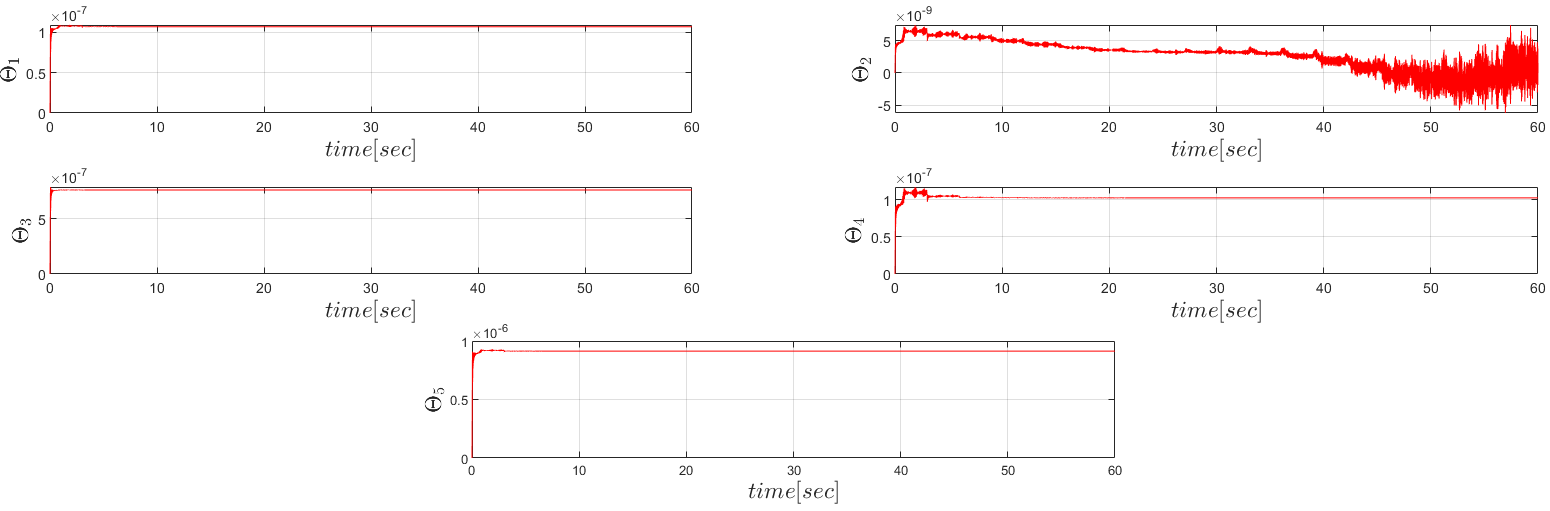
[picture p140: figure]

Σχήμα 17: Εκτίμηση Βαρών Νευρωνικού Δικτύου με 5% αβεβαιότητα παραμέτρων και προ-

σέγγιση συνάρτησης εξωτερικής ροπής με RBF δίκτυο

Τέλος, παρόλλο που οι αποκρίσεις περιέχουν τόσες πολλές ταλαντώσεις, τα σήματα των

εκτιμίσεων μας εγγυάντε πως η παράγωγος θα παραμένει αρνητική και θα βρισκόμαστε ε-

κτός του συνόλου E. ΄Ετσι, θα έχουμε την επιθυμητή ασυμπτωτική ευστάθεια στο σύστημα κλειστού βρόχου. Επιπλέον, αξίζει να σχολιαστεί η προσέγγιση της συνάρτησης TL(ϑ). Πα-

ρατηρούμε πως το νευρωνικό δικτύο προσεγγίζει καλά την άγνωστη συνάρτηση, παρόλλο που

προστίθεται αβεβαιότητα λόγω της εκτίμησης του δικτύου.

# Παράρτημα Αʹ

# Κώδικας Προσομοίωσης

Σε αυτό το παράρτημα παρουσιάζεται ο κώδικας προσομοιώσης της παρούσας άσκησης.

### %% S teppe r Motor Adaptive C on t r ol

% | Assignment 3
% | Name: George Krommydas
% | A.M. : 02121208

c l e a r ;
c l c ;

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

### %% Parameter s e t t i n g

B = 8∗1 e −4; | % Nm s e c / rad
J = 4. 5∗1 e −5; | % kgr mˆ2
Km = 0 . 1 9 ; | % N m/A
N = 5 0;
Am = [ 0 1 ;
−24 −10];
Bm = [ 0 ;
2 4 ] ;
Q = eye ( 2 ) ;
P = l y ap (Am’ ,Q) ;

t s t a r t = 0 ;
tend = 5 0;
t sp an = [ t s t a r t , tend ] ; n = 7 ;

x0 = z e r o s ( n , 1 ) ;
opt = o d e s e t ( ’ RelTol ’ , 1e −8, ’ AbsTol ’ , 1e −6); count = 1 ;
K = 5 ;
r = 0. 0 8 7 2 6 6;

t h e t a = 0: 1 e −5: pi ;
T L = 1e −3∗(( c o s ( 2∗ t h e t a ) ) . ˆ 2 ) . ∗ s i n ( 3∗ t h e t a ) ;

### %% Neural Network T r ai ni n g

di s p ( ” T r ai ni n g . . . . ” ) ;

### di s p ( ” ” )

ne t = f i t r n e t ( the t a ’ , T L ’ , ” L a y e r Si z e s ” ,K, ” A c ti v a ti o n s ” , ” si gm oid ” ) ; di s p ( ” T r ai ni n g s t oped . . . . ” ) ;

### di s p ( ” ” )

### %% Ode sim ul a ti o n

[ t , x ] = ode45 (@MRACStepper , tspan , x0 , opt ) ;

### % I d e a l Gains

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

### % Pl o t s

f i g u r e ( 1 ) ;
c l f ;

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

s u b pl o t ( 2 , 1 , 2 ) ;
pl o t ( t , x ( : , 2 ) , ’ r − ’ );
h old on ;
pl o t ( t , x ( : , 4 ) , ’ b−−’);
x l a b e l ( ’ $time [ s e c ] $ ’ , ’ I n t e r p r e t e r ’ , ’ l a t e x ’ , ’ Fon tSize ’ , 1 4 ) ;
y l a b e l ( ’ $\omega [ rad / s e c ] $ ’ , ’ I n t e r p r e t e r ’ , ’ l a t e x ’ , ’ Fon tSize ’ , 1 4 ) ; g ri d on ;
l e g e n d ( ’ $\omega$ ’ ,
’ $\ omega r$ ’ , ’ I n t e r p r e t e r ’ , ’ l a t e x ’ , L o c a ti o n =’ n o r t h e a s t ’ ) ;

f i g u r e ( 2 ) ;

c l f ;

s u b pl o t ( 2 , 1 , 1 ) ;
pl o t ( t , x (: , 1 ) −x ( : , 3 ) , ’ r − ’ );
h old on ;
y l i n e ( 0 , ’ b−−’);
x l a b e l ( ’ $time [ s e c ] $ ’ , ’ I n t e r p r e t e r ’ , ’ l a t e x ’ , ’ Fon tSize ’ , 1 4 ) ;
y l a b e l ( ’ $ e {\ v a r t h e t a } [ rad ] $ ’ , ’ I n t e r p r e t e r ’ , ’ l a t e x ’ , ’ Fon tSize ’ , 1 4 ) ; g ri d on ;
s u b pl o t ( 2 , 1 , 2 ) ;
pl o t ( t , x (: , 2 ) −x ( : , 4 ) , ’ r − ’ );
h old on ;
y l i n e ( 0 , ’ b−−’);
x l a b e l ( ’ $time [ s e c ] $ ’ , ’ I n t e r p r e t e r ’ , ’ l a t e x ’ , ’ Fon tSize ’ , 1 4 ) ;
y l a b e l ( ’ $ e {\omega} [ rad / s e c ] $ ’ , ’ I n t e r p r e t e r ’ , ’ l a t e x ’ , ’ Fon tSize ’ , 1 4 ) ; g ri d on ;

f i g u r e ( 3 ) ;
c l f ;

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

s u b pl o t ( 3 , 1 , 2 ) ;
pl o t ( t , x ( : , 6 ) , ’ r − ’ );
h old on ;
pl o t ( t , K omega star , ’ b−−’);
x l a b e l ( ’ $time [ s e c ] $ ’ , ’ I n t e r p r e t e r ’ , ’ l a t e x ’ , ’ Fon tSize ’ , 1 4 ) ; y l a b e l ( ’ $K {\omega}$ ’ , ’ I n t e r p r e t e r ’ , ’ l a t e x ’ , ’ Fon tSize ’ , 1 4 ) ; g ri d on ;
l e g e n d ( ’ $\ hat {K} {\omega}$ ’ , ’ $K {\omega}ˆ∗$ ’ ,
’ I n t e r p r e t e r ’ , ’ l a t e x ’ , L o c a ti o n =’ n o r t h e a s t ’ ) ;

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

### %% Ode Sim ul a ti o n 2

x1 = z e r o s ( n+K, 1 ) ;

[ t1 , x1 ] = ode45 ( @MRACStepperNeuralNetwork , tspan , x1 , opt ) ;

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

### % Pl o t s

f i g u r e ( 4 ) ;
c l f ;

s u b pl o t ( 2 , 1 , 1 ) ;
pl o t ( t1 , x1 ( : , 1 ) , ’ r − ’ );
h old on ;
pl o t ( t1 , x1 ( : , 3 ) , ’ b−−’);
x l a b e l ( ’ $time [ s e c ] $ ’ , ’ I n t e r p r e t e r ’ , ’ l a t e x ’ , ’ Fon tSize ’ , 1 4 ) ;
y l a b e l ( ’ $\ v a r t h e t a [ rad ] $ ’ , ’ I n t e r p r e t e r ’ , ’ l a t e x ’ , ’ Fon tSize ’ , 1 4 ) ; g ri d on ;
l e g e n d ( ’ $\ v a r the t a$ ’ , ’ $\ v a r t h e t a r $ ’ , ’ I n t e r p r e t e r ’ ,
’ l a t e x ’ , L o c a ti o n =’ s o u t h e a s t ’ ) ;

s u b pl o t ( 2 , 1 , 2 ) ;
pl o t ( t1 , x1 ( : , 2 ) , ’ r − ’ );
h old on ;
pl o t ( t1 , x1 ( : , 4 ) , ’ b−−’);
x l a b e l ( ’ $time [ s e c ] $ ’ , ’ I n t e r p r e t e r ’ , ’ l a t e x ’ , ’ Fon tSize ’ , 1 4 ) ;
y l a b e l ( ’ $\omega [ rad / s e c ] $ ’ , ’ I n t e r p r e t e r ’ , ’ l a t e x ’ , ’ Fon tSize ’ , 1 4 ) ; g ri d on ;
l e g e n d ( ’ $\omega$ ’ , ’ $\ omega r$ ’ , ’ I n t e r p r e t e r ’ ,
’ l a t e x ’ , L o c a ti o n =’ n o r t h e a s t ’ ) ;

f i g u r e ( 5 ) ;
c l f ;

s u b pl o t ( 2 , 1 , 1 ) ;
pl o t ( t1 , x1 ( : , 1 ) − x1 ( : , 3 ) , ’ r − ’ );
h old on ;
y l i n e ( 0 , ’ b−−’);
x l a b e l ( ’ $time [ s e c ] $ ’ , ’ I n t e r p r e t e r ’ , ’ l a t e x ’ , ’ Fon tSize ’ , 1 4 ) ;
y l a b e l ( ’ $ e {\ v a r t h e t a } [ rad ] $ ’ , ’ I n t e r p r e t e r ’ , ’ l a t e x ’ , ’ Fon tSize ’ , 1 4 ) ; g ri d on ;
s u b pl o t ( 2 , 1 , 2 ) ;
pl o t ( t1 , x1 ( : , 2 ) − x1 ( : , 4 ) , ’ r − ’ );
h old on ;
y l i n e ( 0 , ’ b−−’);
x l a b e l ( ’ $time [ s e c ] $ ’ , ’ I n t e r p r e t e r ’ , ’ l a t e x ’ , ’ Fon tSize ’ , 1 4 ) ;
y l a b e l ( ’ $ e {\omega} [ rad / s e c ] $ ’ , ’ I n t e r p r e t e r ’ , ’ l a t e x ’ , ’ Fon tSize ’ , 1 4 ) ; g ri d on ;

f i g u r e ( 6 ) ;
c l f ;

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

s u b pl o t ( 3 , 1 , 2 ) ;
pl o t ( t1 , x1 ( : , 6 ) , ’ r − ’ );
h old on ;
pl o t ( t1 , K omega star , ’ b−−’);
x l a b e l ( ’ $time [ s e c ] $ ’ , ’ I n t e r p r e t e r ’ , ’ l a t e x ’ , ’ Fon tSize ’ , 1 4 ) ; y l a b e l ( ’ $K {\omega}$ ’ , ’ I n t e r p r e t e r ’ , ’ l a t e x ’ , ’ Fon tSize ’ , 1 4 ) ; g ri d on ;
l e g e n d ( ’ $\ hat {K} {\omega}$ ’ , ’ $K {\omega}ˆ∗$ ’ , ’ I n t e r p r e t e r ’ , ’ l a t e x ’ , L o c a ti o n =’ n o r t h e a s t ’ ) ;

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

f i g u r e ( 7 ) ;
c l f ;
s u b pl o t ( 5 , 2 , 1 ) ;
pl o t ( t1 , x1 ( : , 8 ) , ’ r − ’ );
x l a b e l ( ’ $time [ s e c ] $ ’ , ’ I n t e r p r e t e r ’ , ’ l a t e x ’ , ’ Fon tSize ’ , 1 4 ) ; y l a b e l ( ’ $\Theta 1$ ’ , ’ I n t e r p r e t e r ’ , ’ l a t e x ’ , ’ Fon tSize ’ , 1 4 ) ;
g ri d on ;

s u b pl o t ( 5 , 2 , 2 ) ;
pl o t ( t1 , x1 ( : , 9 ) , ’ r − ’ );
x l a b e l ( ’ $time [ s e c ] $ ’ , ’ I n t e r p r e t e r ’ , ’ l a t e x ’ , ’ Fon tSize ’ , 1 4 ) ; y l a b e l ( ’ $\Theta 2$ ’ , ’ I n t e r p r e t e r ’ , ’ l a t e x ’ , ’ Fon tSize ’ , 1 4 ) ;
g ri d on ;

s u b pl o t ( 5 , 2 , 3 ) ;
pl o t ( t1 , x1 ( : , 1 0 ) , ’ r − ’ );
x l a b e l ( ’ $time [ s e c ] $ ’ , ’ I n t e r p r e t e r ’ , ’ l a t e x ’ , ’ Fon tSize ’ , 1 4 ) ;

y l a b e l ( ’ $\Theta 3$ ’ , ’ I n t e r p r e t e r ’ , ’ l a t e x ’ , ’ Fon tSize ’ , 1 4 ) ; g ri d on ;

s u b pl o t ( 5 , 2 , 4 ) ;
pl o t ( t1 , x1 ( : , 1 1 ) , ’ r − ’ );
x l a b e l ( ’ $time [ s e c ] $ ’ , ’ I n t e r p r e t e r ’ , ’ l a t e x ’ , ’ Fon tSize ’ , 1 4 ) ; y l a b e l ( ’ $\Theta 4$ ’ , ’ I n t e r p r e t e r ’ , ’ l a t e x ’ , ’ Fon tSize ’ , 1 4 ) ;
g ri d on ;

s u b pl o t ( 5 , 2 , 5 ) ;
pl o t ( t1 , x1 ( : , 1 2 ) , ’ r − ’ );
x l a b e l ( ’ $time [ s e c ] $ ’ , ’ I n t e r p r e t e r ’ , ’ l a t e x ’ , ’ Fon tSize ’ , 1 4 ) ; y l a b e l ( ’ $\Theta 5$ ’ , ’ I n t e r p r e t e r ’ , ’ l a t e x ’ , ’ Fon tSize ’ , 1 4 ) ;
g ri d on ;

### f u n c ti o n d s t a t e = MRACStepper ( t , s t a t e )

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

p e ri o d = t ( : , 1 ) ;
di s p ( ” Time Loop t = ” + p e ri o d + ” s e c ” ) ; r 0 = 0. 0 8 7 2 6 6;

### % Parameter U n c e r t a i n t i e s

pe r = 0 . 7 5 ;
B un = (B − B∗ pe r ) + ( (B + B∗ pe r ) − (B − B∗ pe r ) ) ∗ rand ( 1 ) ;
J un = ( J − J∗ pe r ) + ( ( J + J∗ pe r ) − ( J − J∗ pe r ) ) ∗ rand ( 1 ) ;
Km un = (Km − Km∗ pe r ) + ( (Km + Km∗ pe r ) − (Km − Km∗ pe r ) ) ∗ rand ( 1 ) ;

### % Pl an t S t a t e Space M a t ri c e s

A = [ 0 1 ;
0 −B un/ J un ] ;
b = [ 0 ;
Km un/ J un ] ;

### % Adaptation Gains

g1 = 2 . 5 ;
g2 = 0 . 4 ;
g3 = 1 . 5 ;
Gx = [ g1 0 ;
0 g2 ] ;

### % Inc remen t i n p u t s i g n a l

### i f ( count == f l o o r ( p e ri o d / 3 ) )

r = r + r 0 ;
count = count + 1 ;

### end

### % S t a t e s

s t a t e = s t a t e ( : ) ;

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

### % Estimated E r r o r

e = x − x m ;
% di s p ( ” C alcu ted E r r o r ” ) ;

### % Sim ul a ti o n o f the system % C on t r ol Si g n al

u = Kx est ’ ∗ x + K r e s t ∗ r ; dx = A∗x + b∗u ;
dxm = Am∗x m + Bm∗ r ;

### % Adaptive l aw s

% dKx = −Gx∗x∗e ’ ∗P∗b ;
% dKr = −g3∗ r ∗e ’ ∗P∗b ;
dKx = Gx∗P r o j ( Kx est , −x∗e ’ ∗P∗b , 1 , 1e −2); dKr = g3∗P r o j ( K r e s t , −r ∗e ’ ∗P∗b , 1 , 1e −2); d s t a t e = [ dx ; dxm; dKx ; dKr ] ;

### end

### f u n c ti o n d s t a t e = MRACStepperNeuralNetwork ( t , s t a t e )

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

p e ri o d = t ( : , 1 ) ;
di s p ( ” Time Loop t = ” + p e ri o d + ” s e c ” ) ; r 0 = 0. 0 8 7 2 6 6;

### % Parameter U n c e r t a i n t i e s

pe r = 0 . 0 5 ;
B un = (B − B∗ pe r ) + ( (B + B∗ pe r ) − (B − B∗ pe r ) ) ∗ rand ( 1 ) ;

J un = ( J − J∗ pe r ) + ( ( J + J∗ pe r ) − ( J − J∗ pe r ) ) ∗ rand ( 1 ) ;
Km un = (Km − Km∗ pe r ) + ( (Km + Km∗ pe r ) − (Km − Km∗ pe r ) ) ∗ rand ( 1 ) ;

### % Pl an t S t a t e Space M a t ri c e s

A = [ 0 1 ;
0 −B un/ J un ] ;
b = [ 0 ;
Km un/ J un ] ;

### % Adaptation Gains

g3 = 8 ;
Gx = [ 1 0 0 ;
0 1 5 ] ;
Gtheta = [ . 4 0 0 0 0 ;
0 . 5 0 0 0 ;
0 0 . 3 0 0 ;
0 0 0 . 5 0 ;
0 0 0 0 . 8 ] ;

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

r = r + r 0 ;
count = count + 1 ;
di s p ( ” Inpu t has i n c r e a s e by 5 deg ! ” ) ;

### end

### % S t a t e s

s t a t e = s t a t e ( : ) ;

x = s t a t e ( 1 : 2 ) ;
x m = s t a t e ( 3 : 4 ) ;
Kx e s t = s t a t e ( 5 : 6 ) ;
K r e s t = s t a t e ( 7 ) ;
K t h e t a e s t = s t a t e (8:8+K−1);
T L1 = 1e−3∗( c o s ( 2∗ x ( 1 ) ) ) . ˆ 2 ∗ s i n ( 3∗ x ( 1 ) ) ; | % Nm

### % Estimated E r r o r

e = x − x m ;
% di s p ( ” C alcu ted E r r o r ” ) ;

### hi d d e n l a y e r o u t = ( ne t . LayerWeights {1})∗ x ( 1 )

+ ne t . L a y e rBi a s e s {1};

### f o r i = 1 :K

phi ( i , : ) = gaussm f ( h i d d e n l a y e r o u t ( i ) , [ 0 . 2 , 0 . 5 ] ) ;

### end

### % Sim ul a ti o n o f the system % C on t r ol Si g n al

% u = Kx est ’ ∗ x + K r e s t ∗ r ;
u = Kx est ’ ∗ x + K r e s t ∗ r + K t h e t a e s t ’ ∗ phi ; % dx = A∗x + b∗u ;
dx = A∗x + b∗( u − ( 1 /Km un)∗T L1 ) ;
dxm = Am∗x m + Bm∗ r ;

### % Adaptive l aw s

% dKx = −Gx∗x∗e ’ ∗P∗b ;
% dKr = −g3∗ r ∗e ’ ∗P∗b ;
% dKtheta = −Gtheta ∗ phi ∗e ’ ∗P∗b ;
dKx = Gx∗P r o j ( Kx est , −x∗e ’ ∗P∗b , 2 , 1e −3);
dKr = g3∗P r o j ( K r e s t , −r ∗e ’ ∗P∗b , 5 , 1e −3);
dKtheta = Gtheta ∗P r o j ( K t h e t a e s t , −phi ∗e ’ ∗P∗b , 1 , 1e −4);

d s t a t e = [ dx ; dxm; dKx ; dKr ; dKtheta ] ;

### end

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

### end

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

### end

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

### end

# Βιβλιογραφία

### [1] Iliya V. Miroshnik Alexander L. Fradkov and Vladimir O. Nikiforov. Nonlinear and Adaptive Control of Complex Systems. Springer, 1999. isbn: 978-94-015-9261-1. doi:

### 10.1007/978-94-015-9261-1. (https://doi.org/10.1007/978-94-015-9261-1)

[2] A. Astolfi and L. Marconi. Analysis and Design of Nonlinear Control Systems. Springer Berlin Heidelberg New York, 2008. isbn: 978-3-540-74357-6.
[3] Charalampos Bechlioulis. Simulation of Dynamical Systems. 2021.

### [4] Jay A. Farrell and Marios M. Polycarpou. Adaptive Approximation Based Control: Unifying Neural, Fuzzy and Traditional Adaptive Approximation Approaches. John Wiley Sons, Inc., 2006. isbn: 978-0-471-72788-0. doi: 10.1007/978-0-471-72788-

### 0. (https://doi.org/10.1007/978-0-471-72788-0)

### [5] Mohammed M’Saad Alireza Karimi Ioan Doré Landau Rogelio Lozano. Adaptive

Control: Algorithms, Analysis and Applications. Second Edition. Springer, 2011. isbn: 978-0-85729-664-1. doi: 10.1007/978-0-85729-664-1. (https://doi.org/10.1007/978-0-85729-664-1)

[6] Petros A. Ioannou and Jing Sun. Robust Adaptive Control. Dover Publications, 2012. isbn: 978-0486498171.

### [7] Alberto Isidori. Nonlinear Control Systems. 3rd Edition. Springer, 1995. isbn: 978-

1-84628-615-5. doi: 10.1007/978-1-84628-615-5. (https://doi.org/10.1007/978-1-84628-615-5)

[8] Hassan K. Khalil. Nonlinear Systems. 3rd Edition. Pearson, 2001. isbn: 978-0130673893.

### [9] Craig A. Kluever. Dynamic Systems: Modeling, Simulation, and Control. John Wiley

Sons, Inc., 2015. isbn: 978-1-118-28945-7. doi: 10.1007/978-1-118-28945-7. (https://doi.org/10.1007/978-1-118-28945-7)

[10] Jinkun Liu. Intelligent Control Design and MATLAB Simulation. Springer, 2018. isbn: 978-981-10-5263-7. doi: https://doi.org/10.1007/978-981-10-5263-7. (https://doi.org/https://doi.org/10.1007/978-981-10-5263-7)
[11] Norm S. Nise. Control Systems Engineering. 8th Edition. John Wiley Sons, 2019. isbn: 978-1119590132.

### [12] P.Ioannou and B. Fidan. Adaptive Control Tutorial. SIAM, 2006. isbn: 978-0-89871-

### 615-3. doi: 10.1007/978-0-89871-615-3. (https://doi.org/10.1007/978-0-89871-615-3)

### [13] V.P. Singh Rajesh Kumar and Akhilesh Mathur. Intelligent Algorithms for Analysis and Control of Dynamical Systems. Springer, 2021. isbn: 978-981-15-8045-1. doi:

### 10.1007/978-981-15-8045-1. (https://doi.org/10.1007/978-981-15-8045-1)

[14] Jean-Jacques E. Slotine and Weiping Li. Applied Nonlinear Control. Prentice Hall, 1991. isbn: 0-13-040890-5.
[15] Spyros G. Tzafestas. Methods and Applications of Intelligent Control. Springer, 1997. isbn: 978-94-011-5498-7. doi: 10.1007/978-94-011-5498-7. (https://doi.org/10.1007/978-94-011-5498-7)
