GeoKrom/NTUA-Intelligent-Control-Systems-and-Robotic-Systems-course/Exercises/Exercise-2/Assignment 2.pdf

Εθνικό Μετσόβιο Πολυτεχνείο

Σχολή Μηχανολόγων μηχανικών

ΔΠΜΣ Συστήματα αυτοματισμού

Κατεύθυνση Β: Συστήματα Αυτομάτου Ελέγχου και Ρομποτικής

### Μεταπτυχιακό Μάθημα:

Ευφυή Συστήματα Ελέγχου και Ρομποτικής

Ονομ/νυμο - Α.Μ.:

Γεώργιος Κρομμύδας - 02121208

### Δεύτερη Σειρά Ασκήσεων: MIT Rule


## Αθήνα, 2023

# Πίνακας Περιεχομένων

Κατάλογος Σχημάτων | 2
1 ΄Ασκηση 1 | 3
2 ΄Ασκηση 2 | 11
Αʹ Κώδικας Προσομοίωσης | 21
Βιβλιογραφία | 27

1

# Κατάλογος Σχημάτων

1.2 Προσομοίωση Συστήματος κλειστού βρόχου με τιμές γ = 0.2, ζ = 0.707 και

1.3 Προσομοίωση Συστήματος κλειστού βρόχου με τιμές γ = 0.2, ζ = 0.707 και

1.4 Προσομοίωση Συστήματος κλειστού βρόχου με τιμές γ = 0.5, ζ = 0.707 και

1.5 Προσομοίωση Συστήματος κλειστού βρόχου με τιμές γ = 1, ζ = 1 και ω = 10. 10

2.2 Προσομοίωση συστήματος με παραμέτρους μοντέλου αναφοράς am = 2, bm =

2.3 Προσομοίωση συστήματος με παραμέτρους μοντέλου αναφοράς am = 2, bm =

2.4 Προσομοίωση συστήματος με παραμέτρους μοντέλου αναφοράς am = 2, bm =

2.5 Προσομοίωση συστήματος με παραμέτρους μοντέλου αναφοράς am = 5, bm =

2.6 Προσομοίωση συστήματος με παραμέτρους μοντέλου αναφοράς am = 5, bm =

2.7 Προσομοίωση συστήματος με παραμέτρους μοντέλου αναφοράς am = 5, bm =

2

# Κεφάλαιο 1

# ΄Ασκηση 1

Μας δίνεται η συνάρτηση μεταφοράς μιας διεργασίας η οποία είναι:

### P(s) = 1 s(s + a)

(1.1)

όπου η παράμετρος a είναι μια άγνωστη σταθερά. Θα σχεδιάσουμε έναν ελεγκτή για το παρα-

πάνω σύστημα που θα βασιστεί στον νόμο προσαρμογής MIT Rule. Ο στόχος του ελεγκτή

είναι να παρακολουθήσει το μοντέλο αναφορά:

M(s) = | ω

2

s

| 2 + 2ζωs + ω²

(1.2)

όπου τα ζ, ω > 0 είναι οι παράμετροι της συνάρτησης μεταφοράς.

## 1.1 Σχεδίαση Ελεγκτή

Γνωρίζουμε πως το σύστημα προς έλεγχο είναι δεύτερης τάξης. Συνεπώς, μια καλή λύση για το

σύστημα είναι ο ελεγκτής που θα χρησιμοποιήσουμε να είναι τύπου P D μαζί με feedfoward.

΄Ετσι, δε θα έχουμε αστάθεια στο σύστημα κλειστού βρόχου. Αυτή η λύση αποτελεί καλύτερη

επιλογή καθώς μόνο με τη χρήση του P όρου θα έπεφτε σε αστάθεια. Αυτό θα οφειλόταν στο

γεγονός πως δε θα είχαν τοποθετηθεί σωστά και οι δύο πόλοι του συστήματος στο αρνητικό

ημιεπίπεδο του φανταστικού άξονα. ΄Ετσι, με αυτό το σκεπτικό έχουμε τον εξής νόμο ελέγχου:

u = ϑ1r − ϑ2yp − ϑ3y˙p | (1.3)

Το επόμενο βήμα είναι να βρούμε την έξοδο των συστημάτων αναφοράς και διεργασίας.

Οπότε ισχύει ότι:

### yp = P(s)u

⇒ yp =

1

### s(s + a)

## (ϑ1r − ϑ2yp − ϑ3y˙p)

⇒ (s

### 2 + (a + ϑ3)s + ϑ2)yp = ϑ1r

⇒ yp =

ϑ1
s

### 2 + (a + ϑ3)s + ϑ2

r | (1.4)

3

΄Ασκηση 1 | 4

Τώρα θα βρούμε και τη σχέση της εξόδου του μοντέλου αναφοράς:

### ym = M(s)r

⇒ ym =

ω

2

s

### 2 + 2ζωs + ω²

r | (1.5)

Το επόμενο βήμα είναι να ορίσουμε το σφάλμα παρακολούθησης του συστήματος και να

ορίσουμε τους νόμους προσαρμογής των παραμέτρων. Συνεπώς, ισχύει ότι:

e0 = yp − ym | (1.6)

Ο γενικός νόμος προσαρμογής της μεθόδου MIT Rule είναι ο:

ϑ˙ = −γ

′ ∂e0
∂ϑ e0 | (1.7)

Οπότε, Θα συνδυάσουμε τις σχέσεις (1.4), (1.5) και (1.6) και θα υπολογίσουμε τις μερικές

παραγώγους του σφάλματος παρακολούθησης ως προς τις παραμέτρους του ελεγκτή. Για την

πρώτη παράμετρο ισχύει ότι:

∂e0
∂ϑ1

=

∂
∂ϑ1
ϑ1
s

### 2 + (a + ϑ3)s + ϑ2

r −

ω

2

s

### 2 + 2ζωs + ω²

r

⇒

∂e0
∂ϑ1

=

1
s

### 2 + (a + ϑ3)s + ϑ2

r | (1.8)

Για τη δεύτερη παράμετρο ισχύει ότι:

∂e0
∂ϑ2

=

∂
∂ϑ2
ϑ1
s

### 2 + (a + ϑ3)s + ϑ2

r −

ω

2

s

### 2 + 2ζωs + ω²

r

= −

ϑ1
(s

### 2 + (a + ϑ3)s + ϑ2)

2

r

= −

1
s

### 2 + (a + ϑ3)s + ϑ2

ϑ1
s

### 2 + (a + ϑ3)s + ϑ2

r

∂e0
∂ϑ2

= −

1
s

### 2 + (a + ϑ3)s + ϑ2

yp | (1.9)

Για την τρίτη παράμετρο ισχύει το εξής:

∂e0
∂ϑ3

=

∂
∂ϑ3
ϑ1
s

### 2 + (a + ϑ3)s + ϑ2

r −

ω

2

s

### 2 + 2ζωs + ω²

r

= −

sϑ1
(s

### 2 + (a + ϑ3)s + ϑ2)

2

r

= −

s
s

### 2 + (a + ϑ3)s + ϑ2

ϑ1
s

### 2 + (a + ϑ3)s + ϑ2

r

΄Ασκηση 1 | 5

= −

s
s

### 2 + (a + ϑ3)s + ϑ2

yp

∂e0
∂ϑ3

= −

1
s

### 2 + (a + ϑ3)s + ϑ2

y˙p | (1.10)

Τώρα θα κάνουμε την εξής προσέγγιση:

s

### 2 + (ϑ3 + a)s + ϑ2 ≈ s

2 + (ϑ

∗

### 3 + a)s + ϑ

∗
2 = s

### 2 + 2ζωs + ω

2
(1.11)

Το επόμενο βήμα είναι να χρησιμοποιήσομε την σχέση (1.7) και να βρούμε τους νόμους

προσαρμογής. Επίσης, θα χρησιμοποιήσουμε και την προσέγγιστη της σχέσης (1.11). Ως

κέρδος θα ορίσουμε την ποσότητα γ

### ′ = γω²

, έτσι ώστε να σχηματιστεί το κατάλληλο φίλτρο

για τος νόμους ελέγχου. Οπότε, οι νόμοι ελέγχου θα γίνουν οι εξής:

ϑ˙
1 = −γ

′ ∂e0
∂ϑ1

e0

ϑ˙
1 = −γ
ω2
s

### 2 + 2ζωs + ω²

r

e0 | (1.12)

ϑ˙
2 = −γ

′ ∂e0
∂ϑ2

e0

ϑ˙
2 = γ
ω

2

s

### 2 + 2ζωs + ω²

yp

e0 | (1.13)

ϑ˙
3 = −γ

′ ∂e0
∂ϑ3

e0

ϑ˙
3 = γ
ω

2

s

### 2 + 2ζωs + ω²

y˙p

e0 | (1.14)

Με τους νόμους (1.12), (1.13) και (1.14) μπορούμε να αλλάξουμε τους πόλους και τα μηδε-

νικά του συστήματος, έτσι ώστε να προσεγγίζει το μοντέλο αναφοράς. ΄Ενα μπλοκ διάγραμμα

του συστήματος φαίνεται και στο σχήμα 1.1

΄Ασκηση 1 | 6

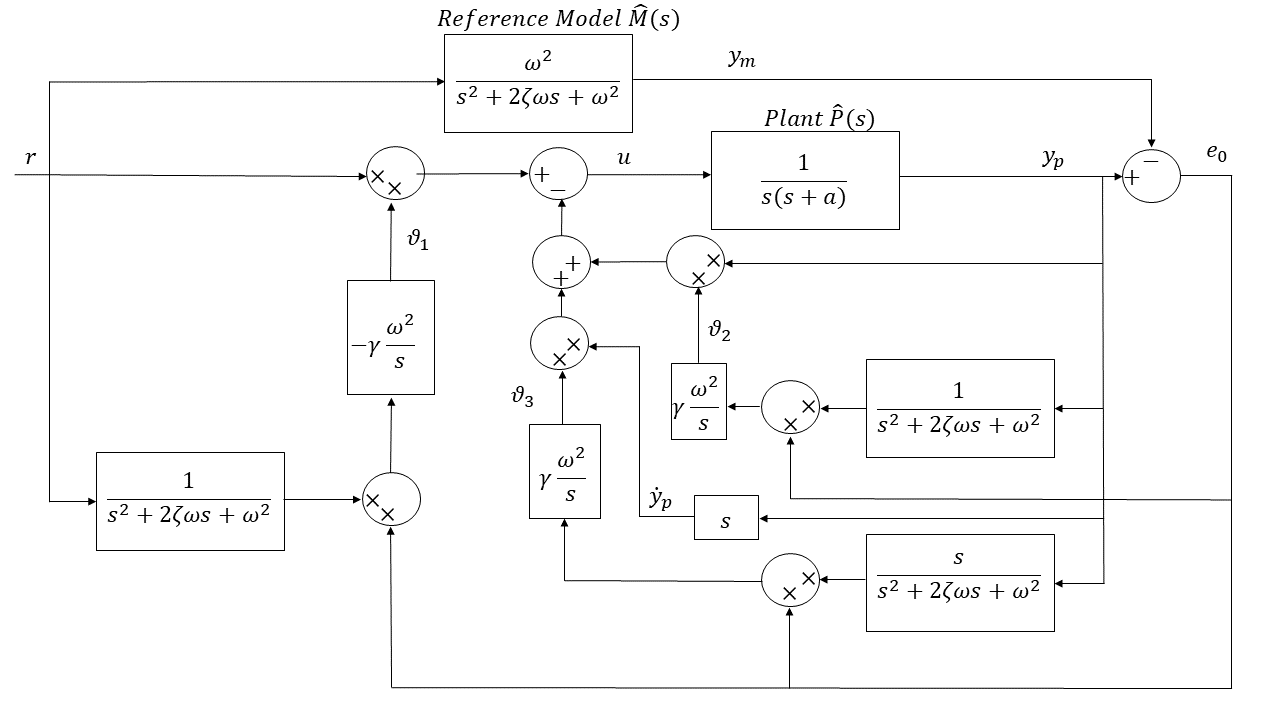
[picture p141: figure]

Σχήμα 1.1: Μπλοκ διάγραμμα ελεγκτή MIT Rule.

΄Ασκηση 1 | 7
1.2 | Προσομοίωση Ελεγκτή

Το επόμενο βήμα είναι να προσομοιώσουμε το παραπάνω σύστημα με τους νόμους αυτούς, έτσι

ώστε να δούμε εάν λειτουργεί σωστά. Τα πειράματα έγιναν με διάφορες τιμές των παραμέτρων

και διαφορετικές εισόδους. Συγκεκριμένα, θα παρουσιαστούν παρακάτω τα αποτελέσματα με

ένα σύνολο παραμέτρων, το οποίο είχε ενδιαφέρον αποτελέσματα ως προς τη σύγκλιση των

παραμέτρων στις επιθυμητές τιμές και της εξόδου στο μοντέλο αναφοράς. Η παράμετρος a

προσομοιώθηκε με τιμές 4 και −5. Η παράμετρος ζ προσομοιώθηκε με τις τιμές 0.707 και 1.

Τέλος, η παράμετρος ω προσομοιώθηκε με τις τιμές 1rad/sec και 10rad/sec. Στο σύστημα

κλειστού βρόχου εφαρμόστηκαν τρεις διαφορετικές είσοδοι. Η πρώτη είσοδος αποτελείται

από μία βηματική συνάρτηση. Η δεύτερη είσοδος που εφαρμόστηκε αποτελείται από μία η-

μιτονοειδής συνάρτηση. Τέλος, η τρίτη είσοδος που εφαρμόστηκε αποτελείται από άθροισμα

ημιτονοειδών συναρτήσεων διαφορετικών συχνοτήτων.

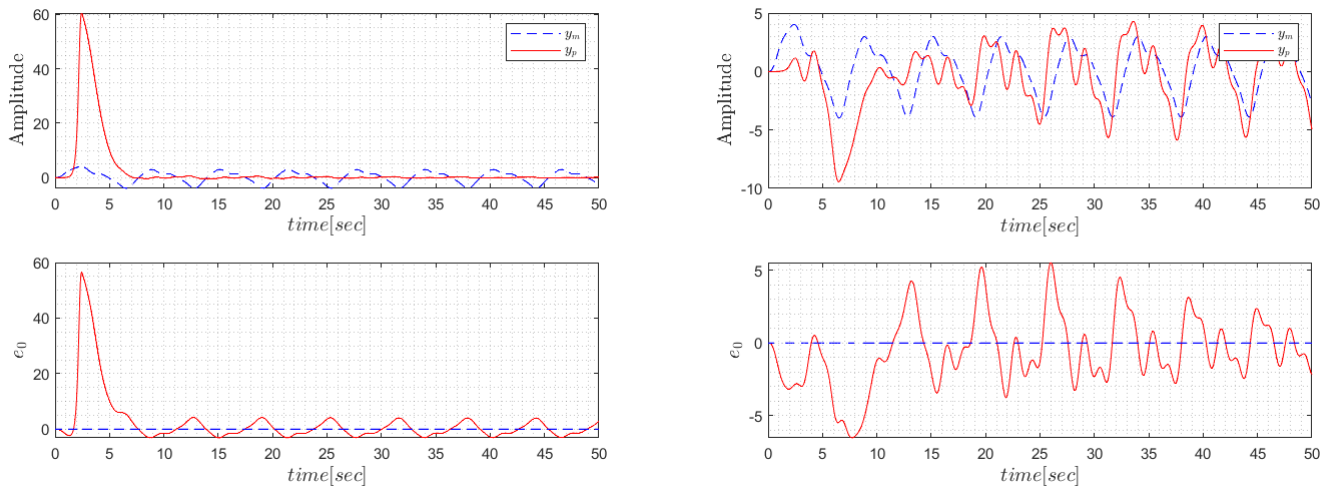
[picture p142: figure]

(αʹ) ΄Εξοδοι συστήματος και σφάλμα παρακολούθησης με τον πόλο στο a = −5.

(βʹ) ΄Εξοδοι συστήματος και σφάλμα παρακο-

λούθησης με τον πόλο στο a = 4.

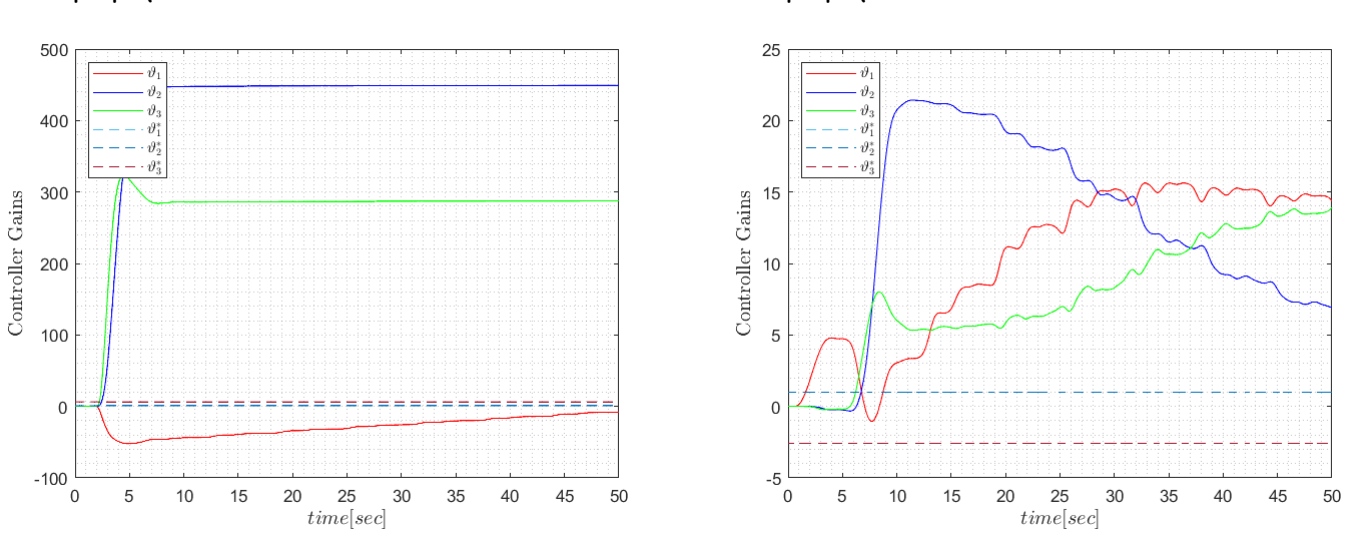
[picture p143: figure]

(γʹ) Εκτίμηση παραμέτρων ελεγκτή με τον πόλο στο a = −5.

(δʹ) Εκτίμηση παραμέτρων ελεγκτή με τον

πόλο στο a = 4.

Σχήμα 1.2: Προσομοίωση Συστήματος κλειστού βρόχου με τιμές γ = 0.2, ζ = 0.707 και
ω = 1.

Στο σχήμα 1.2 παρατηρούμε την προσομοίωση του συστήματος με τις ίδεις παραμέτρους,

ωστόσο με διαφορετικές τιμές στους πόλους της διεργασίας. Με το επιλεγμένο σετ παρα-

μέτρων παρατηρούμε πως στην πρώτη περίπτωση η έξοδος δε συγκλίνει ακριβώς στο μοντέλο

αναφορά και οι παράμετροι του ελεγκτή δε συγκλίνουν στις επιθυμητές τιμές του. ΄Ενα πρόβλη-

μα εμφανίζεται στην επιλογή της συχνότητας ω. Μία μεγαλύτερη τιμή θα μπορούσε να εξο-

΄Ασκηση 1 | 8

μαλύνει τη λειτουργία του ελεγκτή και να αποκόψει τις υψηλές συχνότητες του συστήματος.

΄Ετσι, το πρόβλημα αυτό μπορεί να λυθεί με την αλλαγή των παραμέτρων. Εάν αντί για ω = 1

επιλέξουμε ω = 10, τότε θα έχουμε ένα καλύτερο αποτέλεσμα ως προς την τοποθέτηση των

πόλων του συστήματος.

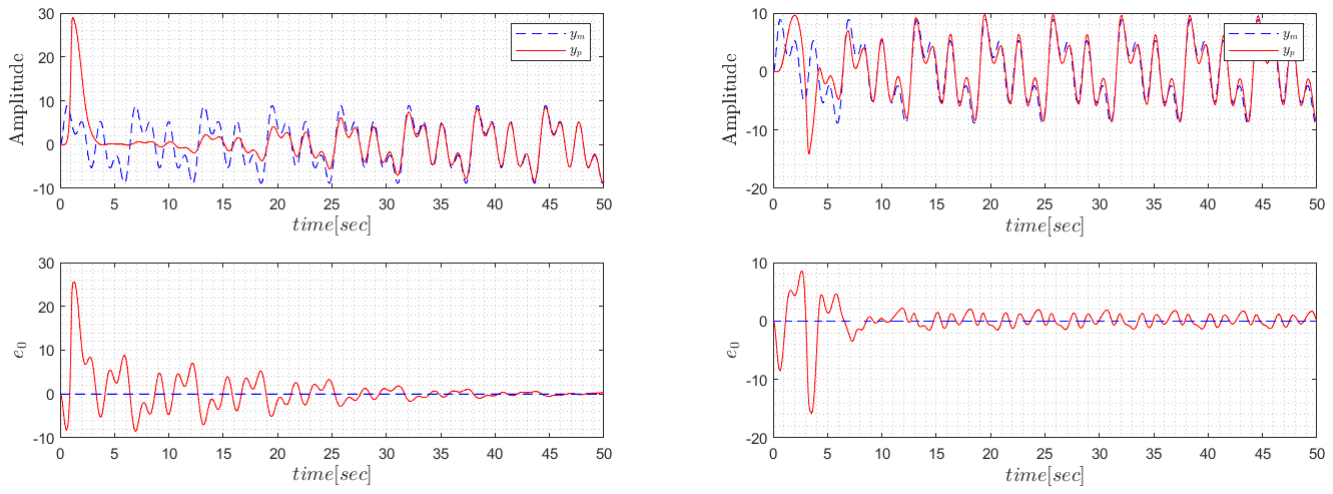
[picture p144: figure]

(αʹ) ΄Εξοδοι συστήματος και σφάλμα παρακολούθησης με τον πόλο στο a = −5.

(βʹ) ΄Εξοδοι συστήματος και σφάλμα παρακο-

λούθησης με τον πόλο στο a = 4.

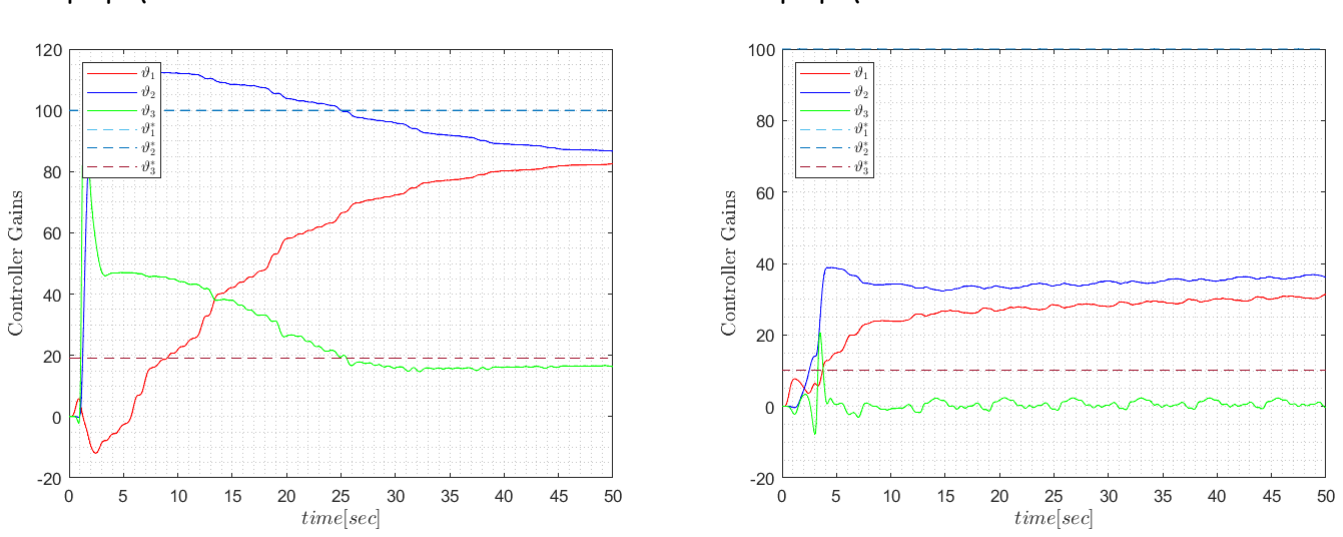
[picture p145: figure]

(γʹ) Εκτίμηση παραμέτρων ελεγκτή με τον πόλο στο a = −5.

(δʹ) Εκτίμηση παραμέτρων ελεγκτή με τον

πόλο στο a = 4.

Σχήμα 1.3: Προσομοίωση Συστήματος κλειστού βρόχου με τιμές γ = 0.2, ζ = 0.707 και
ω = 10.

΄Οπως παρατηρούμε από το σχήμα 1.3 το πραγματικό σύστημα προσεγγίζει καλύτερα το

μοντέλο αναφοράς και μάλιστα με μικρότερα σφάλματα. Ωστόσο, αυτό δε συνεπάγεται πως

και οι παράμετροι του συστήματος συγκλίνουν στις επιθυμητές τιμές. Μία λύση είναι να

αυξήσουμε το κέρδος γ στον ελεγκτή μας. Την επιλέγουμε την τιμή ως 0.5. Το αποτέλεσμα

της προσομοίωσης παρουσιάζεται στο σχήμα 1.4. Το σφάλμα παρακολούθησης σύγκλινε

γρηγορότερα στο μηδέν, ωστόσο οι παράμετροι δεν πήγαν στις επιθυμητές τιμές.

΄Ασκηση 1 | 9

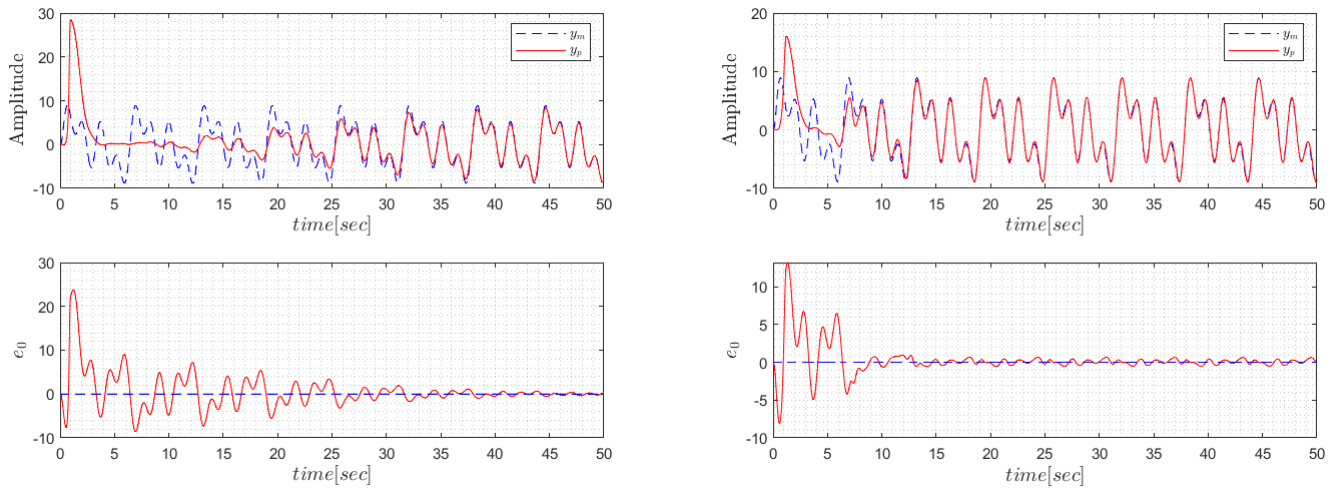
[picture p146: figure]

(αʹ) ΄Εξοδοι συστήματος και σφάλμα παρακολούθησης με τον πόλο στο a = −5.

(βʹ) ΄Εξοδοι συστήματος και σφάλμα παρακο-

λούθησης με τον πόλο στο a = 4.

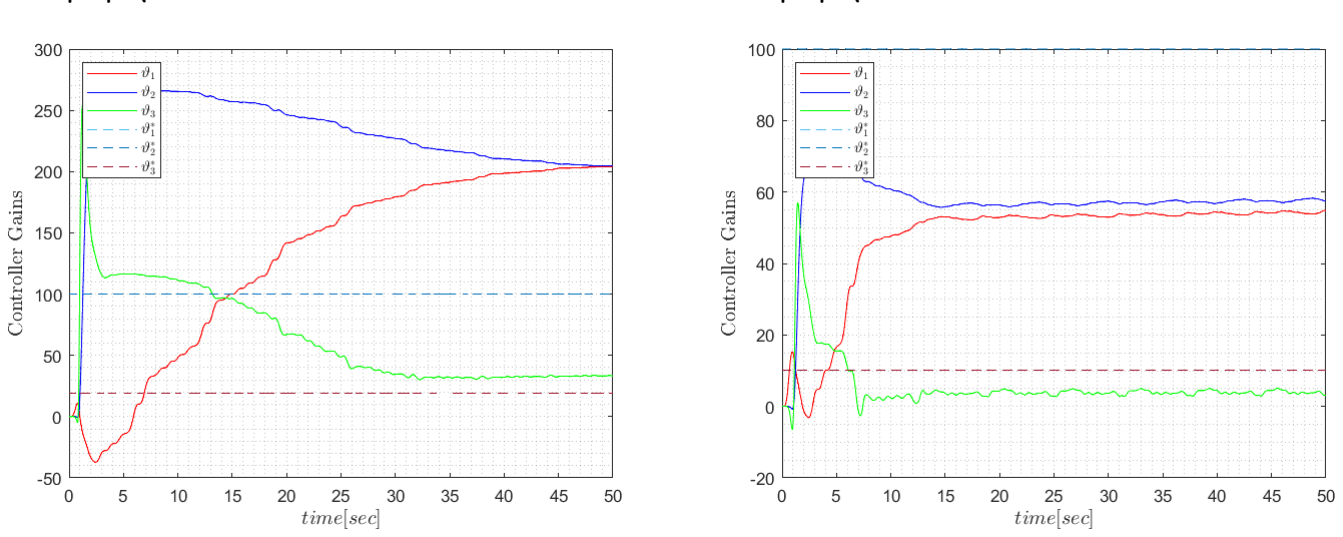
[picture p147: figure]

(γʹ) Εκτίμηση παραμέτρων ελεγκτή με τον πόλο στο a = −5.

(δʹ) Εκτίμηση παραμέτρων ελεγκτή με τον

πόλο στο a = 4.

Σχήμα 1.4: Προσομοίωση Συστήματος κλειστού βρόχου με τιμές γ = 0.5, ζ = 0.707 και
ω = 10.

Ακόμα ένα τελευταίο βήμα είναι να αυξήσουμε και την παράμετρο ζ από το 0.707 στο 1.

Επίσης, αυξάνουμε και το κέρδος γ στην τιμή 1. Στο σχήμα 1.5 παρατηρείται η προσομοίωση

του συστήματος. Βλέπουμε πως η σύγκλιση του σφάλματος παρακολούθησης γίνεται σε

μικρότερο χρόνο. Ωστόσο, οι παράμετροι ϑi δε συγκλίνουν στις επιθυμητές τιμές.

΄Ασκηση 1 | 10

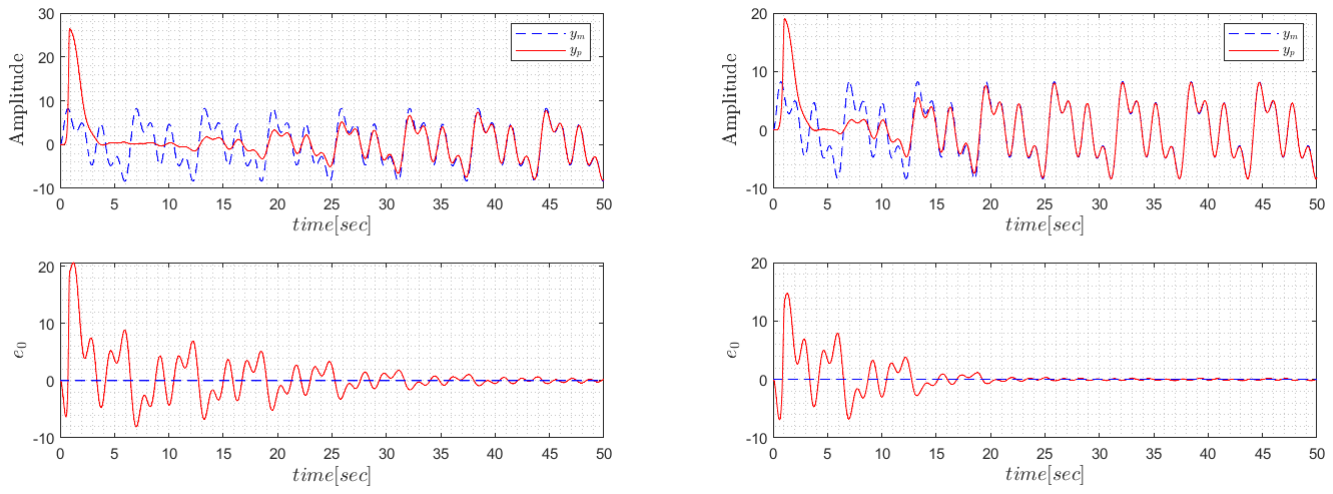
[picture p148: figure]

(αʹ) ΄Εξοδοι συστήματος και σφάλμα παρακολούθησης με τον πόλο στο a = −5.

(βʹ) ΄Εξοδοι συστήματος και σφάλμα παρακο-

λούθησης με τον πόλο στο a = 4.

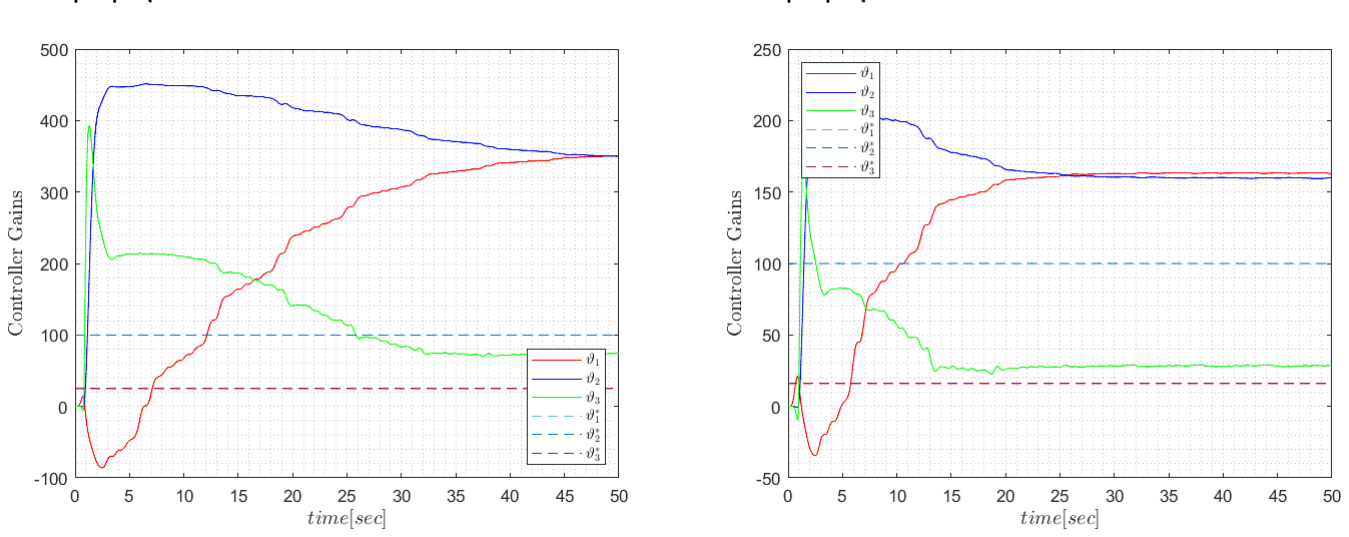
[picture p149: figure]

(γʹ) Εκτίμηση παραμέτρων ελεγκτή με τον πόλο στο a = −5.

(δʹ) Εκτίμηση παραμέτρων ελεγκτή με τον

πόλο στο a = 4.

Σχήμα 1.5: Προσομοίωση Συστήματος κλειστού βρόχου με τιμές γ = 1, ζ = 1 και ω = 10.

Το πρόβλημα της σύγκλισης των παραμέτρων πηγάζει από την ίδια την ευστάθεια του

συστήματος. Καθώς οι προσαρμοστικοί νόμοι εγγυούνται μόνο ευστάθεια στο σύστημα και

όχι ασυμπτωτική, τότε η μόνη λύση είναι να κανονικοποιήσουμε τα σήματα του συστήματος.

΄Ετσι, θα έχουμε μια πιο ισχυρή συνθήκη P E. Επιπλέον, η αύξηση του κέρδους γ θα είχε

αρνητικές επιπτώσεις στο σύστημα, καθώς οι παράμετροι του συστήματος θα έχουνε μεγάλες

τιμές και η λύση του συστήματος θα εκτοξευθεί ακαριαία. Συνεπώς, μια καλή λύση του

προβλήματος αποτελεί η επιλογή των παραμέτρων (γ, ζ, ω) = (1, 1, 10). ΄Ετσι, το σύστημα

θα συγκλίνει στο μοντέλο αναφοράς και οι παράμετροι του ελεγκτή θα βρίσκονται κοντά στις

περιοχές των επιθυμητών τους τιμών.

# Κεφάλαιο 2

# ΄Ασκηση 2

Μας δίνεται η συνάρτηση μεταφοράς μιας διεργασίας η οποία είναι:

### P(s) = b

s

(2.1)

όπου η παράμετρος b είναι μια άγνωστη σταθερά. Θα σχεδιάσουμε έναν ελεγκτή για το παρα-

πάνω σύστημα που θα βασιστεί στον νόμο προσαρμογής MIT Rule. Ο στόχος του ελεγκτή

είναι να παρακολουθήσει το μοντέλο αναφορά:

### M(s) = am s + bm

(2.2)

όπου τα am > 0, bm > 0 αποτελούν τις παραμέτρους του μοντέλου αναφοράς.

## 2.1 Σχεδίαση Ελεγκτή

Το σύστημα το οποίο θέλουμε να ελέγξουμε είναι πρώτης τάξης. Οπότε, ως σύστημα ελέγχου

θα ορίσουμε τον εξής:
u = ϑ1r − ϑ2yp | (2.3)

όπου οι παράμετροι ϑ1 και ϑ2 αποτελούν τις παραμέτρους του ελεγκτή οι οποίοι βασίζο-

νται στον προσαρμοστικό νόμο του MIT Rule. Η μορφή του ελεγκτή είναι τύπου P και

feedfoward, καθώς θέλουμε να τοποθετήσουμε τον πόλο του συστήματος στο 0 και να ρυθ-

μίσουμε κατάλληλα το κέρδος του αριθμητή. Το επόμενο βήμα είναι να βρούμε την έξοδο των

συστημάτων αναφοράς και διεργασίας. Οπότε ισχύει ότι:

### yp = P(s)u

⇒ yp =

b
s

## (ϑ1r − ϑ2yp)

### ⇒ (s + bϑ2)yp = bϑ1r

⇒ yp =

bϑ1

### s + bϑ2

r | (2.4)

11

΄Ασκηση 2 | 12

Τώρα θα βρούμε και τη σχέση της εξόδου του μοντέλου αναφοράς:

### ym = M(s)r

⇒ ym =

am

### s + bm

r | (2.5)

Συνεπώς, θα ορίσουμε το σφάλμα παρακολούθησης των μοντέλων ως εξής:

e0 = yp − ym | (2.6)

Ο γενικός νόμος προσαρμογής της μεθόδου MIT Rule είναι ο:

ϑ˙ = −γ

′ ∂e0
∂ϑ e0 | (2.7)

Οπότε, Θα συνδυάσουμε τις σχέσεις (2.4), (2.5) και (2.6) και θα υπολογίσουμε τις μερικές

παραγώγους του σφάλματος παρακολούθησης ως προς τις παραμέτρους του ελεγκτή. Για την

πρώτη παράμετρο ισχύει ότι:

∂e0
∂ϑ1

=

∂
∂ϑ1
bϑ1

### s + bϑ2

r −

am

### s + bm

r

⇒

∂e0
∂ϑ1

=

b

### s + bϑ2

r | (2.8)

Για τη δεύτερη παράμετρο ισχύει ότι:

∂e0
∂ϑ2

=

∂
∂ϑ2
bϑ1

### s + bϑ2

r −

am

### s + bm

r

= −

b

2ϑ1

### (s + bϑ2)

2

r

= −

b

### s + bϑ2

bϑ1

### s + bϑ2

r

∂e0
∂ϑ2

= −

b

### s + bϑ2

yp | (2.9)

Οι εξισώσεις που προέκυψαν δεν μπορούν να υλοποιηθούν λόγω της άγνωστης παραμέτρου

b. ΄Ετσι, θα κάνουμε την εξής προσέγγιση:

### s + bϑ2 ≈ s + bϑ∗

2 = s + am | (2.10)

Με τη σχέση (2.10) μπορούμε να τροποποιήσουμε τις σχέσεις (2.8) και (2.9) ως εξής:

∂e0
∂ϑ1

=

b

### s + am

r | (2.11)

΄Ασκηση 2 | 13

∂e0
∂ϑ2

= −

b

### s + am

yp | (2.12)

Το επόμενο βήμα είναι να χρησιμοποιήσουμε τη σχέση (2.7) και να βρούμε τους νόμους

προσαρμογής. Ως κέρδος θα ορίσουμε την ποσότητα γ

′ = γ
am
b
| , έτσι ώστε να σχηματιστεί το

κατάλληλο φίλτρο για τους νόμους ελέγχου. Οπότε, οι νόμοι ελέγχου θα γίνουν οι εξής:

ϑ˙
1 = −γ

′ ∂e0
∂ϑ1

e0

ϑ˙
1 = −γ
am

### s + am

r

e0 | (2.13)

ϑ˙
2 = −γ

′ ∂e0
∂ϑ2

e0

ϑ˙
2 = γ
am

### s + am

yp

e0 | (2.14)

Με τους νόμους (2.13) και (2.14) μπορούμε να αλλάξουμε τον πόλο του συστήματος, έτσι

ώστε να προσεγγίζει το μοντέλο αναφοράς. Επιπλέον, για να έχει νόημα η παραπάνω ανάλυση

και λειτουργεί σωστά ο ελεγκτής, θα πρέπει να υποθέσουμε πως η άγνωστη παράμετρος του

συστήματος b, θα πρέπει να είναι θετική και διαφορετική του μηδενός. Διαφορετικά, οι νόμοι

αυτοί δε θα μπορέσουν να λειτουργήσουν σωστά. ΄Ενα μπλοκ διάγραμμα του συστήματος

φαίνεται και στο σχήμα 2.1.

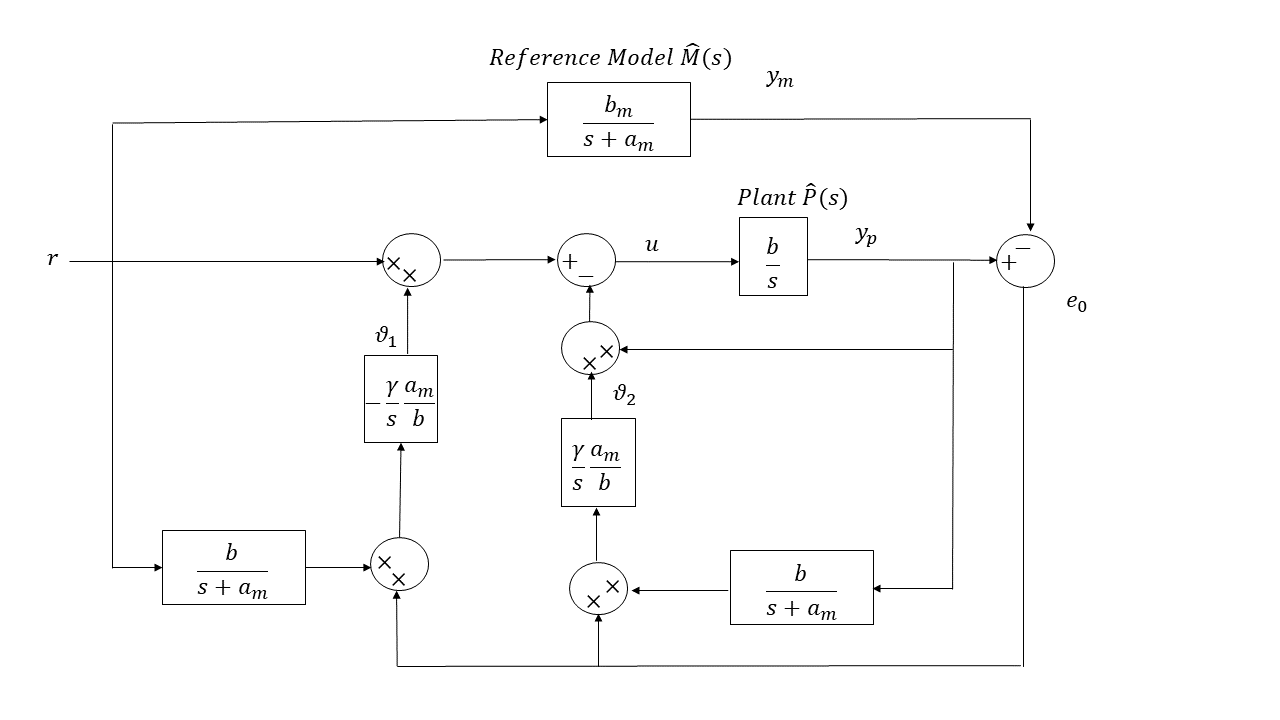
[picture p150: figure]

Σχήμα 2.1: Μπλοκ διάγραμμα ελεγκτή MIT Rule.

΄Ασκηση 2 | 14
2.2 | Προσομοίωση Ελεγκτή

΄Εχουμε σχεδιάσει τον ελεγκτή μας και το επόμενο βήμα είναι να τον προσομοιώσουμε με

επιλογή των παραμέτρων του πραγματικού συστήματος και του μοντέλου αναφοράς. Μετά

από προσομοιώσεις και επιλογή των παραμέτρων, χρησιμοποιήθηκαν για το b = 1 και b =

3. Για το μοντέλο αναφοράς χρησιμοποιήθηκαν οι τιμές am = 2, am = 5 και bm = 1,

bm = 12. Επίσης, για το κέρδος γ χρησιμοποιήθηκαν οι τιμές 0.2, 0.5 και 1. Τέλος, ως

είσοδο στο σύστημα εφαρμόστηκε μια βηματική, μία ημιτονοειδής και μία ημιτονοειδής με

τρεις διαφορετικές συχνότητες.

Εξ αρχής διαπιστώνουμε πως η βηματική απόκριση δεν πρόκειται να επιφέρει σύγκλιση

στις παραμέτρους καθώς δεν ισχύει η συνθήκη P E. ΄Ετσι, με τις άλλες δύο εισόδους θα

εμφανίζονται καλύτερα αποτελέσματα. Παρακάτω, θα παρουσιαστούν τα αποτελέσματα των

προσομοιώσεων. Ως αρχική επιλογή για το μοντέλο αναφοράς, θα χρησιμοποιήσουμε τις τιμές

am = 2 και bm = 1. Θα συγκρίνουμε τα αποτελέσματα με την πραγματική παράμετρος του

συστήματος μα έχει τις τιμές 1 και 3. Στο σχήμα 2.2 βλέπουμε την απόκριση του συστήματος

με κέρδος προσαρμογής γ = 0.2. Αυτό που παρατηρούμε στις αποκρίσεις είναι πως το σφάλμα

παρακολούθησης μηδενίζεται γρήγορα και στις δύο περιπτώσεις. Επίσης, παρατηρούμε πως

και οι εκτιμήσεις των παραμέτρων συγκλίνουν στις πραγματικές τιμές. Στην πρώτη περίπτωση

βλέπουμε πως γίνεται πιο ομαλή η σύγκλιση σε σχέση με τη δεύτερη περίπτωση.

΄Ασκηση 2 | 15

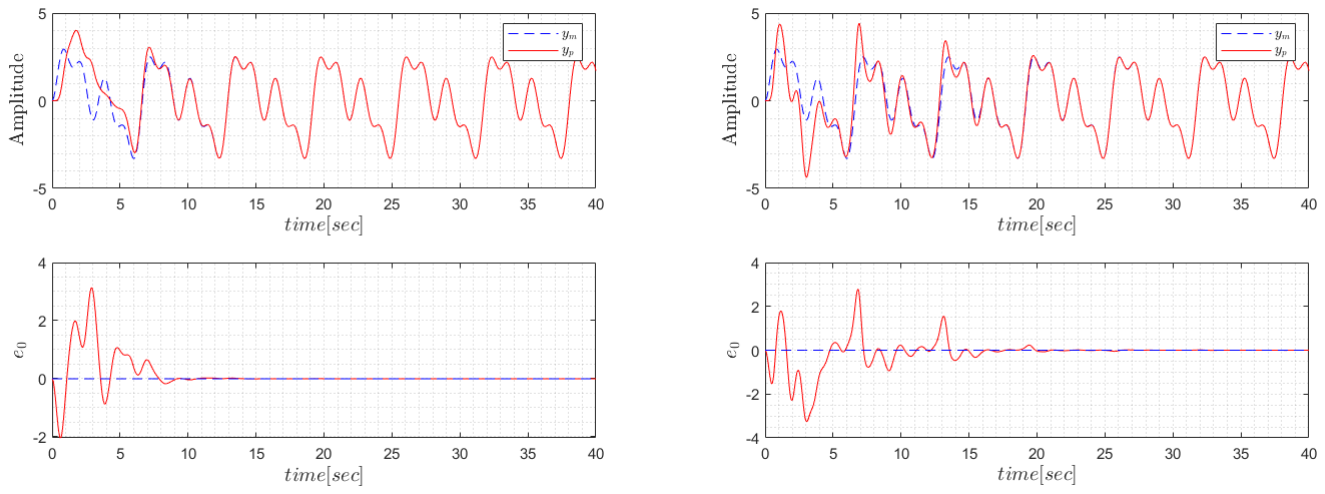
[picture p151: figure]

(αʹ) Απόκριση εξόδου συστήματος και σφάλ-

μα παρακολούθησης με παράμετρο συστήματος b = 1.

(βʹ) Απόκριση εξόδου συστήματος και σφάλ-

μα παρακολούθησης με παράμετρο συστήματος b = 3.

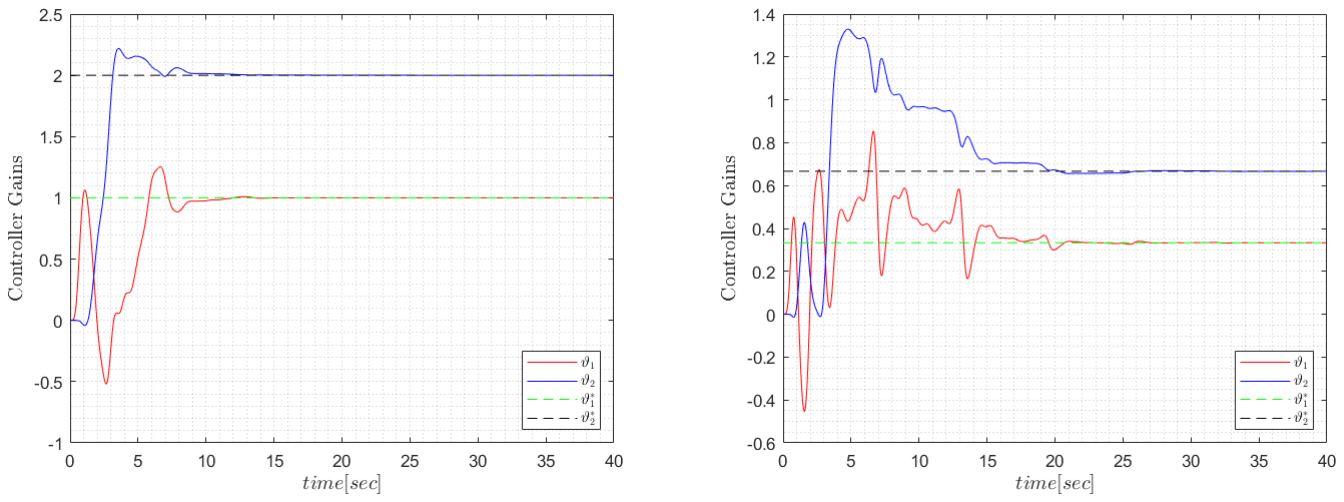
[picture p152: figure]

(γʹ) Εκτίμηση παραμέτρων ελεγκτή με πα-

ράμετρο συστήματος b = 1..

(δʹ) Εκτίμηση παραμέτρων ελεγκτή με παράμε-

τρο συστήματος b = 3.

Σχήμα 2.2: Προσομοίωση συστήματος με παραμέτρους μοντέλου αναφοράς am = 2, bm = 1

και κέρδους γ = 0.2.

Τώρα θα αυξήσουμε το κέρδος του προσαρμοστικού νόμου, έτσι ώστε να αντικρίσουμε τις

επιπτώσεις που εμφανίζονται στο σχήμα 2.3. Πράγματι αυτό που παρατηρούμε είναι πως στην

δεύτερη περίπτωση δεν έχουμε σύγκλιση ούτε του πραγματικού μοντέλου στο επιθυμητό αλλά

ούτε και των εκτιμήσεων των παραμέτρων. Η αύξηση του ρυθμού στην ουσία δεν αφήνει το

φίλτρο να δράσει σωστά και να αποκόψει τις υψηλές συχνότητες του συστήματος. Αντιθέτως,

το σύστημα με παράμετρο b = 1 λειτουργεί σωστά και συγκλίνουν κανονικά οι εκτιμήσεις

των παραμέτρων στις πραγματικές τιμές. Επιπλέον, η απόκριση του πραγματικού συστήματος

συγκλίνει σωστά και παρακολουθεί την απόκριση του μοντλεκου αναφοράς.

΄Ασκηση 2 | 16

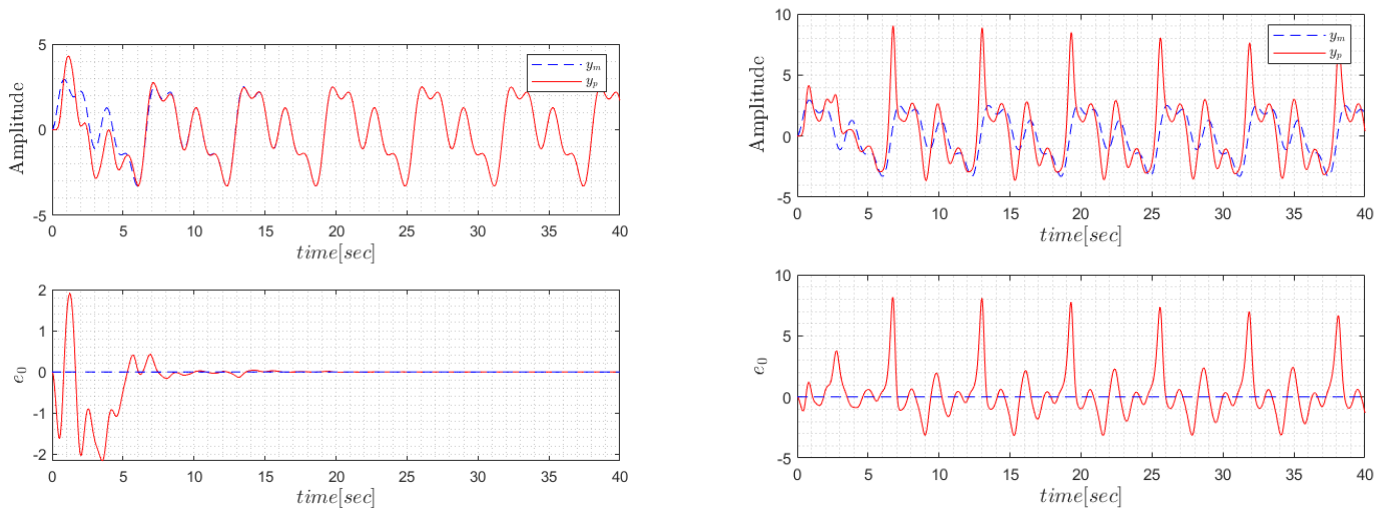
[picture p153: figure]

(αʹ) Απόκριση εξόδου συστήματος και σφάλ-

μα παρακολούθησης με παράμετρο συστήματος b = 1.

(βʹ) Απόκριση εξόδου συστήματος και σφάλ-

μα παρακολούθησης με παράμετρο συστήματος b = 3.

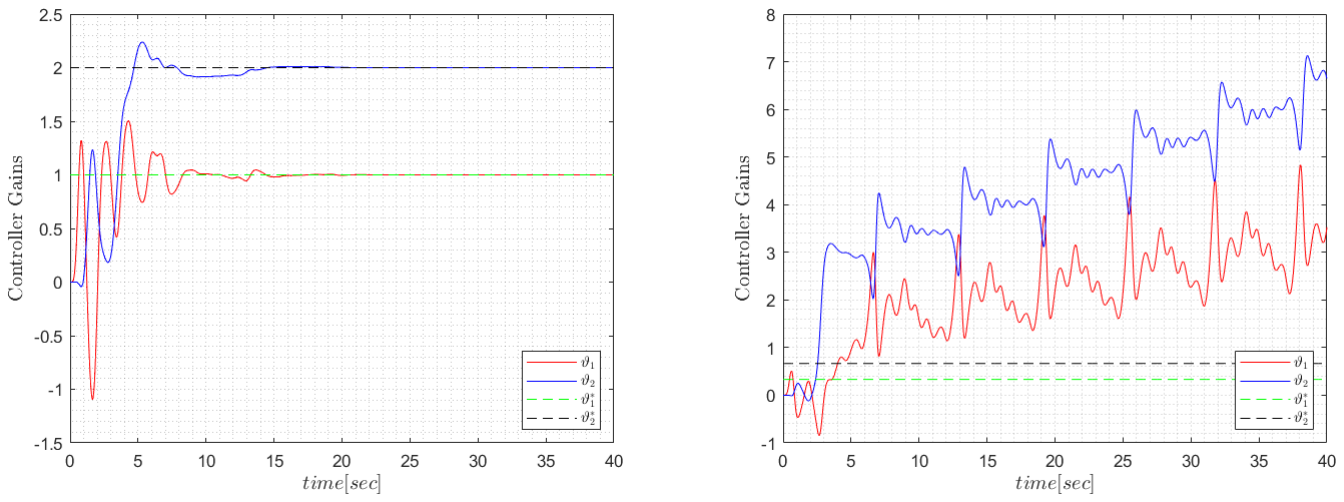
[picture p154: figure]

(γʹ) Εκτίμηση παραμέτρων ελεγκτή με πα-

ράμετρο συστήματος b = 1.

(δʹ) Εκτίμηση παραμέτρων ελεγκτή με παράμε-

τρο συστήματος b = 3.

Σχήμα 2.3: Προσομοίωση συστήματος με παραμέτρους μοντέλου αναφοράς am = 2, bm = 1

και κέρδους γ = 0.5.

Το επόμενο βήμα είναι να αυξήσουμε ξανά το κέρδος των προσαρμοστικών νόμων σε

γ = 1. Η προσομοίωση εμφανίζεται στο σχήμα 2.4. Με την αύξηση του κέρδους βλέπουμε

πως και στις δύο περιπτώσεις δεν έχουμε σύγλιση των εκτιμήσεων στις πραγματικές τιμές.

Αυτό οφείλεται στο γεγονός πως τα σήματα του συνολικού συστήματος κλειστού βρόχου

δεν είναι φραγμένα. Αυτό το διαπιστώνουμε από το σφάλμα παρακολούθησης που εκτελεί

ταλάντωση γύρω από το σημείο ισορροπίας. Παρόλο που έχουμ εισάγει στο σύστημα ένα

ικανά πλούσιο σήμα διακριτών συχνοτήτων, ο ελεγκτής δεν μπορεί να λειτουργήσει σωστά. Η

λύση σε αυτή την περίπτωση είναι να κανονικοποιηθούν όλα τα σήματα του κλειστού βρόχου,

έτσι ώστε να έχουμε και σωστή παρακολούθηση του μοντέλου αναφοράς αλλά και η εκτίμηση

των παραμέτρων να γίνεται σωστά στις πραγματικές τιμές.

΄Ασκηση 2 | 17

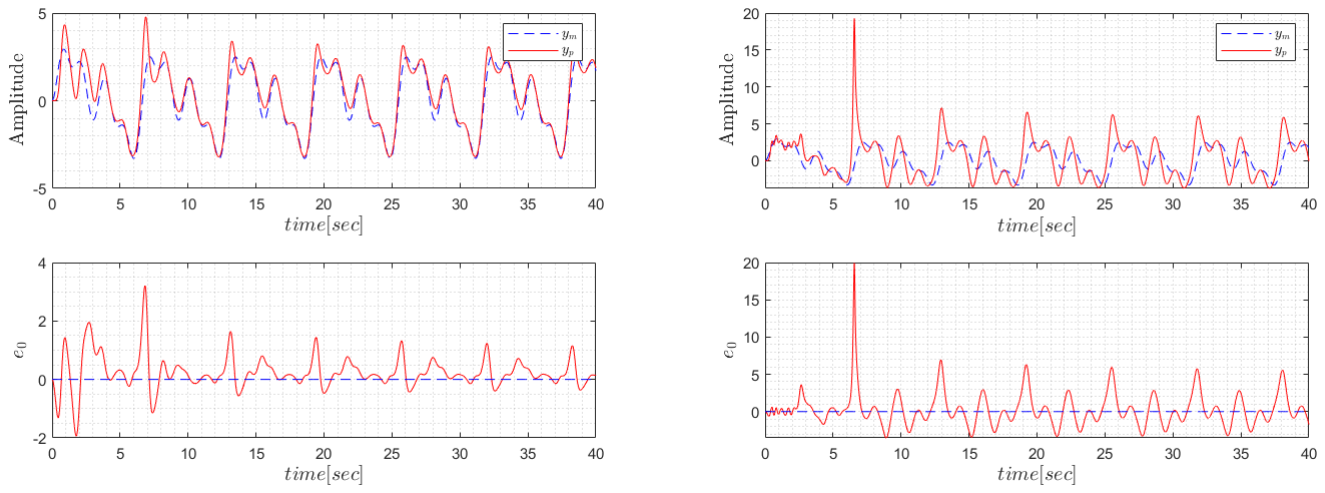
[picture p155: figure]

(αʹ) Απόκριση εξόδου συστήματος και σφάλ-

μα παρακολούθησης με παράμετρο συστήματος b = 1.

(βʹ) Απόκριση εξόδου συστήματος και σφάλ-

μα παρακολούθησης με παράμετρο συστήματος b = 3.

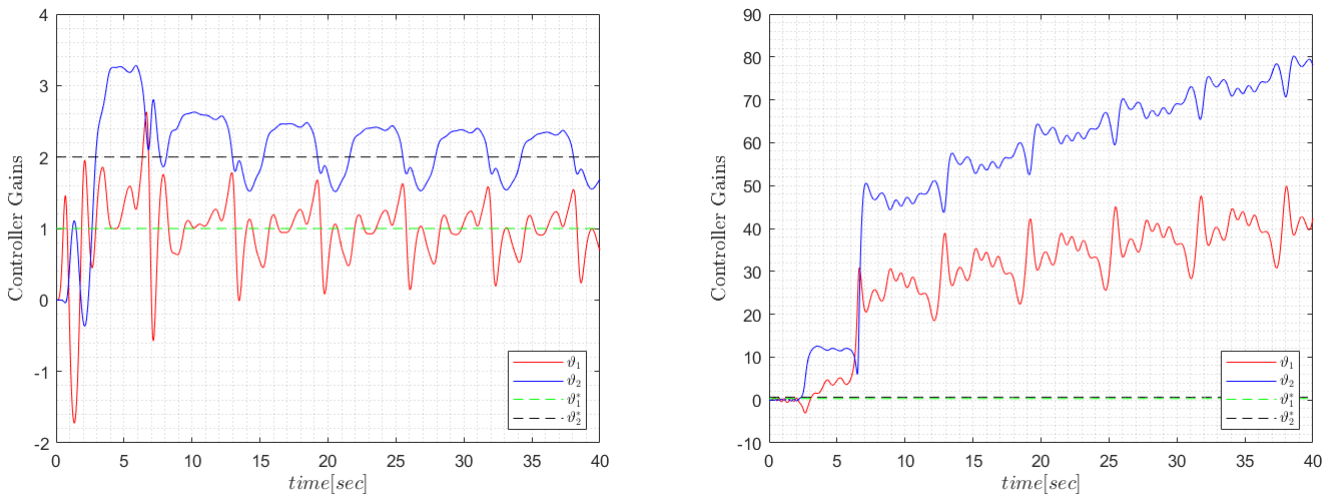
[picture p156: figure]

(γʹ) Εκτίμηση παραμέτρων ελεγκτή με πα-

ράμετρο συστήματος b = 1.

(δʹ) Εκτίμηση παραμέτρων ελεγκτή με παράμε-

τρο συστήματος b = 3.

Σχήμα 2.4: Προσομοίωση συστήματος με παραμέτρους μοντέλου αναφοράς am = 2, bm = 1

και κέρδους γ = 1.0.

Το επόμενο βήμα είναι να τροποποιηθούν οι παράμετροι του μοντέλου αναφοράς. Για δια-

φορετικό μοντέλο θα έχουμε και τα αντίστοιχα φίλτρα στους προσαρμοστικούς νόμους. Με

την επιλογή των παραμέτρων ως am = 5 και bm = 12, διαπιστώνουμε πως ο ελεγκτής λειτουρ-

γεί πιο ομαλά και έχουμε στις περισσότερες περιπτώσεις καλύτερα αποτελέσματα. ΄Ετσι, και

πάλι με τις τιμές του πραγματικού μοντέλου ως b = 1 και b = 3, προσομοιώθηκε το σύστημα

με μία βηματική είσοδο, με μία ημιτονοειδή και μία ημιτονοειδή διακριτών και διαφορετικών

συχνοτήτων. Ως πρώτη επιλογή για το κέρδος των προσαρμοστικών νόμων είναι το γ = 0.2.

Στο σχήμα 2.5 παρατηρούμε τα αποτελέλσματα της προσομοίωσης. Και στις δύο περιπτώσεις

παρατηρούμε πως έχουμε στην ουσία ασυμπτωτική σύγκλιση του σφάλματος παρακολούθη-

σης στο μηδέν. Λόγω της επιλογής των παραμέτρων των φίλτων έχουμε καλή εκτίμηση των

παραμέτρων του συστήματος. Επίσης ισχύει και η συνθήκη P E όπου μας εγγυάται ασυμπτω-

τική σύγκλιση. Τέλος, παρατηρούμε πως κατά την απόκριση του συστήματος υπάρχουν λίγες

ταλαντώσεις.

΄Ασκηση 2 | 18

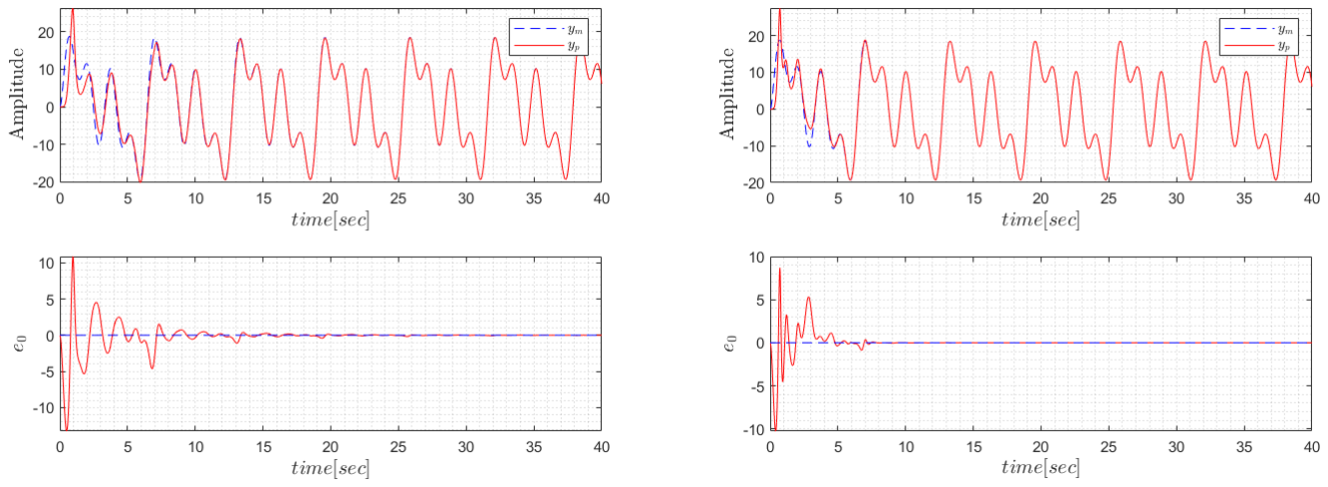
[picture p157: figure]

(αʹ) Απόκριση εξόδου συστήματος και σφάλ-

μα παρακολούθησης με παράμετρο συστήματος b = 1.

(βʹ) Απόκριση εξόδου συστήματος και σφάλ-

μα παρακολούθησης με παράμετρο συστήματος b = 3.

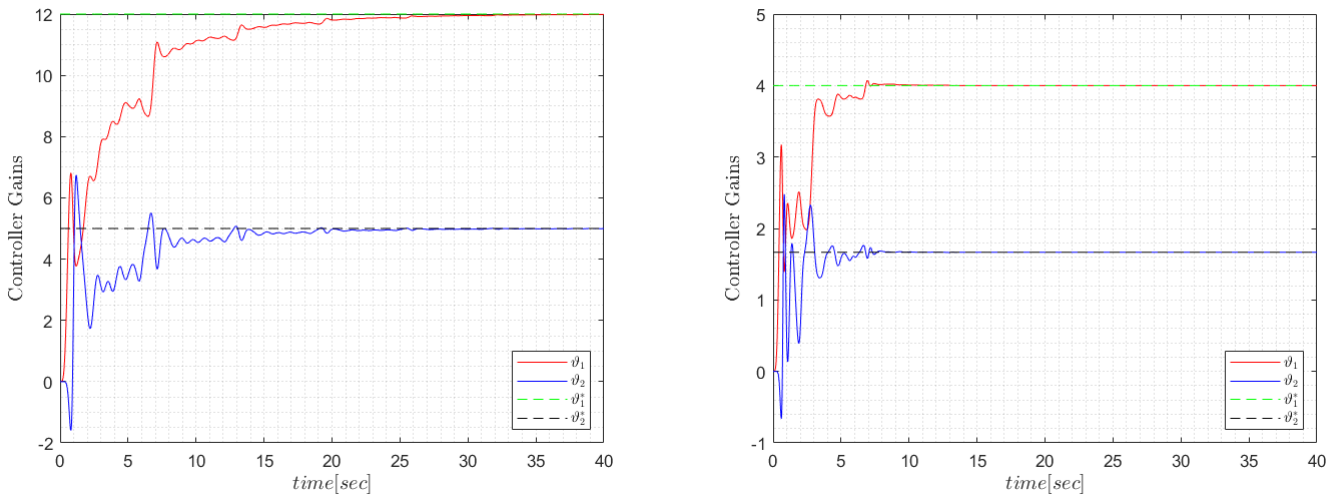
[picture p158: figure]

(γʹ) Εκτίμηση παραμέτρων ελεγκτή με πα-

ράμετρο συστήματος b = 1.

(δʹ) Εκτίμηση παραμέτρων ελεγκτή με παράμε-

τρο συστήματος b = 3.

Σχήμα 2.5: Προσομοίωση συστήματος με παραμέτρους μοντέλου αναφοράς am = 5, bm = 12

και κέρδους γ = 0.2.

Τώρα, θα αυξήσουμε λίγο την τιμή του κέρδους γ από 0.2 σε 0.5 για να δούμε τις ε-

πιπτώσεις πάνω στο σύστημα. Στο σχήμα 2.6 παρατηρούμε την εκτίμηση των παραμέτρων

και την απόκριση του συστήματος. Η απόκριση και στις δύο περιπτώσεις έχει βελτιωθεί με

το σφάλμα παρακολούθησης να συγλίνει γρηγορότερα στο μηδέν. Επίσης, έχουν μειωθεί οι

ταλαντώσεις στο σύστημα, με τα φίλτρα να κόπτουν τις υψηλές συχνότητες. Τέλος, βλέπουμε

πως οι εκτιμήσεις των παραμέτρων συγκλίνουν ασυμπτωτικά στις πραγματικές τιμές.

΄Ασκηση 2 | 19

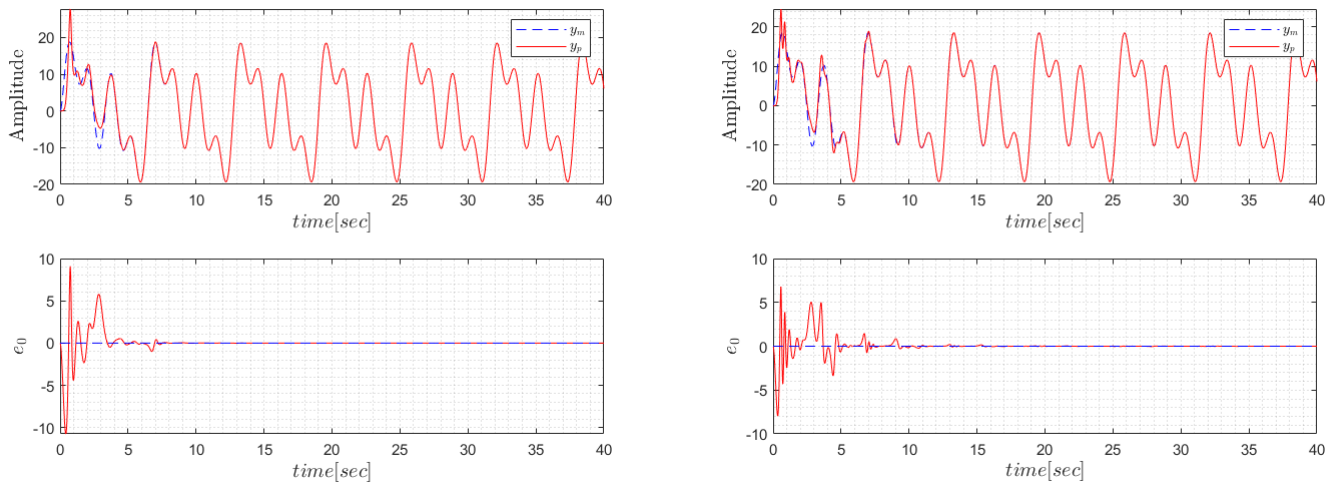
[picture p159: figure]

(αʹ) Απόκριση εξόδου συστήματος και σφάλ-

μα παρακολούθησης με παράμετρο συστήματος b = 1.

(βʹ) Απόκριση εξόδου συστήματος και σφάλ-

μα παρακολούθησης με παράμετρο συστήματος b = 3.

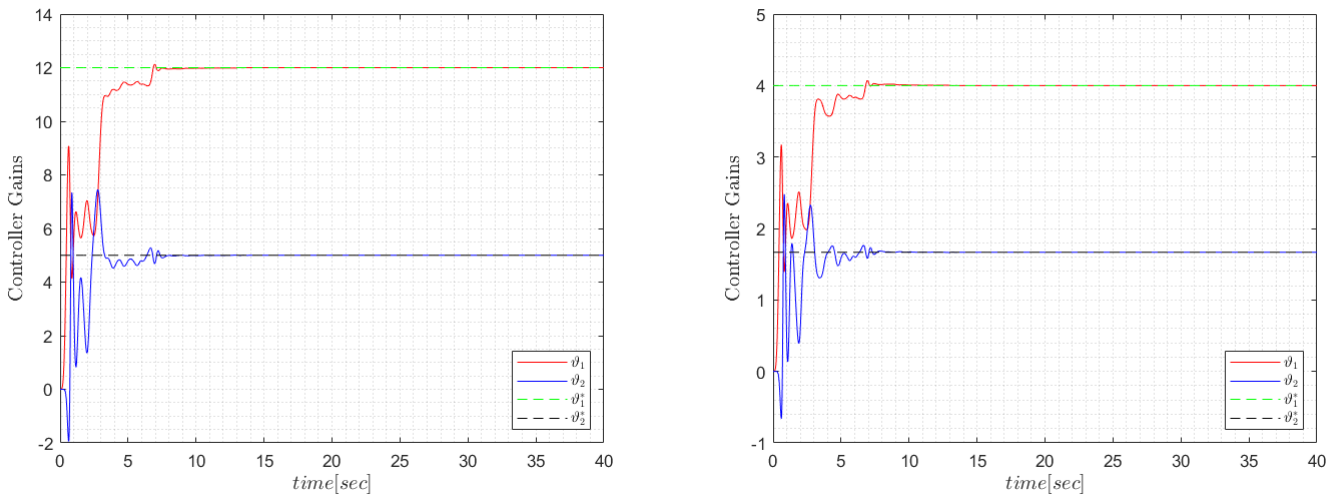
[picture p160: figure]

(γʹ) Εκτίμηση παραμέτρων ελεγκτή με πα-

ράμετρο συστήματος b = 1.

(δʹ) Εκτίμηση παραμέτρων ελεγκτή με παράμε-

τρο συστήματος b = 3.

Σχήμα 2.6: Προσομοίωση συστήματος με παραμέτρους μοντέλου αναφοράς am = 5, bm = 12

και κέρδους γ = 0.5.

Τέλος, θα κάνουμε ακόμα μια αύξηση στο κέρδος γ από το 0.5 στο 1 για να δούμε πως

θα ανταποκριθεί το σύστημα (βλ. σχήμα 2.7). Στην πρώτη περίπτωση διαπιστώνουμε πως

το πραγματικό σύστημα συγκλίνει στο σύστημα αναφοράς γρήγορα, με την εκτίμηση των

παραμέτρων να συγκλίνουν στις πραγματικές. Παρόλο που αυξήθηκε η τιμή του κέρδους, δεν

επιρεάστηκε η λειτουργία του φίλτρου κατά την προσαρμογή των παραμέτρων. Αντιθέτως,

στην δεύτερη περίπτωση παρατηρούμε παροδικές ταλαντώσεις στην απόκριση της εξόδου και

του σφάλματος παρακολούθησης. Επιπλέον, παρατηρούμε πως οι εκτιμήσεις των παραμέτρων

συγλίνουν κοντά σε μια περιοχή των πραγματικών τιμών. Ωστόσο, έχουμε περιοδικές εκρήξεις

των εκτιμίσεων (ειδικά της παραμέτρου ϑ2). Γνωρίζουμε πως η είσοδος είναι ικανά πλούσια

έτσι ώστε να ισχύει η συθήκη P E. Ωστόσο, το πρόβλημα εμφανίζεται στην απόκριση των

φίλτρων κατά την ανανέωση των παραμέτρων. Καθώς τα φίλτρα δεν μπορούν αποκόψουν

όλες τις υψηλές συχνότητες, λόγω της παραμέτρου ανανέωσης, το σύστημα έχει την απόκριση

αυτή. Η λύση σε αυτή την περίπτωση είναι να κανονικοποιηθούν τα σήματα έτσι ώστε να

έχουμε καλύτερα αποτελέσματα και οι εκτιμήσεις να συγκλίνουν πιο ομαλά στις επιθυμητές

τιμές.

΄Ασκηση 2 | 20

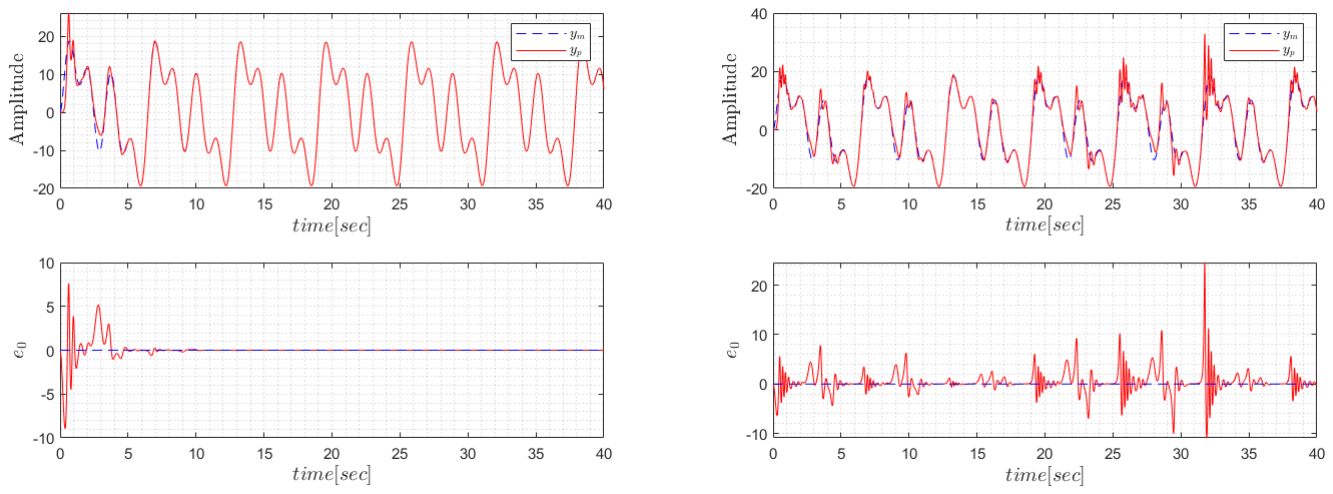
[picture p161: figure]

(αʹ) Απόκριση εξόδου συστήματος και σφάλ-

μα παρακολούθησης με παράμετρο συστήματος b = 1.

(βʹ) Απόκριση εξόδου συστήματος και σφάλ-

μα παρακολούθησης με παράμετρο συστήματος b = 3.

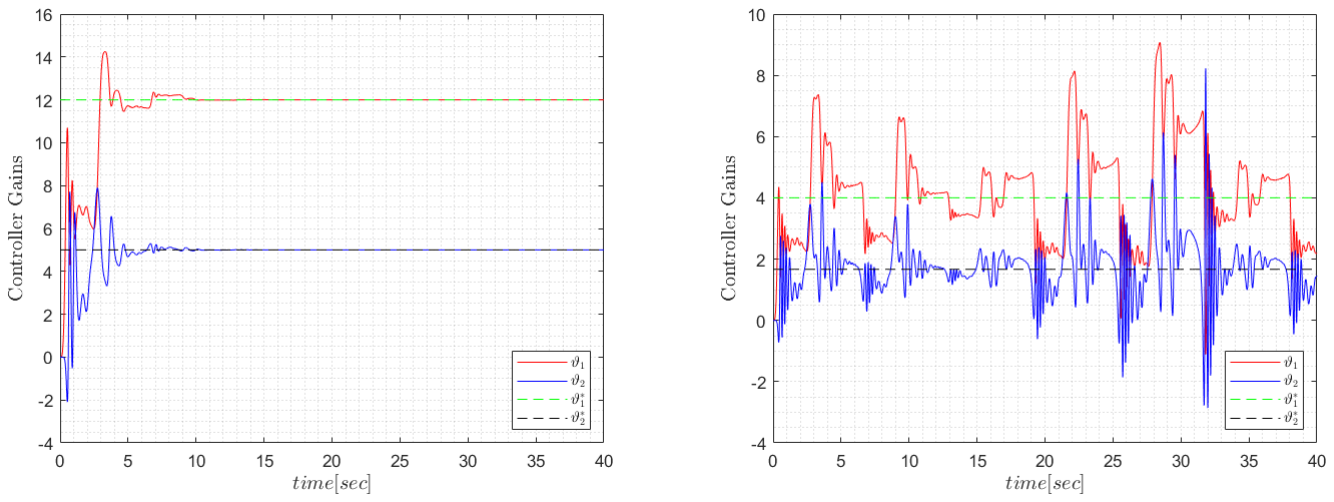
[picture p162: figure]

(γʹ) Εκτίμηση παραμέτρων ελεγκτή με πα-

ράμετρο συστήματος b = 1.

(δʹ) Εκτίμηση παραμέτρων ελεγκτή με παράμε-

τρο συστήματος b = 3.

Σχήμα 2.7: Προσομοίωση συστήματος με παραμέτρους μοντέλου αναφοράς am = 5, bm = 12

και κέρδους γ = 1.0.

Το πρόβλημα της σύγκλισης των παραμέτρων πηγάζει από την ίδια την ευστάθεια του

συστήματος. Καθώς οι προσαρμοστικοί νόμοι εγγυούνται μόνο ευστάθεια στο σύστημα και

όχι ασυμπτωτική. Τότε η μόνη λύση είναι να κανονικοποιήσουμε τα σήματα του συστήματος.

΄Ετσι, θα έχουμε μια πιο ισχυρή συνθήκη P E. Επιπλέον, η αύξηση του κέρδους γ θα είχε

αρνητικές επιπτώσεις στο σύστημα, καθώς οι παράμετροι του συστήματος θα έχουνε μεγάλες

τιμές και η λύση του συστήματος θα εκτοξευθεί ακαριαία. Συνεπώς, για να μπορεί να αξιοποι-

ηθεί η συγκεκριμένη μέθοδος ελέγχου και να έχουμε και σύγκλιση των εκτιμήσεων, πλην του

σφάλματος παρακολούθησης στο μηδέν, χρειαζόμαστε την εφαρμογή της κανονικοποίησης.

΄Ετσι, θα τροποποιηθούν οι προσαρμοστικοί νόμοι ελέγχου και θα προκύψουν ποιοτικότερα

αποτελέσματα.

# Παράρτημα Αʹ

# Κώδικας Προσομοίωσης

Στο παράρτημα Α παρουσιάζονται οι κώδικες προσομοίωσης που χρησιμοποιήθηκαν για τις

ασκήσεις.

## Αʹ.1 Κώδικας Πρώτης ΄Ασκησης

### %% MIT Rule S im ul a t i o n

% | Ass ignmen t 2
% | E x e r c i s e 1
% | Name : | George Krommydas
% | A.M. : | 02121208

c lear ;
c l c ;

### % Parameter s e t t i n g

### g loba l a

### g loba l w

### g loba l z e t a

### g loba l r

### g loba l gamma

a = 4 ;
w = 1 0; | % rad / s e c

z e t a = 1 ;
t sp an = [ 0 5 0 ] ;

n = 1 3;
x0 = zeros ( n , 1 ) ;

gamma = 1 ;

### %% S im ul a t i o n

| 21

Κώδικας Προσομοίωσης | 22

[ t , x ] = ode45( @MITClosedLoop , tspan , x0 ) ;

### %% P l o t s

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

f igure ( 1 ) ;

c l f ;
subplot ( 2 , 1 , 1 ) ;
p lot ( t , x ( : , 1 ) , ’ b−−’ ) ;

### hold on

p lot ( t , x ( : , 3 ) , ’ r−’ ) ;

y labe l ( ” Amplitude ” , ” I n t e r p r e t e r ” , ” l a t e x ” , ” F on tSize ” , 1 2 ) ;
x labe l ( ” $time [ sec ] $ ” , ” I n t e r p r e t e r ” , ” l a t e x ” , ” F on tSize ” , 1 2 ) ;

grid minor ;
legend( ” $y m$ ” , ” $y p$ ” , ” L o c a ti o n ” , ” n o r t h e a s t ” , ” I n t e r p r e t e r ” , ” l a t e x ” ) ;

subplot ( 2 , 1 , 2 ) ;
p lot ( t , x ( : , 3 ) − x ( : , 1 ) , ” r −”);

### hold on

p lot ( t , zeros ( s i z e ( t ) ) , ”b−−”);
x labe l ( ” $time [ sec ] $ ” , ” I n t e r p r e t e r ” , ” l a t e x ” , ” F on tSize ” , 1 2 ) ;

grid minor ;
y labe l ( ” $e 0$ ” , ” I n t e r p r e t e r ” , ” l a t e x ” , ” F on tSize ” , 1 2 ) ;

f igure ( 2 ) ;

c l f ;
p lot ( t , x ( : , 5 ) , ” r −”);

### hold on

p lot ( t , x ( : , 6 ) , ”b−”);
p lot ( t , x ( : , 7 ) , ”g −”);

p lot ( t , t h e t a 1 d e si r e d , ” C ol o r ” , [ 0 . 3 0 1 0 0. 7 4 5 0 0 . 9 3 3 0 ] , ” Li n e S t yl e ”,”− −”);

p lot ( t , t h e t a 2 d e si r e d , ” C ol o r ” , [ 0 0. 4 4 7 0 0 . 7 4 1 0 ] ,
” Li n e S t yl e ”,”− −”);

p lot ( t , t h e t a 3 d e si r e d , ” C ol o r ” , [ 0 . 6 3 5 0 0. 0 7 8 0 0 . 1 8 4 0 ] ,
” Li n e S t yl e ”,”− −”);
x labe l ( ” $time [ sec ] $ ” , ” I n t e r p r e t e r ” , ” l a t e x ” , ” F on tSize ” , 1 2 ) ;

Κώδικας Προσομοίωσης | 23

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

### %% Pl an t and Model Dynamics

### function dx = MITClosedLoop ( t , x )

### % Pl an t Dynamics

### g loba l a

### g loba l w

### g loba l z e t a

### g loba l r

### g loba l gamma

M = 4 ;
r = M∗ s in ( t )+M∗ s in ( 4∗ t )+M∗ s in ( 2∗ t ) ;

% r = 1 ;
% r = s i n ( t ) ;
dx = [ x ( 2 ) ;
−w. ˆ 2 ∗ x ( 1 ) − 2∗ z e t a ∗w∗x ( 2 ) + w. ˆ 2 . ∗ r ;

x ( 4 ) ;
−x ( 6 ) ∗ x ( 3 ) − ( a + x ( 7 ) ) ∗ x ( 4 ) + x ( 5 ) . ∗ r ; −gamma∗x ( 8 ) ∗ ( x ( 3 ) − x ( 1 ) ) ;
gamma∗x ( 1 0 ) ∗ ( x ( 3 ) − x ( 1 ) ) ;
gamma∗x ( 1 2 ) ∗ ( x ( 3 ) − x ( 1 ) ) ;

x ( 9 ) ;
−wˆ2∗x ( 8 ) − 2∗ z e t a ∗w∗x ( 9 ) + w. ˆ 2 . ∗ r ;

x ( 1 1 ) ;
−wˆ2∗x ( 1 0 ) − 2∗ z e t a ∗w∗x ( 1 1 ) + w. ˆ 2 . ∗ x ( 3 ) ;

x ( 1 3 ) ;
−wˆ2∗x ( 1 2 ) − 2∗ z e t a ∗w∗x ( 1 3 ) + w. ˆ 2 . ∗ x ( 4 ) ] ;

### end

## Αʹ.2 Κώδικας Προσομοίωσης Δεύτερης ΄Ασκησης

### %% MIT Rule Sim ul a ti o n

% | Assignment 2
% | E x e r ci s e 2
% | Name: | George Krommydas

Κώδικας Προσομοίωσης | 24
% | A.M. : | 02121208

c l e a r ;
c l c ;

### % Parameter s e t t i n g

### g l o b a l am

### g l o b a l bm

### g l o b a l b

### g l o b a l r

### g l o b a l gamma

am = 5 ;
bm = 1 2;
b = 3 ;
t sp an = [ 0 4 0 ] ;

n = 6 ;
x0 = z e r o s ( n , 1 ) ;

gamma = 0 . 5 ;

### %% Sim ul a ti o n

[ t , x ] = ode45 ( @MITClosedLoop , tspan , x0 ) ;

### %% Pl o t s

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

f i g u r e ( 1 ) ;

c l f ;
s u b pl o t ( 2 , 1 , 1 ) ;
pl o t ( t , x ( : , 1 ) , ’ b−−’);

### h old on

pl o t ( t , x ( : , 2 ) , ’ r − ’ );

y l a b e l ( ” Amplitude ” , ” I n t e r p r e t e r ” , ” l a t e x ” , ” F on tSize ” , 1 2 ) ;
x l a b e l ( ” $time [ s e c ] $ ” , ” I n t e r p r e t e r ” , ” l a t e x ” , ” F on tSize ” , 1 2 ) ;

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

s u b pl o t ( 2 , 1 , 2 ) ;
pl o t ( t , x ( : , 2 ) − x ( : , 1 ) , ” r −”);

Κώδικας Προσομοίωσης | 25

### h old on

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

g ri d minor ;
y l a b e l ( ” $e 0$ ” , ” I n t e r p r e t e r ” , ” l a t e x ” , ” F on tSize ” , 1 2 ) ;

f i g u r e ( 2 ) ;

c l f ;
pl o t ( t , x ( : , 3 ) , ” r −”);

### h old on

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

### %% Plan t and Model Dynamics

### f u n c ti o n dx = MITClosedLoop ( t , x )

### % Pl an t Dynamics

### g l o b a l am

### g l o b a l bm

### g l o b a l b

### g l o b a l r

### g l o b a l gamma

M = 4 ;
r = M∗ s i n ( t )+M∗ s i n ( 4∗ t )+M∗ s i n ( 2∗ t ) ;

% r = 1 ;
% r = s i n ( t ) ;
dx = [−am∗x ( 1 ) + bm∗ r ;
−b∗x ( 4 ) ∗ x ( 2 ) + b∗x ( 3 ) ∗ r ; −gamma∗x ( 5 ) ∗ ( x ( 2 ) − x ( 1 ) ) ; gamma∗x ( 6 ) ∗ ( x ( 2 ) − x ( 1 ) ) ; −am∗x ( 5 ) + am∗ r ;
−am∗x ( 6 ) + am∗x ( 2 ) ] ;

### end

# Βιβλιογραφία

### [1] Iliya V. Miroshnik Alexander L. Fradkov and Vladimir O. Nikiforov. Nonlinear and

### Adaptive Control of Complex Systems. Springer, 1999. isbn: 978-94-015-9261-1. doi:

### 10.1007/978-94-015-9261-1. (https://doi.org/10.1007/978-94-015-9261-1)

[2] A. Astolfi and L. Marconi. Analysis and Design of Nonlinear Control Systems.

Springer Berlin Heidelberg New York, 2008. isbn: 978-3-540-74357-6.

[3] Charalampos Bechlioulis. Simulation of Dynamical Systems. 2021.

### [4] Jay A. Farrell and Marios M. Polycarpou. Adaptive Approximation Based Control:

### Unifying Neural, Fuzzy and Traditional Adaptive Approximation Approaches. John

### Wiley Sons, Inc., 2006. isbn: 978-0-471-72788-0. doi: 10.1007/978-0-471-72788-

### 0. (https://doi.org/10.1007/978-0-471-72788-0)

### [5] Mohammed M’Saad Alireza Karimi Ioan Dor´e Landau Rogelio Lozano. Adaptive

Control: Algorithms, Analysis and Applications. Second Edition. Springer, 2011.

isbn: 978-0-85729-664-1. doi: 10.1007/978-0-85729-664-1. (https://doi.org/10.1007/978-0-85729-664-1)

[6] Petros A. Ioannou and Jing Sun. Robust Adaptive Control. Dover Publications, 2012.

isbn: 978-0486498171.

### [7] Alberto Isidori. Nonlinear Control Systems. 3rd Edition. Springer, 1995. isbn: 978-

1-84628-615-5. doi: 10.1007/978-1-84628-615-5. (https://doi.org/10.1007/978-1-84628-615-5)

[8] Hassan K. Khalil. Nonlinear Systems. 3rd Edition. Pearson, 2001. isbn: 978-0130673893.

### [9] Craig A. Kluever. Dynamic Systems: Modeling, Simulation, and Control. John Wiley

Sons, Inc., 2015. isbn: 978-1-118-28945-7. doi: 10.1007/978-1-118-28945-7. (https://doi.org/10.1007/978-1-118-28945-7)

[10] Jinkun Liu. Intelligent Control Design and MATLAB Simulation. Springer, 2018.

isbn: 978-981-10-5263-7. doi: https://doi.org/10.1007/978-981-10-5263-7. (https://doi.org/https://doi.org/10.1007/978-981-10-5263-7)

[11] Norm S. Nise. Control Systems Engineering. 8th Edition. John Wiley Sons, 2019.

isbn: 978-1119590132.

### [12] P.Ioannou and B. Fidan. Adaptive Control Tutorial. SIAM, 2006. isbn: 978-0-89871-

### 615-3. doi: 10.1007/978-0-89871-615-3. (https://doi.org/10.1007/978-0-89871-615-3)

### [13] V.P. Singh Rajesh Kumar and Akhilesh Mathur. Intelligent Algorithms for Analysis

### and Control of Dynamical Systems. Springer, 2021. isbn: 978-981-15-8045-1. doi:

### 10.1007/978-981-15-8045-1. (https://doi.org/10.1007/978-981-15-8045-1)

[14] Jean-Jacques E. Slotine and Weiping Li. Applied Nonlinear Control. Prentice Hall,

1991. isbn: 0-13-040890-5.

26

ΒΙΒΛΙΟΓΡΑΦ΄ΙΑ | 27
[15] Spyros G. Tzafestas. Methods and Applications of Intelligent Control. Springer, 1997.

isbn: 978-94-011-5498-7. doi: 10.1007/978-94-011-5498-7. (https://doi.org/10.1007/978-94-011-5498-7)
