GeoKrom/NTUA-Intelligent-Control-Systems-and-Robotic-Systems-course/Atomic Project/Images/background.jpg

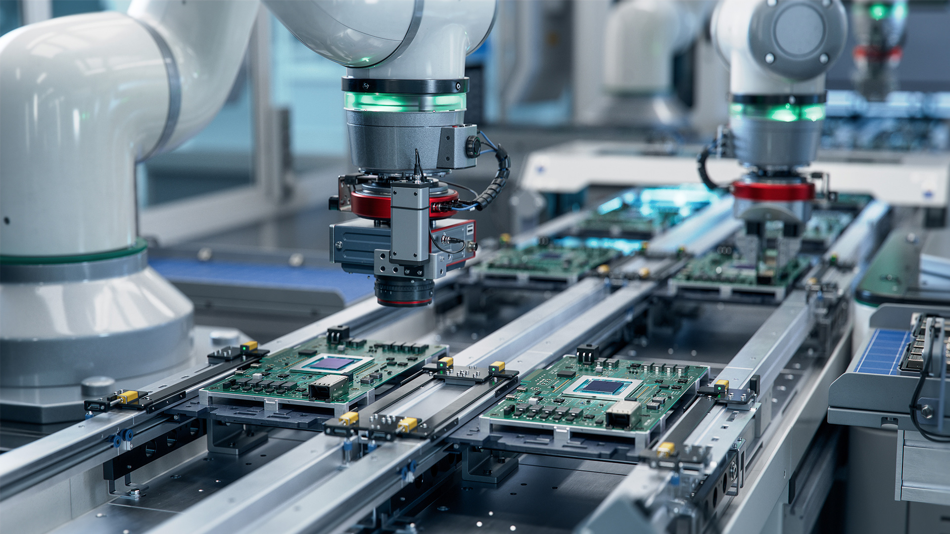
Atomic Project/Images/background.jpg
