GeoKrom/NTUA-Intelligent-Control-Systems-and-Robotic-Systems-course/Atomic Project/Images/General_Feedback_System.png

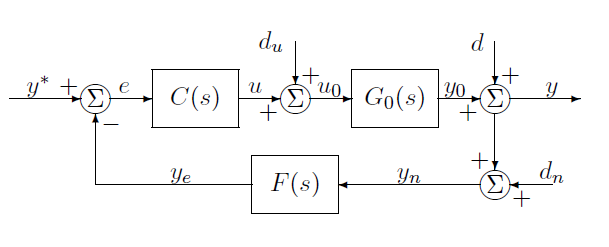
Atomic Project/Images/General_Feedback_System.png
