GeoKrom/NTUA-Intelligent-Control-Systems-and-Robotic-Systems-course/Exercises/Exercise-1/Simulations/satellite.png

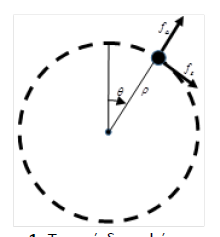
Exercises/Exercise-1/Simulations/satellite.png
