GeoKrom/NTUA-Intelligent-Control-Systems-and-Robotic-Systems-course/Exercises/Exercise-1/Simulations/Simulation_1_nonlinear.png

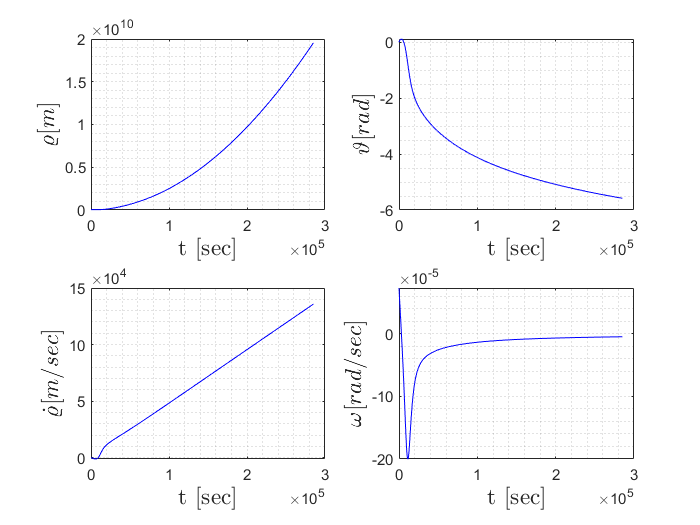
Exercises/Exercise-1/Simulations/Simulation_1_nonlinear.png
