GeoKrom/NTUA-Intelligent-Control-Systems-and-Robotic-Systems-course/Exercises/Exercise-1/Simulations/stability analysis.png

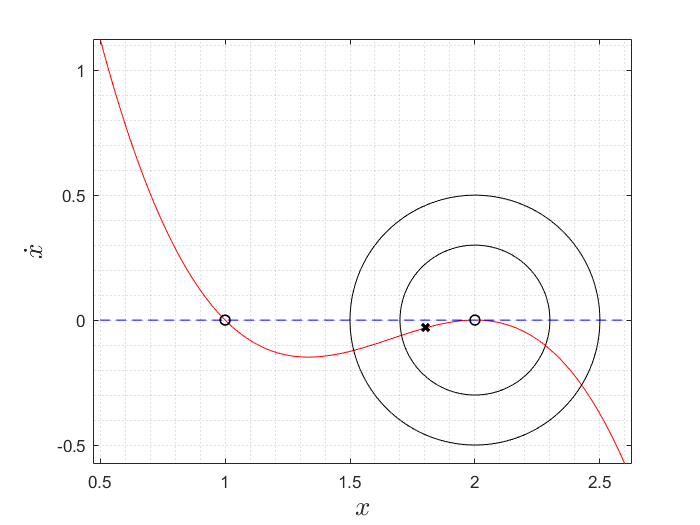
Exercises/Exercise-1/Simulations/stability analysis.png
