GeoKrom/NTUA-Intelligent-Control-Systems-and-Robotic-Systems-course/Exercises/Exercise-2/Simulations/Ex1/a 4/Sim_Ex1_g02_a4_zeta1_w1_gain.png

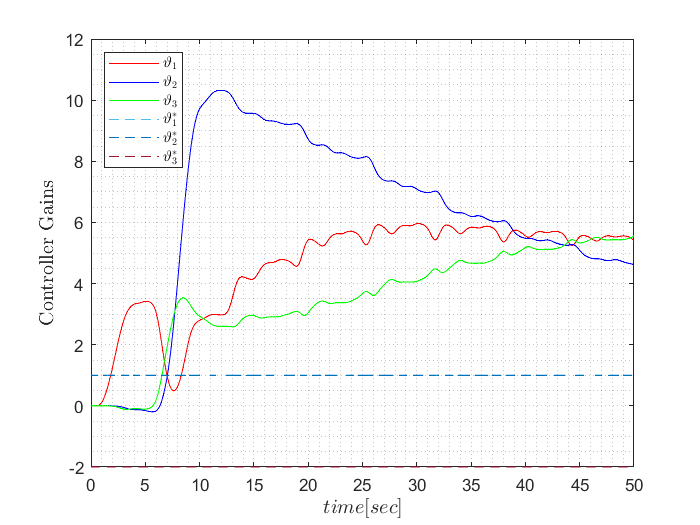
Exercises/Exercise-2/Simulations/Ex1/a 4/Sim_Ex1_g02_a4_zeta1_w1_gain.png
