GeoKrom/NTUA-Intelligent-Control-Systems-and-Robotic-Systems-course/Exercises/Exercise-2/Simulations/Ex1/a -5/Sim_Ex1_g1_a4_zeta0707_w1_gain_sine.png

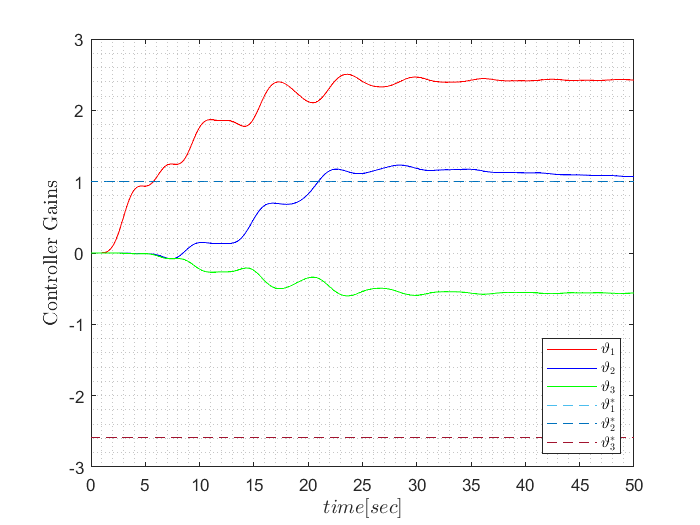
Exercises/Exercise-2/Simulations/Ex1/a -5/Sim_Ex1_g1_a4_zeta0707_w1_gain_sine.png
