GeoKrom/NTUA-Intelligent-Control-Systems-and-Robotic-Systems-course/Exercises/Exercise-2/Simulations/Ex1/a -5/Sim_Ex1_g1_amin5_zeta1_w10_out.png

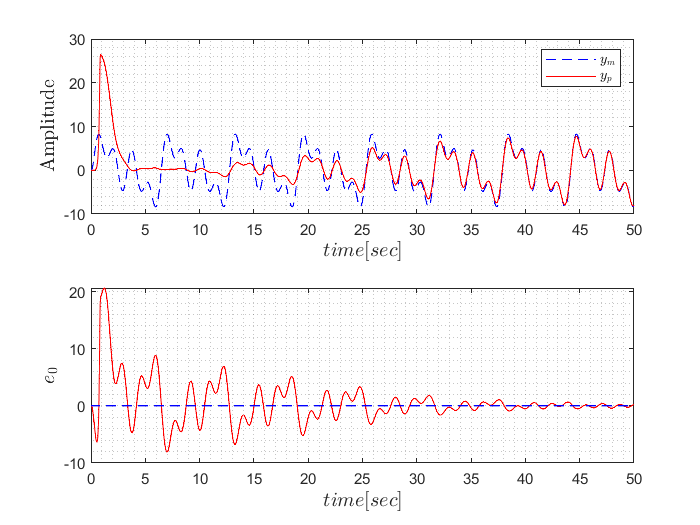
Exercises/Exercise-2/Simulations/Ex1/a -5/Sim_Ex1_g1_amin5_zeta1_w10_out.png
