GeoKrom/NTUA-Intelligent-Control-Systems-and-Robotic-Systems-course/Exercises/Exercise-2/Simulations/Ex1/a -5/Sim_Ex1_g02_amin5_zeta1_w1_out.png

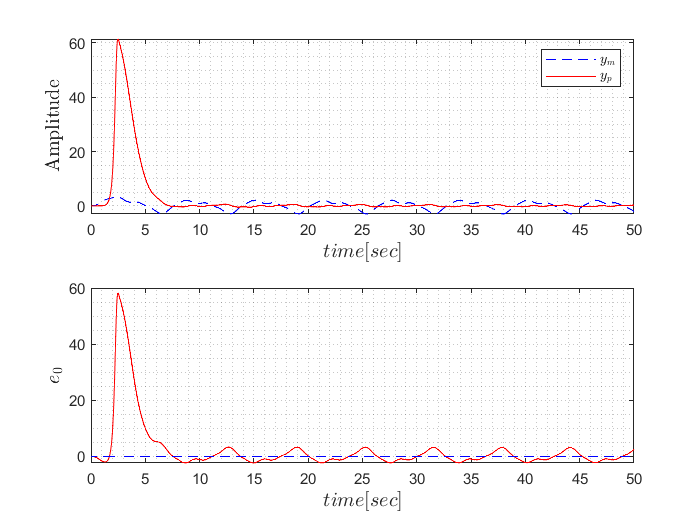
Exercises/Exercise-2/Simulations/Ex1/a -5/Sim_Ex1_g02_amin5_zeta1_w1_out.png
