GeoKrom/NTUA-Intelligent-Control-Systems-and-Robotic-Systems-course/Exercises/Exercise-2/Simulations/Ex2/b1/Sim_g_02_r_3sine_b1_am2_bm1_output_error.png

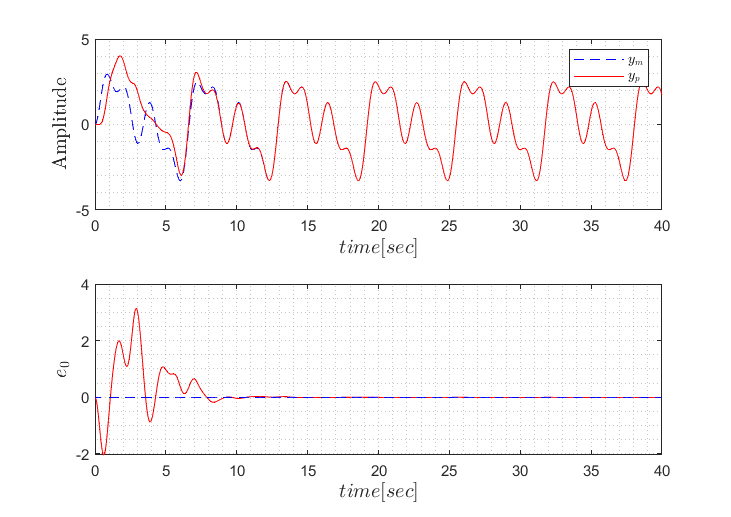
Exercises/Exercise-2/Simulations/Ex2/b1/Sim_g_02_r_3sine_b1_am2_bm1_output_error.png
