GeoKrom/NTUA-Intelligent-Control-Systems-and-Robotic-Systems-course/Exercises/Exercise-2/Simulations/Ex2/b3/Sim_g_05_r_4sine_b3_am3_bm2_output_error.png

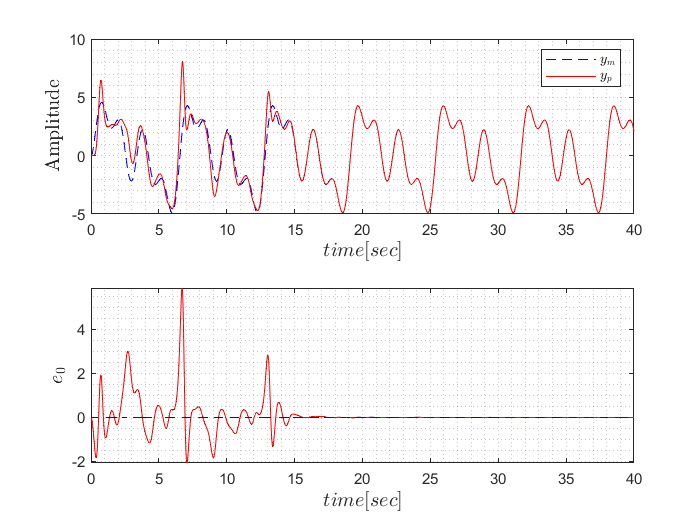
Exercises/Exercise-2/Simulations/Ex2/b3/Sim_g_05_r_4sine_b3_am3_bm2_output_error.png
