GeoKrom/NTUA-Intelligent-Control-Systems-and-Robotic-Systems-course/Exercises/Exercise-2/Simulations/Ex2/b3/Sim_g_10_r_3sine_b1_am3_bm2_gain_estimation.png

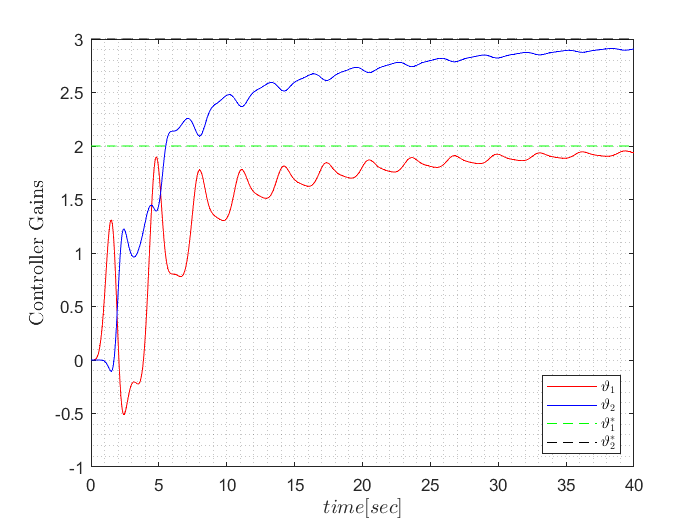
Exercises/Exercise-2/Simulations/Ex2/b3/Sim_g_10_r_3sine_b1_am3_bm2_gain_estimation.png
