GeoKrom/NTUA-Intelligent-Control-Systems-and-Robotic-Systems-course/Exercises/Exercise-2/Simulations/Ex2/b3/Sim_g_10_r_sine_b3_am2_bm1_output_error.png

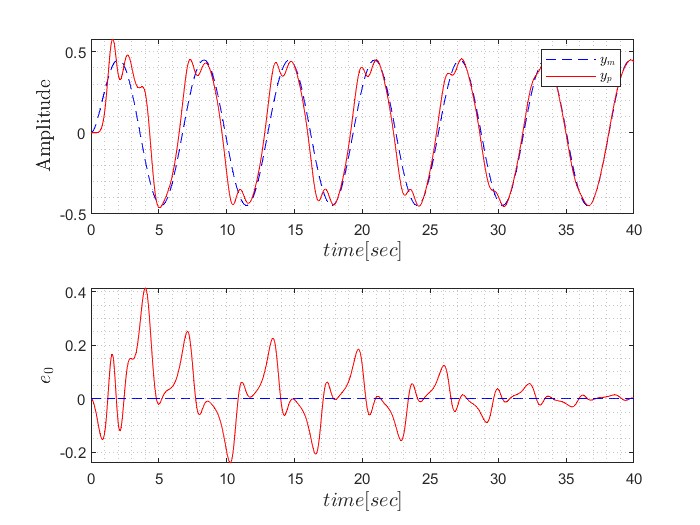
Exercises/Exercise-2/Simulations/Ex2/b3/Sim_g_10_r_sine_b3_am2_bm1_output_error.png
