GeoKrom/NTUA-Intelligent-Control-Systems-and-Robotic-Systems-course/Exercises/Exercise-3/Simulations/Neural Netwotk Approximation/MRAC_Gain_Estimation_nn_rbf.png

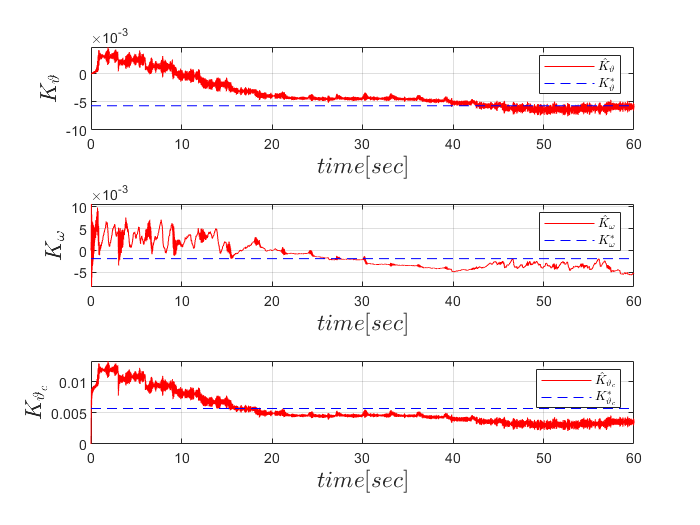
Exercises/Exercise-3/Simulations/Neural Netwotk Approximation/MRAC_Gain_Estimation_nn_rbf.png
