GeoKrom/NTUA-Intelligent-Control-Systems-and-Robotic-Systems-course/Exercises/Exercise-3/Simulations/Stepper_Motor.png

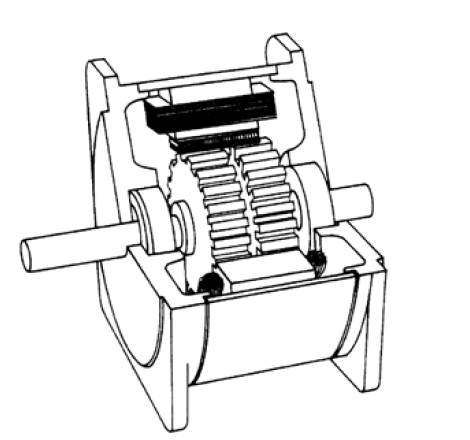
Exercises/Exercise-3/Simulations/Stepper_Motor.png
