GeoKrom/NTUA-Intelligent-Control-Systems-and-Robotic-Systems-course/Exercises/Exercise-4/Simulations/Adaptive Backstepping Control/Two_dof__Adaptive_Backstepping_Control_Parameter_Estimation_1.png

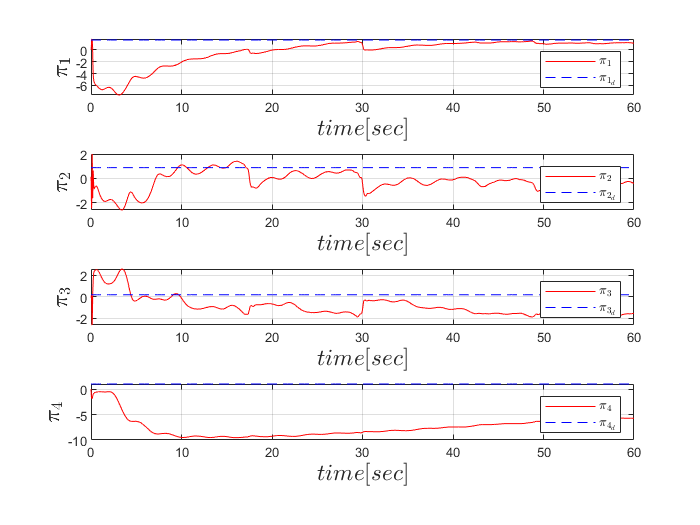
Exercises/Exercise-4/Simulations/Adaptive Backstepping Control/Two_dof__Adaptive_Backstepping_Control_Parameter_Estimation_1.png
