GeoKrom/NTUA-Intelligent-Control-Systems-and-Robotic-Systems-course/Exercises/Exercise-4/Simulations/Adaptive Backstepping Control/Two_dof_Adaptive_Backstepping_Control_Joint_q_2_pos_vel.png

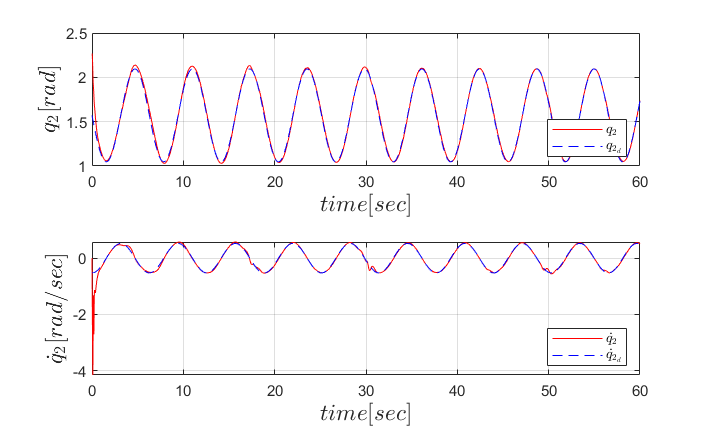
Exercises/Exercise-4/Simulations/Adaptive Backstepping Control/Two_dof_Adaptive_Backstepping_Control_Joint_q_2_pos_vel.png
