GeoKrom/NTUA-Intelligent-Control-Systems-and-Robotic-Systems-course/Team Project/Simulation/1. MIT/C++/MIT_Parameters.png

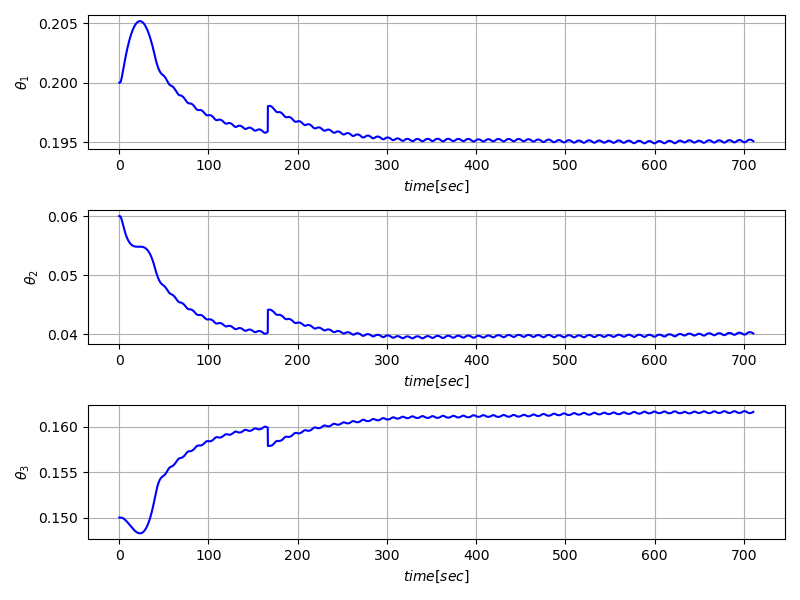
Team Project/Simulation/1. MIT/C++/MIT_Parameters.png
