GeoKrom/NTUA-Intelligent-Control-Systems-and-Robotic-Systems-course/Team Project/Simulation/1. MIT/MATLAB/Parameter_Adaptaion_Ref_Signal_3.png

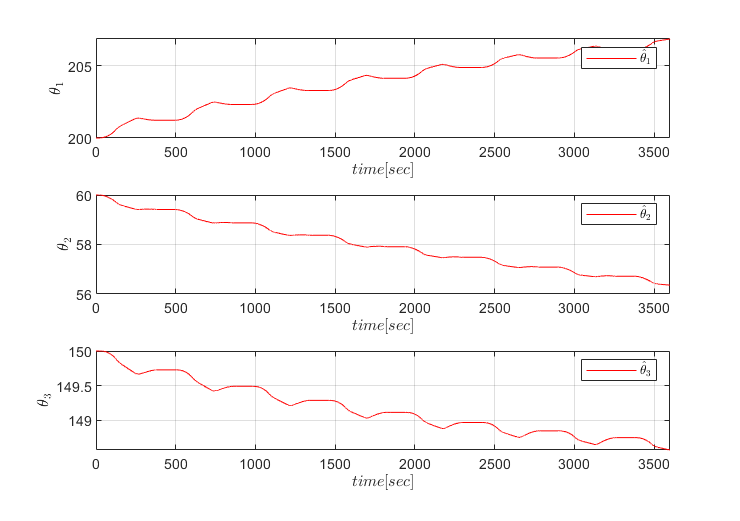
Team Project/Simulation/1. MIT/MATLAB/Parameter_Adaptaion_Ref_Signal_3.png
