GeoKrom/NTUA-Intelligent-Control-Systems-and-Robotic-Systems-course/Team Project/Simulation/1. MIT/MATLAB/System_Response_Ref_Signal_3.png

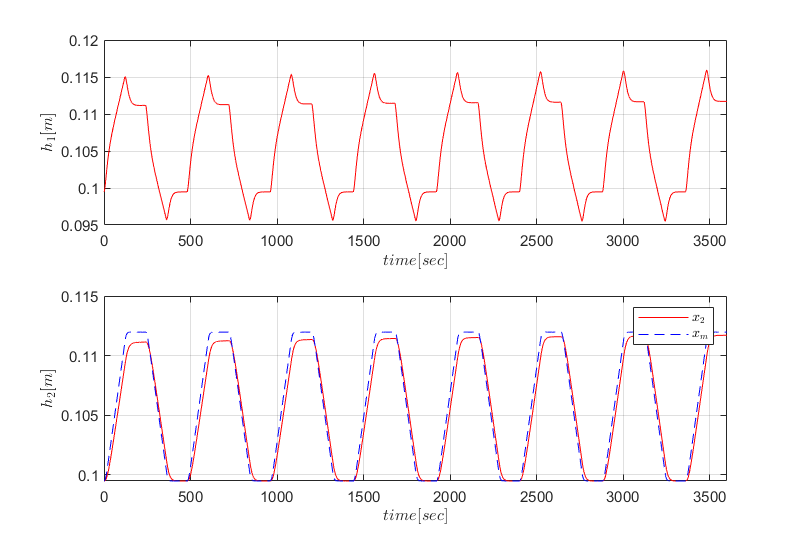
Team Project/Simulation/1. MIT/MATLAB/System_Response_Ref_Signal_3.png
