GeoKrom/NTUA-Intelligent-Control-Systems-and-Robotic-Systems-course/Team Project/Simulation/2. MRAC/MATLAB/Error_Ref_Signal_2.png

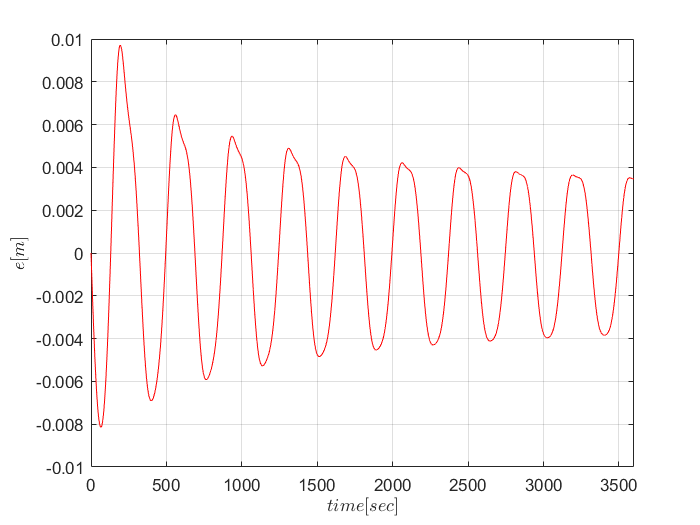
Team Project/Simulation/2. MRAC/MATLAB/Error_Ref_Signal_2.png
