GeoKrom/NTUA-Intelligent-Control-Systems-and-Robotic-Systems-course/Team Project/Simulation/2. MRAC/MATLAB/Parameter_Adaptaion_Ref_Signal_1.png

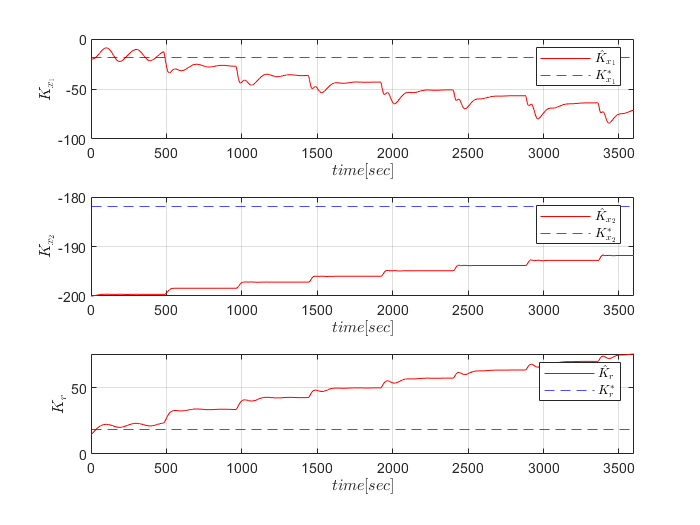
Team Project/Simulation/2. MRAC/MATLAB/Parameter_Adaptaion_Ref_Signal_1.png
