GeoKrom/NTUA-Intelligent-Control-Systems-and-Robotic-Systems-course/Team Project/Simulation/3. Feedback Linearizition/Adaptive/MATLAB/Error_Ref_Signal_1.png

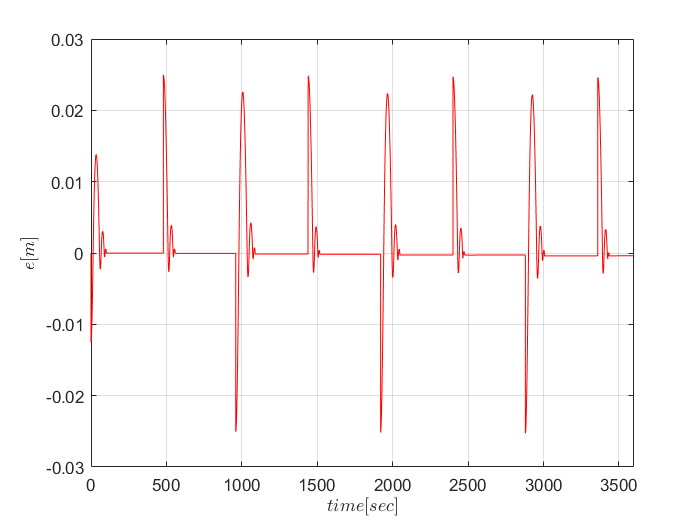
Team Project/Simulation/3. Feedback Linearizition/Adaptive/MATLAB/Error_Ref_Signal_1.png
