GeoKrom/NTUA-Intelligent-Control-Systems-and-Robotic-Systems-course/Team Project/Simulation/3. Feedback Linearizition/Normal/MATLAB/System_Response_Ref_Signal_2.png

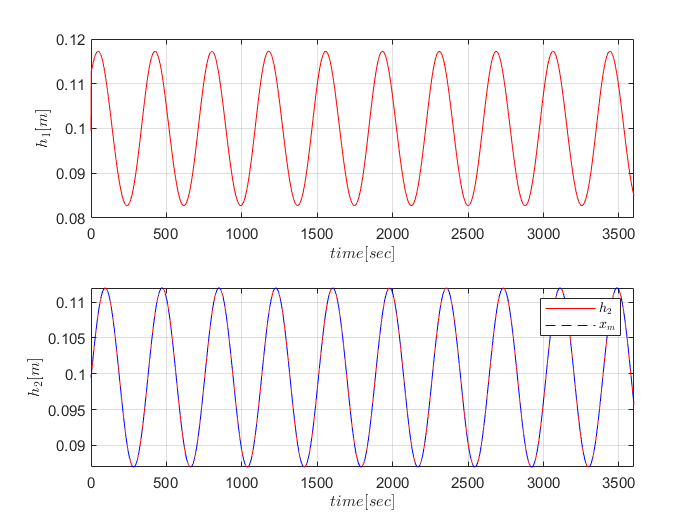
Team Project/Simulation/3. Feedback Linearizition/Normal/MATLAB/System_Response_Ref_Signal_2.png
