GeoKrom/NTUA-Intelligent-Control-Systems-and-Robotic-Systems-course/Team Project/Simulation/4. Backstepping/Adaptive/MATLAB/Error_Ref_Signal_1.png

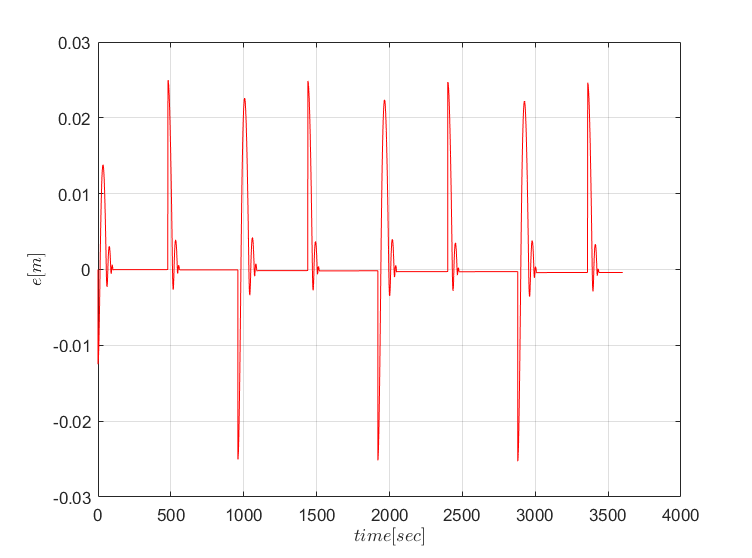
Team Project/Simulation/4. Backstepping/Adaptive/MATLAB/Error_Ref_Signal_1.png
