GeoKrom/NTUA-Intelligent-Control-Systems-and-Robotic-Systems-course/Team Project/Simulation/4. Backstepping/Adaptive/MATLAB/System_Response_Ref_Signal_3.png

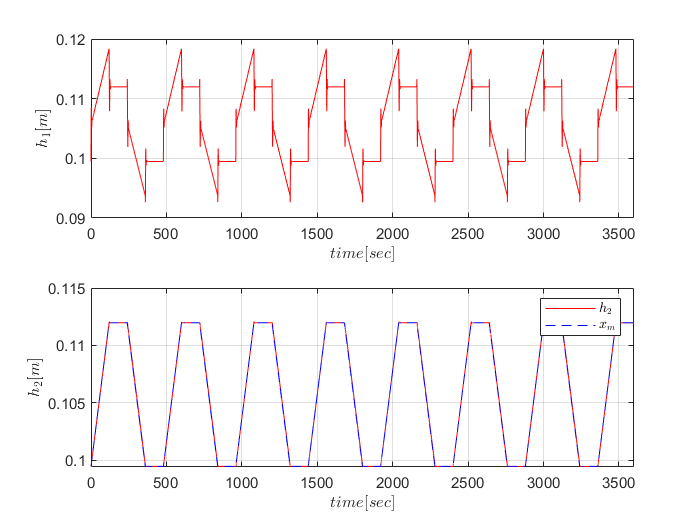
Team Project/Simulation/4. Backstepping/Adaptive/MATLAB/System_Response_Ref_Signal_3.png
