GeoKrom/NTUA-Intelligent-Control-Systems-and-Robotic-Systems-course/Team Project/Simulation/Other simulation/plots/Backstepping_Parameters.png

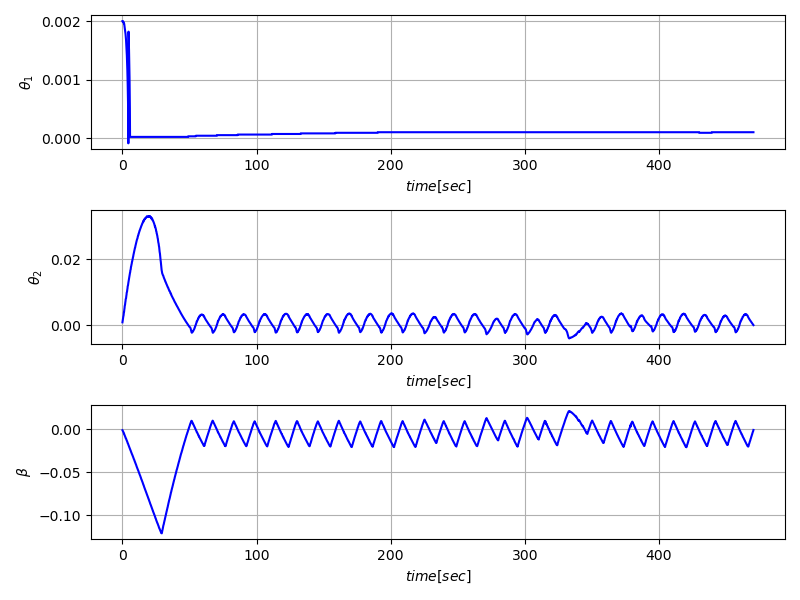
Team Project/Simulation/Other simulation/plots/Backstepping_Parameters.png
