GeoKrom/NTUA-Intelligent-Control-Systems-and-Robotic-Systems-course/Team Project/Simulation/Other simulation/plots/Feedback_Heights.png

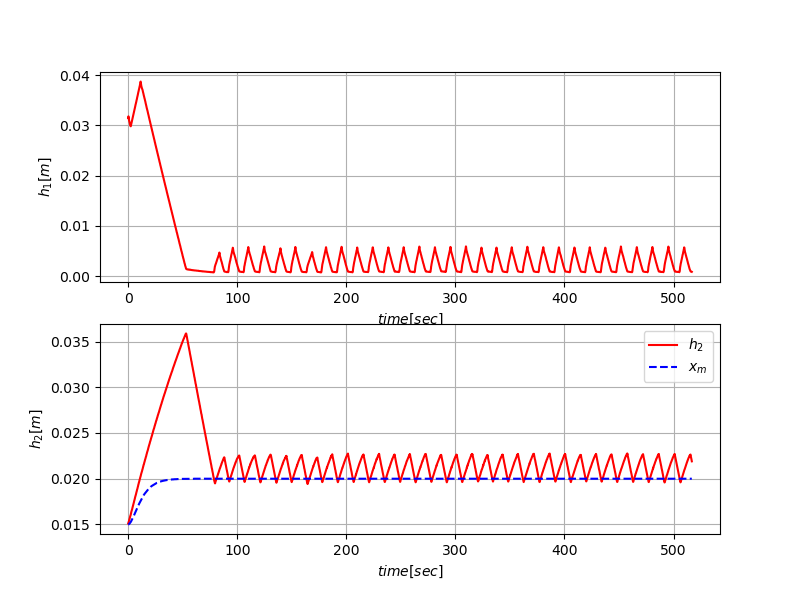
Team Project/Simulation/Other simulation/plots/Feedback_Heights.png
