GeoKrom/NTUA-Intelligent-Control-Systems-and-Robotic-Systems-course/Team Project/Simulation/Other simulation/plots/MIT_heights.png

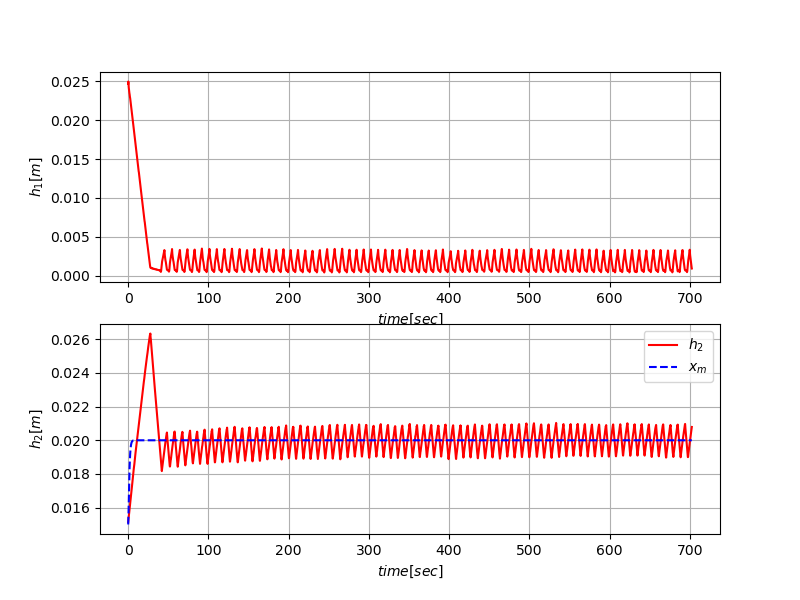
Team Project/Simulation/Other simulation/plots/MIT_heights.png
