GeoKrom/NTUA-Intelligent-Control-Systems-and-Robotic-Systems-course/Team Project/Construction Components/tank system 3.jpg

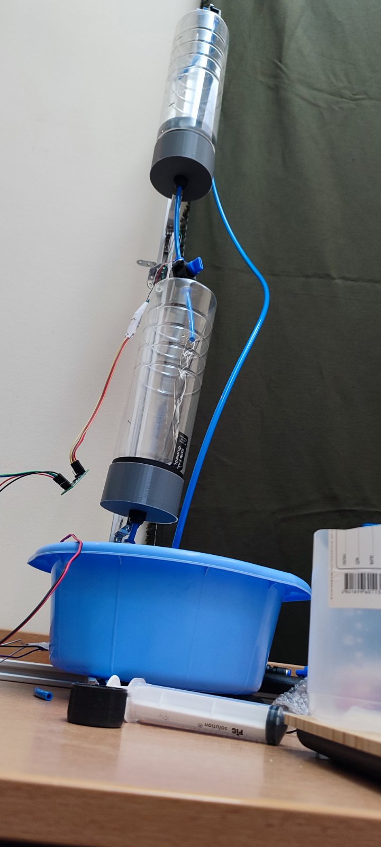
Team Project/Construction Components/tank system 3.jpg
