GeoKrom/NTUA-Intelligent-Control-Systems-and-Robotic-Systems-course/Team Project/Measurement Results/MRAC_Output.csv

 | h1 | h2 | time_arduino | time_python | state
0 | 0.0 | 0.0 | 0.0 | 1.0632905960083008 | 0
1 | 0.0 | 0.0 | 0.0 | 2.0751187801361084 | 0
2 | 0.0 | 0.0 | 0.0 | 3.0925958156585693 | 0
3 | 0.0 | 0.0 | 0.0 | 4.107531785964966 | 0
4 | 0.0 | 0.0 | 0.0 | 5.1211466789245605 | 0
5 | 0.0 | 0.0 | 0.0 | 6.135516881942749 | 0
6 | 0.0 | 0.0 | 0.0 | 7.140432119369507 | 0
7 | 0.0 | 0.0 | 0.0 | 8.153236389160156 | 0
8 | 0.0 | 0.0 | 0.0 | 9.1704580783844 | 0
9 | 0.0 | 0.0 | 0.0 | 10.17282748222351 | 0
10 | 0.0 | 0.0 | 0.0 | 11.17629337310791 | 0
11 | 0.0 | 0.0 | 0.0 | 12.188810586929321 | 0
12 | 0.0 | 0.0 | 0.0 | 13.190840721130371 | 0
13 | 0.0 | 0.0 | 0.0 | 14.194682359695435 | 0
14 | 0.0 | 0.0 | 0.0 | 15.200514793395996 | 0
15 | 0.0 | 0.0 | 0.0 | 16.210400819778442 | 0
16 | 0.0 | 0.0 | 0.0 | 17.2222843170166 | 0
17 | 0.0 | 0.0 | 0.0 | 18.237853527069092 | 0
18 | 0.0 | 0.0 | 0.0 | 19.250712633132935 | 0
19 | 0.0 | 0.0 | 0.0 | 20.264145612716675 | 0
20 | 0.0 | 0.0 | 0.0 | 21.281250953674316 | 0
21 | 0.0 | 0.0 | 0.0 | 22.290118932724 | 0
22 | 0.0 | 0.0 | 0.0 | 23.307650327682495 | 0
23 | 0.0 | 0.0 | 0.0 | 24.31842803955078 | 0
24 | 0.0 | 0.0 | 0.0 | 25.320810794830322 | 0
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
