GeoKrom/NTUA-Intelligent-Control-Systems-and-Robotic-Systems-course/Team Project/Measurement Results/MIT_Output.csv

 | h2_input | xm | time_arduino | time_python | volt | law | e | h1 | h2 | xm | xm_dot | theta1 | theta2 | theta3 | filter1 | filter1_dot | filter2 | filter2_dot | filter3 | filter3_dot | ola (x1000)
47 | 20.08 | 20 | 45838 | 46.51605201 | 51 | 1.1 | 0.12 | 34.73 | 20.12 | 0 | 4 | 200000 | 60000 | 150000 | 0 | 4 | 0 | 5.8 | 0 | 0.03
48 | 20.12 | 20.4 | 46012 | 46.69127154 | 51 | 1.08 | -0.18 | 34.87 | 20.22 | 0.4 | 6.4 | 200000 | 60000 | 150000 | 0.4 | 6.4 | 0.58 | 9.37 | 0 | 0.07
49 | 20.22 | 21.04 | 46187 | 46.86834931 | 51 | 1.06 | -0.75 | 34.98 | 20.29 | 1.04 | 7.68 | 200000.07 | 59999.89 | 150000 | 1.04 | 7.68 | 1.52 | 11.34 | 0.01 | 0.13
50 | 20.29 | 21.81 | 46363 | 47.04344416 | 51 | 1.04 | -1.42 | 35.07 | 20.39 | 1.81 | 8.19 | 200000.85 | 59998.75 | 149999.98 | 1.81 | 8.19 | 2.65 | 12.19 | 0.02 | 0.19
51 | 20.39 | 22.63 | 46539 | 47.21957922 | 51 | 1.02 | -2.17 | 35.21 | 20.46 | 2.63 | 8.19 | 200003.42 | 59994.99 | 149999.95 | 2.63 | 8.19 | 3.87 | 12.28 | 0.04 | 0.26
52 | 20.46 | 23.45 | 46715 | 47.39547038 | 51 | 1 | -2.88 | 35.31 | 20.57 | 3.45 | 7.86 | 200009.1 | 59986.6 | 149999.85 | 3.45 | 7.86 | 5.1 | 11.9 | 0.07 | 0.32
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
